alessandro-satanassi/OpenFIRE-PICON-ESP32/web/images/010---telaio_sotto_pompa_posteriore.png

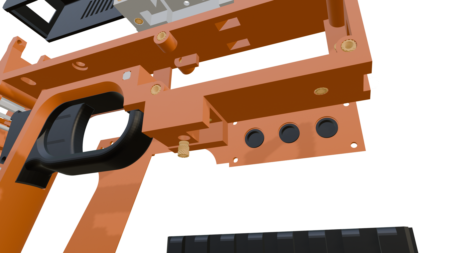
web/images/010---telaio_sotto_pompa_posteriore.png
