alessandro-satanassi/OpenFIRE-PICON-ESP32/web/images/viti_testa_piatta.jpg

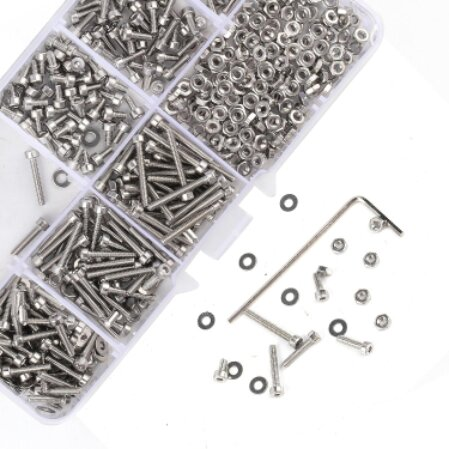
web/images/viti_testa_piatta.jpg
