alessandro-satanassi/OpenFIRE-PICON-ESP32/web/files/006---supporto_solenoide_dx.png

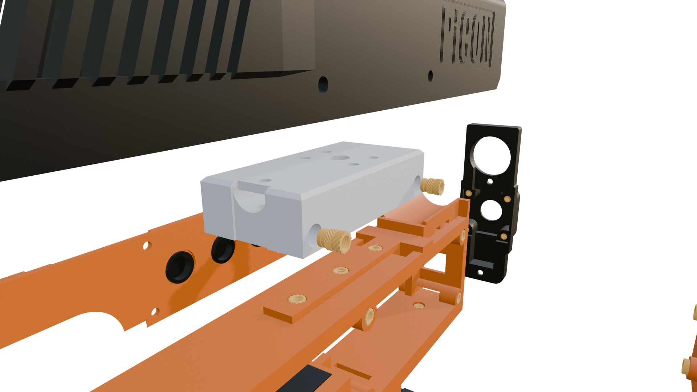
web/files/006---supporto_solenoide_dx.png
