alessandro-satanassi/OpenFIRE-PICON-ESP32/web/files/06_cc05z4l9.jpeg

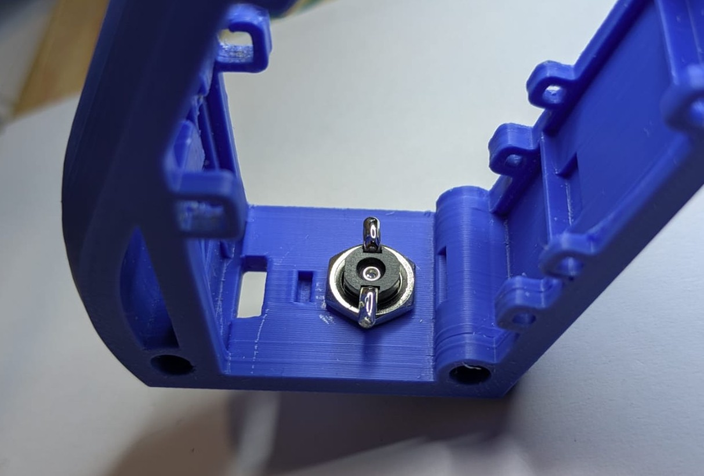
web/files/06_cc05z4l9.jpeg
