alessandro-satanassi/OpenFIRE-PICON-ESP32/web/gallery/06.jpg

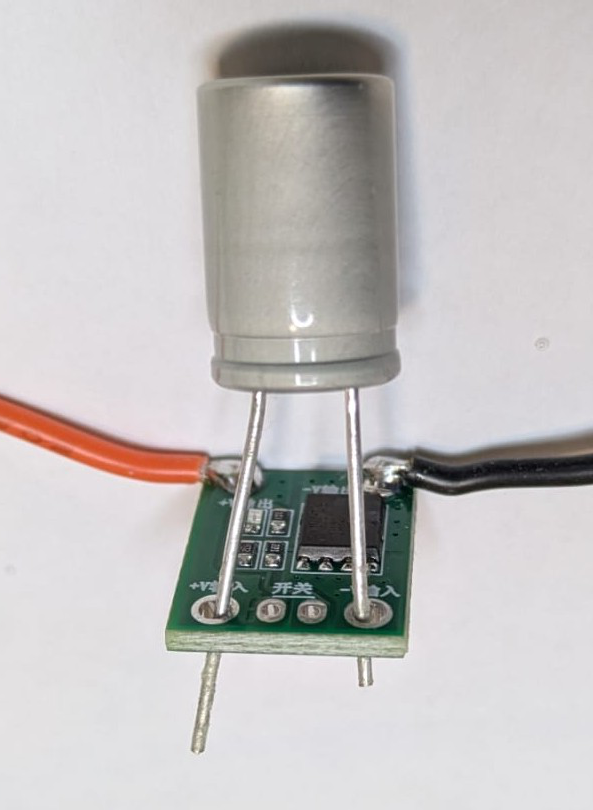
web/gallery/06.jpg
