alessandro-satanassi/OpenFIRE-PICON-ESP32/web/gallery/06_thumb_eejymhjs.png

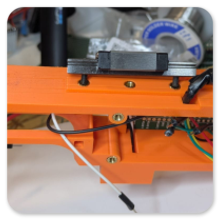
web/gallery/06_thumb_eejymhjs.png
