alessandro-satanassi/OpenFIRE-PICON-ESP32/web/gallery/10_thumb_l9mox1hs.png

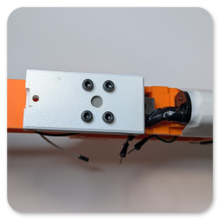
web/gallery/10_thumb_l9mox1hs.png
