alessandro-satanassi/OpenFIRE-PICON-ESP32/web/gallery/10_thumb_tlurzcni.png

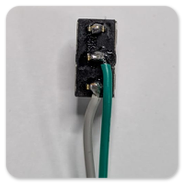
web/gallery/10_thumb_tlurzcni.png
