alessandro-satanassi/OpenFIRE-PICON-ESP32/web/gallery/16_thumb_evzkav5x.png

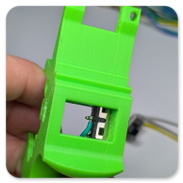
web/gallery/16_thumb_evzkav5x.png
