alessandro-satanassi/OpenFIRE-PICON-ESP32/web/gallery/17.jpg

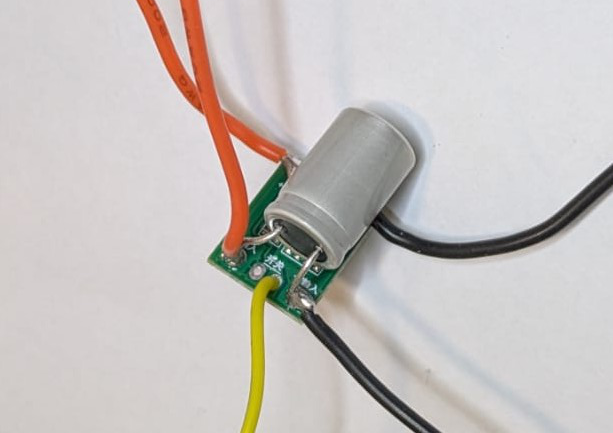
web/gallery/17.jpg
