alessandro-satanassi/OpenFIRE-PICON-ESP32/web/gallery/WhatsApp-Image-2026-08-09-at-01.59.08--3-.jpg

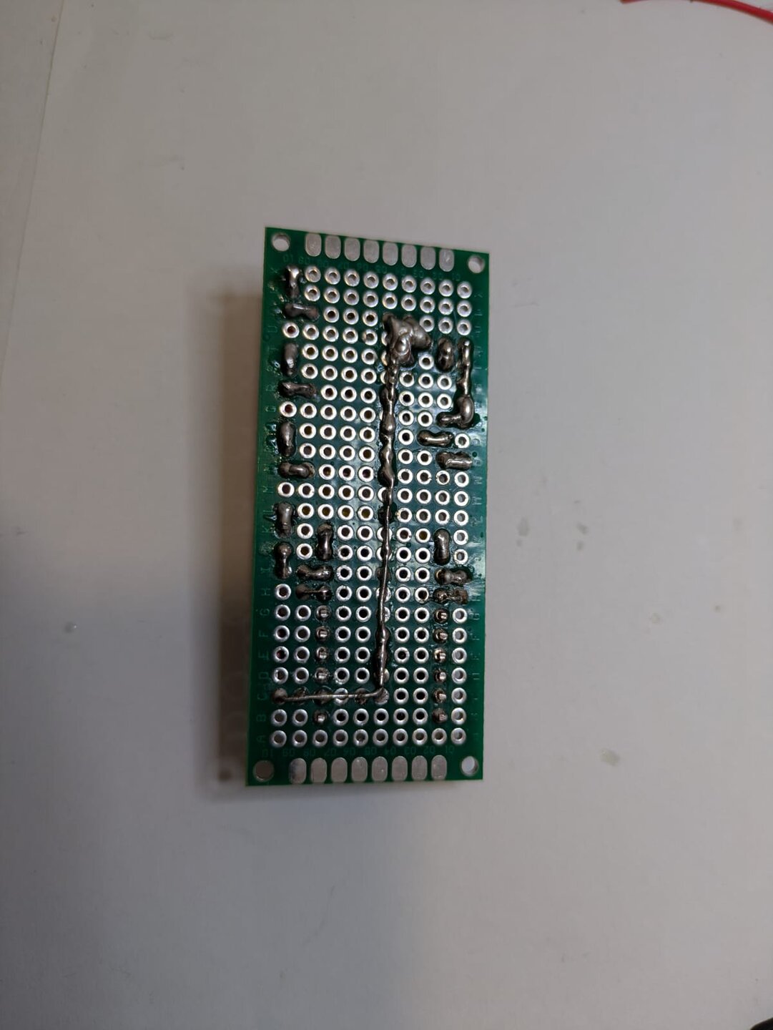
web/gallery/WhatsApp-Image-2026-08-09-at-01.59.08--3-.jpg
