alessandro-satanassi/OpenFIRE-PICON-ESP32/web/images/00.jpg

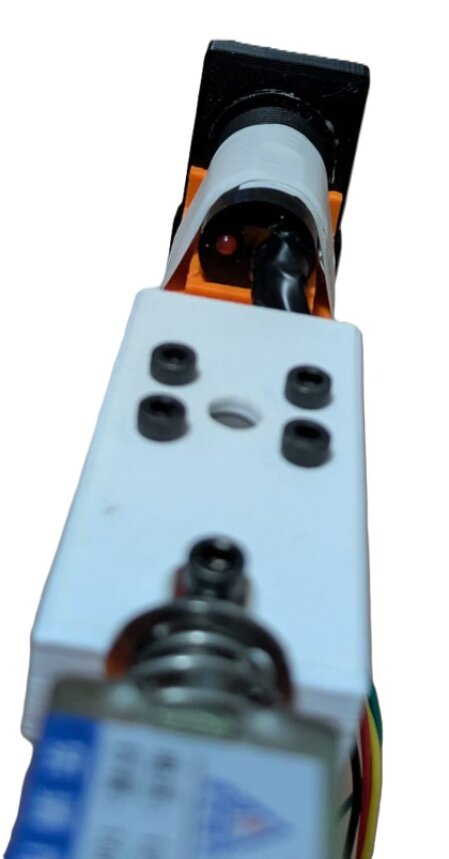
web/images/00.jpg
