alessandro-satanassi/OpenFIRE-PICON-ESP32/web/images/001---blocco-guida-rail.png

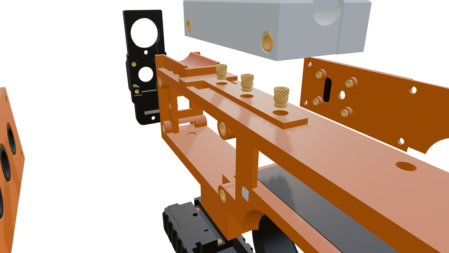
web/images/001---blocco-guida-rail.png
