alessandro-satanassi/OpenFIRE-PICON-ESP32/web/images/01.jpg

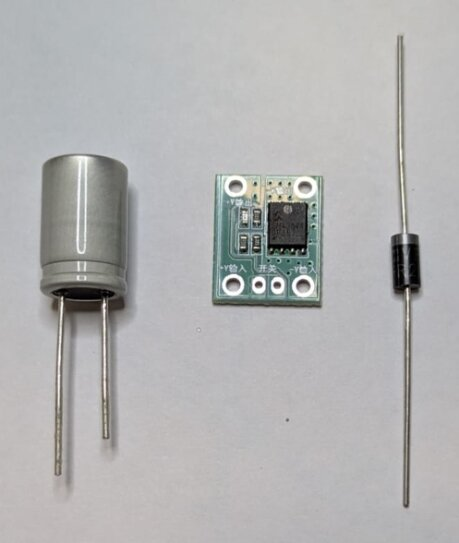
web/images/01.jpg
