alessandro-satanassi/OpenFIRE-PICON-ESP32/web/images/1.jpg

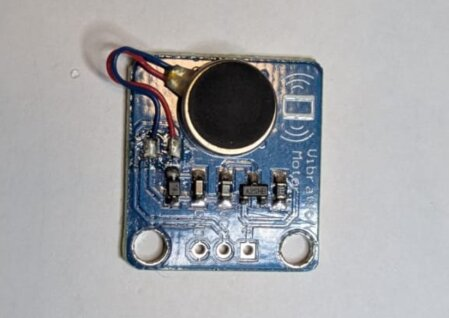
web/images/1.jpg
