alessandro-satanassi/OpenFIRE-PICON-ESP32/web/images/01_2w0nyasc.jpg

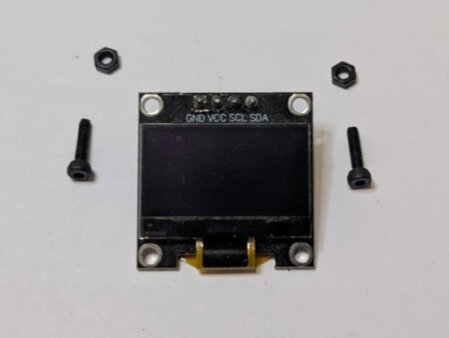
web/images/01_2w0nyasc.jpg
