alessandro-satanassi/OpenFIRE-PICON-ESP32/web/images/01_5xzmrs7f.jpg

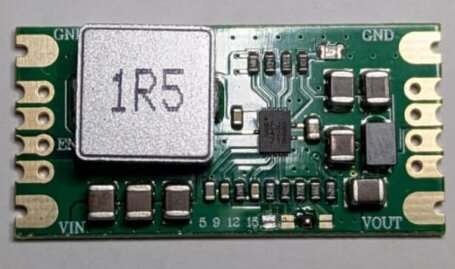
web/images/01_5xzmrs7f.jpg
