alessandro-satanassi/OpenFIRE-PICON-ESP32/web/images/01_8k7r30k3.jpg

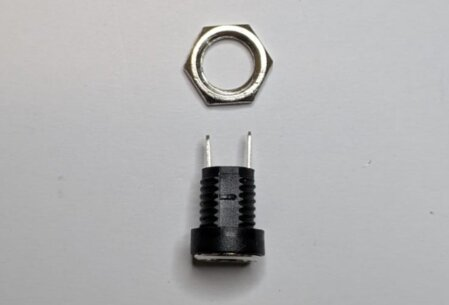
web/images/01_8k7r30k3.jpg
