alessandro-satanassi/OpenFIRE-PICON-ESP32/web/images/01_8mr3n87f.jpg

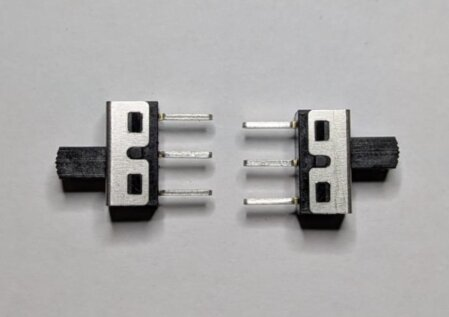
web/images/01_8mr3n87f.jpg
