alessandro-satanassi/OpenFIRE-PICON-ESP32/web/files/01_0ub3t0rs.jpeg

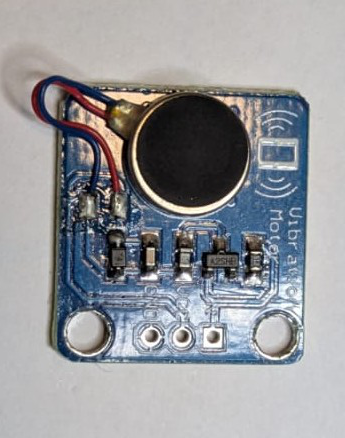
web/images/01_f4iyjq4a.jpg
