alessandro-satanassi/OpenFIRE-PICON-ESP32/web/files/01_5zxbnlnv.jpeg

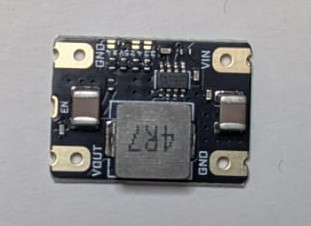
web/images/01_g9jfmoby.jpg
