alessandro-satanassi/OpenFIRE-PICON-ESP32/web/images/01_GRILLETTO.jpg

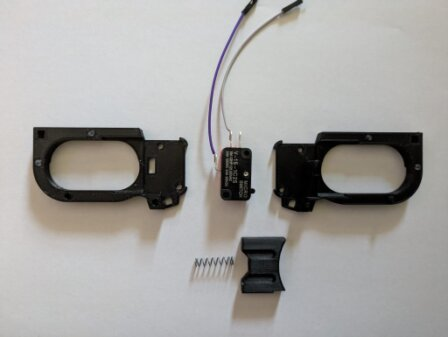
web/images/01_GRILLETTO.jpg
