alessandro-satanassi/OpenFIRE-PICON-ESP32/web/images/01_LENTE.jpg

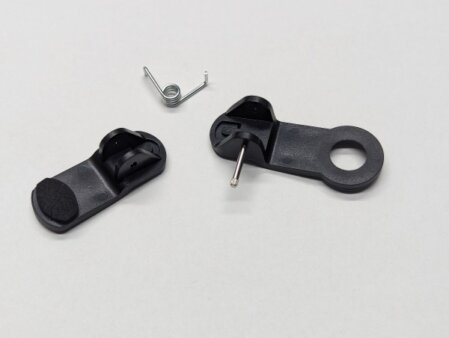
web/images/01_LENTE.jpg
