alessandro-satanassi/OpenFIRE-PICON-ESP32/web/images/01_mn38d8ug.jpg

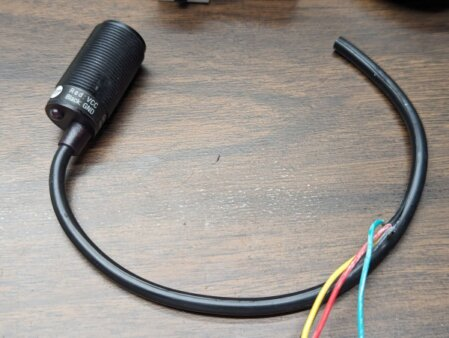
web/images/01_mn38d8ug.jpg
