alessandro-satanassi/OpenFIRE-PICON-ESP32/web/images/01_neopixel.jpg

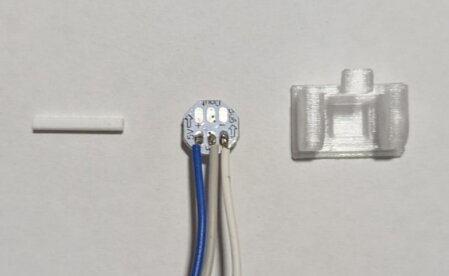
web/images/01_neopixel.jpg
