alessandro-satanassi/OpenFIRE-PICON-ESP32/web/images/01_POMPA.jpg

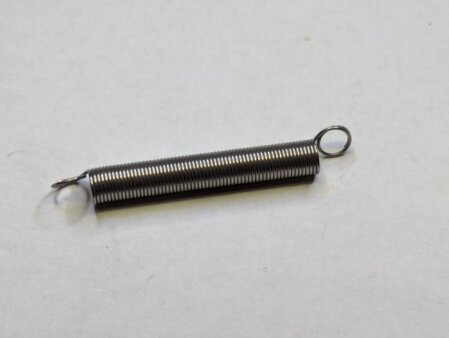
web/images/01_POMPA.jpg
