alessandro-satanassi/OpenFIRE-PICON-ESP32/web/images/01_switch_pompa.jpg

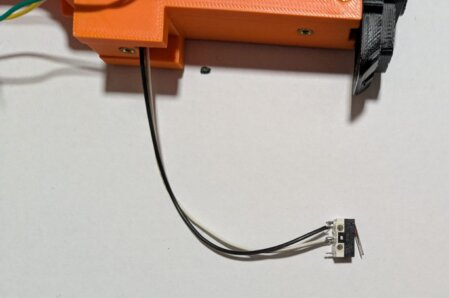
web/images/01_switch_pompa.jpg
