alessandro-satanassi/OpenFIRE-PICON-ESP32/web/images/002---telaio_sx.png

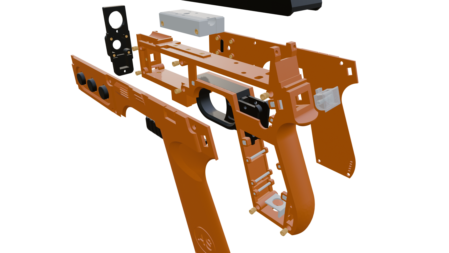
web/images/002---telaio_sx.png
