alessandro-satanassi/OpenFIRE-PICON-ESP32/web/images/02.jpg

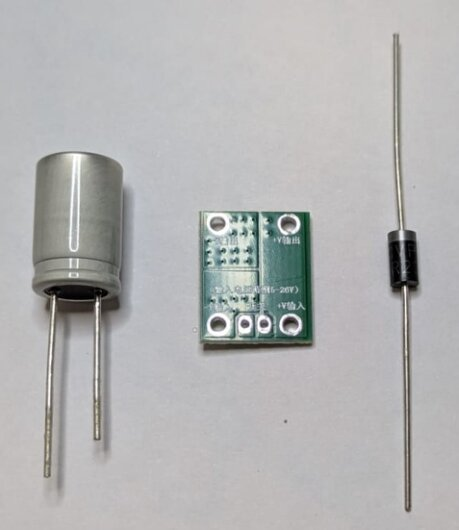
web/images/02.jpg
