alessandro-satanassi/OpenFIRE-PICON-ESP32/web/images/2.jpg

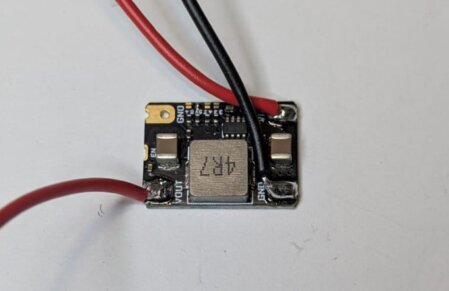
web/images/2.jpg
