alessandro-satanassi/OpenFIRE-PICON-ESP32/web/files/02_2sauoesy.jpeg

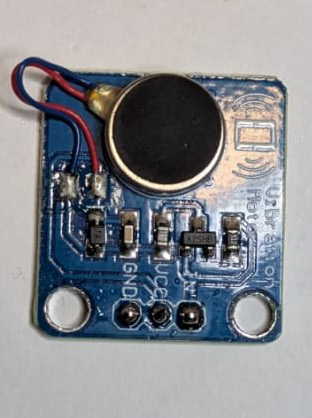
web/images/02_4r1xh5xk.jpg
