alessandro-satanassi/OpenFIRE-PICON-ESP32/web/files/02_3oflzan2.jpeg

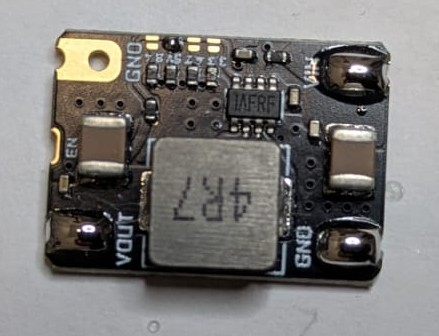
web/images/02_5logg1c5.jpg
