alessandro-satanassi/OpenFIRE-PICON-ESP32/web/images/02_GRILLETTO.jpg

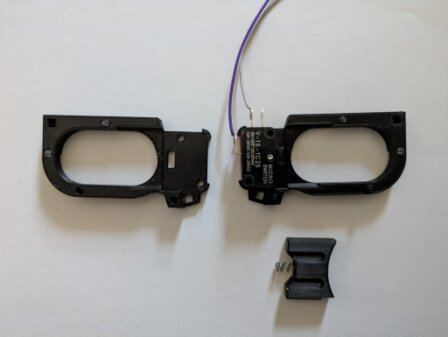
web/images/02_GRILLETTO.jpg
