alessandro-satanassi/OpenFIRE-PICON-ESP32/web/images/02_LENTE.jpg

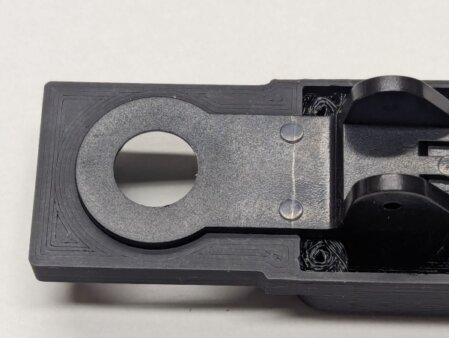
web/images/02_LENTE.jpg
