alessandro-satanassi/OpenFIRE-PICON-ESP32/web/images/02_neopixel.jpg

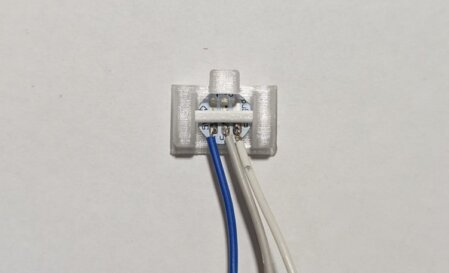
web/images/02_neopixel.jpg
