alessandro-satanassi/OpenFIRE-PICON-ESP32/web/images/02_POMPA.jpg

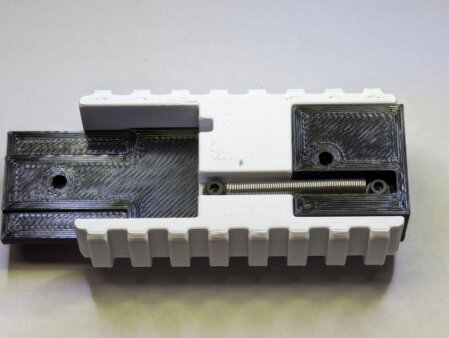
web/images/02_POMPA.jpg
