alessandro-satanassi/OpenFIRE-PICON-ESP32/web/images/02_r8t4q5sc.jpg

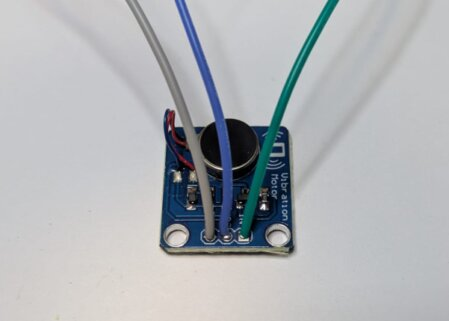
web/images/02_r8t4q5sc.jpg
