alessandro-satanassi/OpenFIRE-PICON-ESP32/web/images/02_ruzfydre.jpg

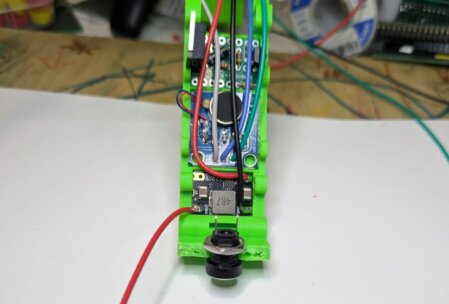
web/images/02_ruzfydre.jpg
