alessandro-satanassi/OpenFIRE-PICON-ESP32/web/images/02_sebupyjk.jpg

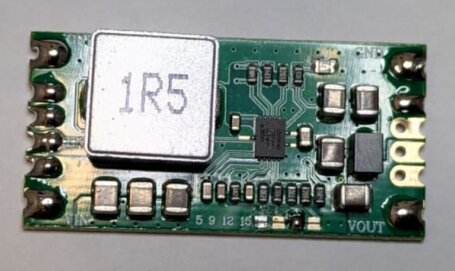
web/images/02_sebupyjk.jpg
