alessandro-satanassi/OpenFIRE-PICON-ESP32/web/images/02_switch_pompa.jpg

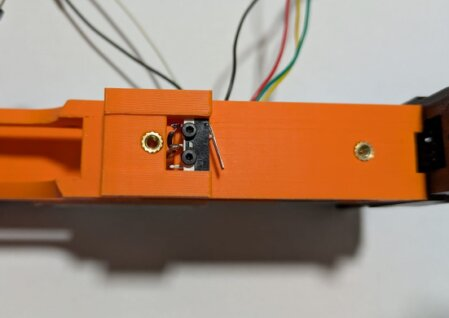
web/images/02_switch_pompa.jpg
