alessandro-satanassi/OpenFIRE-PICON-ESP32/web/images/02_t7jg1n2v.jpg

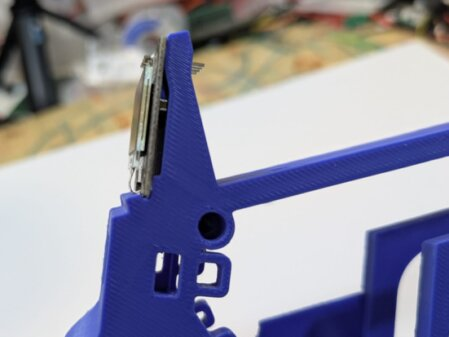
web/images/02_t7jg1n2v.jpg
