alessandro-satanassi/OpenFIRE-PICON-ESP32/web/images/02_ymkqmdek.jpg

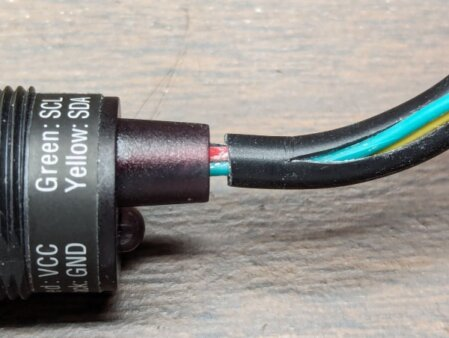
web/images/02_ymkqmdek.jpg
