alessandro-satanassi/OpenFIRE-PICON-ESP32/web/images/02_yrchzzac.jpg

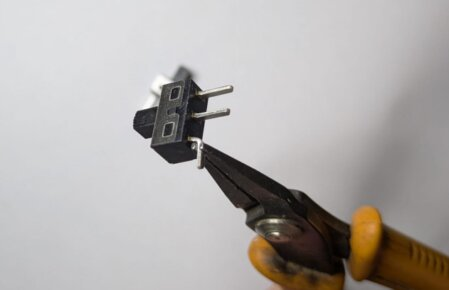
web/images/02_yrchzzac.jpg
