alessandro-satanassi/OpenFIRE-PICON-ESP32/web/images/003---telaio_dx.png

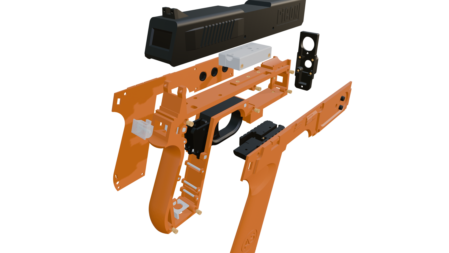
web/images/003---telaio_dx.png
