alessandro-satanassi/OpenFIRE-PICON-ESP32/web/images/03.jpg

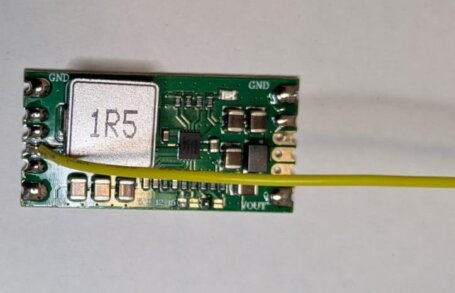
web/images/03.jpg
