alessandro-satanassi/OpenFIRE-PICON-ESP32/web/images/3.jpg

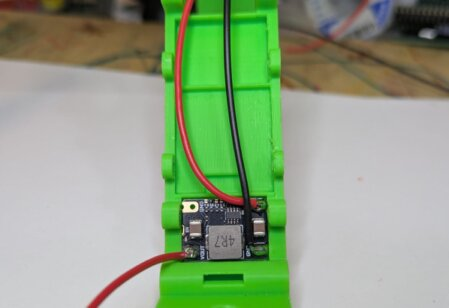
web/images/3.jpg
