alessandro-satanassi/OpenFIRE-PICON-ESP32/web/images/003.png

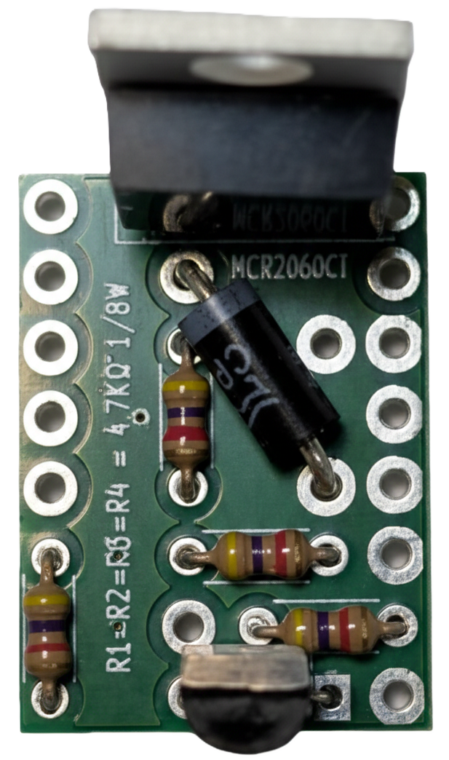
web/images/003.png
