alessandro-satanassi/OpenFIRE-PICON-ESP32/web/images/03_524w5b3q.jpg

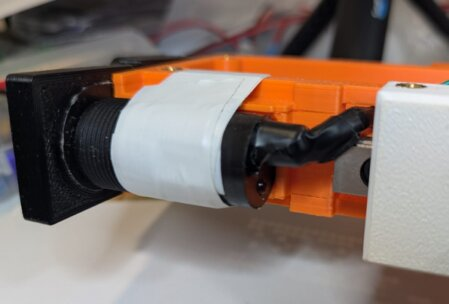
web/images/03_524w5b3q.jpg
