alessandro-satanassi/OpenFIRE-PICON-ESP32/web/images/03_gcl5vufi.jpg

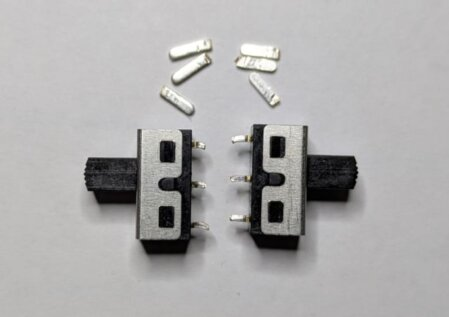
web/images/03_gcl5vufi.jpg
