alessandro-satanassi/OpenFIRE-PICON-ESP32/web/images/03_GRILLETTO.jpg

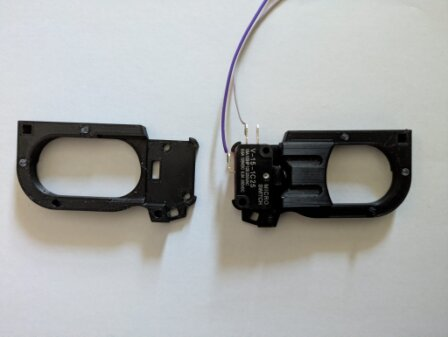
web/images/03_GRILLETTO.jpg
