alessandro-satanassi/OpenFIRE-PICON-ESP32/web/images/03_iws1d3v5.jpg

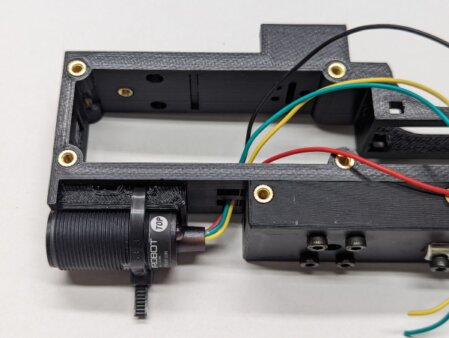
web/images/03_iws1d3v5.jpg
