alessandro-satanassi/OpenFIRE-PICON-ESP32/web/images/03_LENTE.jpg

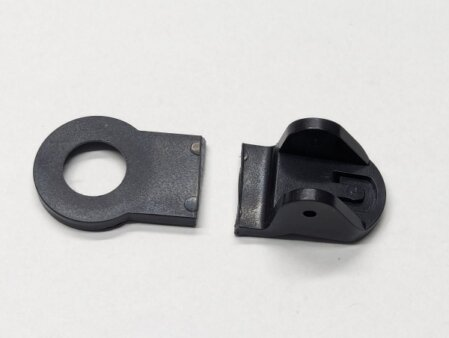
web/images/03_LENTE.jpg
