alessandro-satanassi/OpenFIRE-PICON-ESP32/web/images/03_lwsuhsz6.jpg

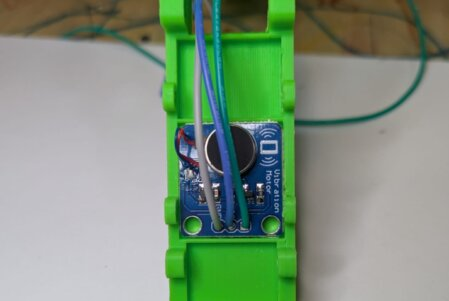
web/images/03_lwsuhsz6.jpg
