alessandro-satanassi/OpenFIRE-PICON-ESP32/web/images/03_neopixel.jpg

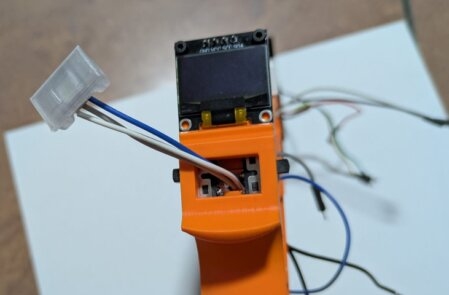
web/images/03_neopixel.jpg
