alessandro-satanassi/OpenFIRE-PICON-ESP32/web/images/03_pfckra2t.jpg

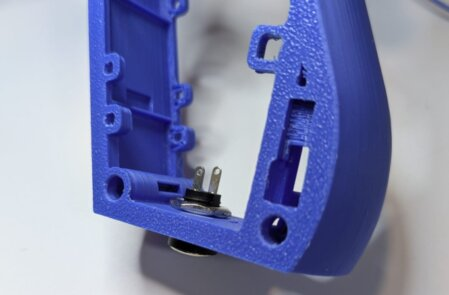
web/images/03_pfckra2t.jpg
