alessandro-satanassi/OpenFIRE-PICON-ESP32/web/images/03_POMPA.jpg

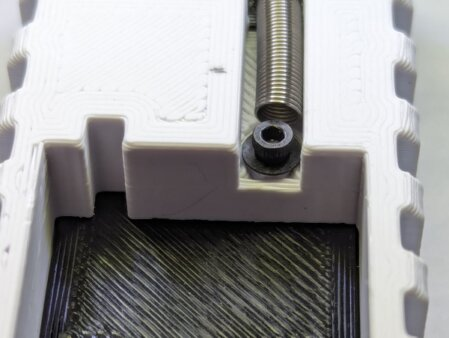
web/images/03_POMPA.jpg
