alessandro-satanassi/OpenFIRE-PICON-ESP32/web/images/03_sllk6pq8.jpg

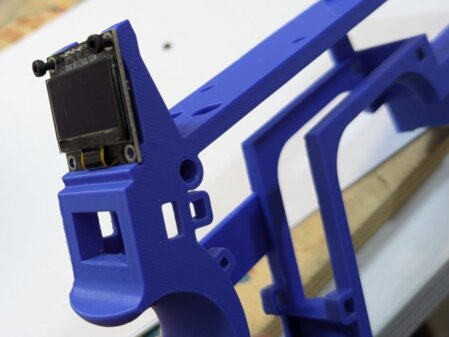
web/images/03_sllk6pq8.jpg
