alessandro-satanassi/OpenFIRE-PICON-ESP32/web/images/03_switch_pompa.jpg

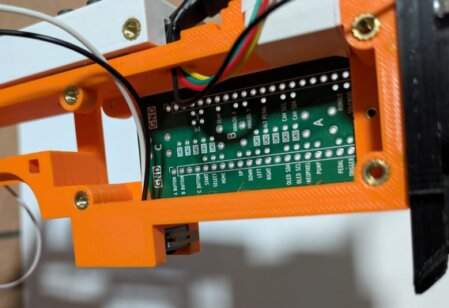
web/images/03_switch_pompa.jpg
