alessandro-satanassi/OpenFIRE-PICON-ESP32/web/images/004---blocco-braccio-solenoide.png

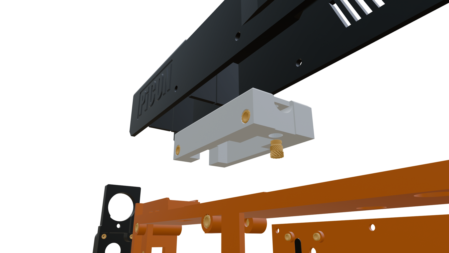
web/images/004---blocco-braccio-solenoide.png
