alessandro-satanassi/OpenFIRE-PICON-ESP32/web/images/04.jpg

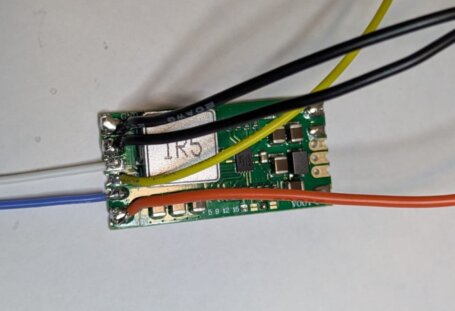
web/images/04.jpg
