alessandro-satanassi/OpenFIRE-PICON-ESP32/web/images/04_2t98dg83.jpg

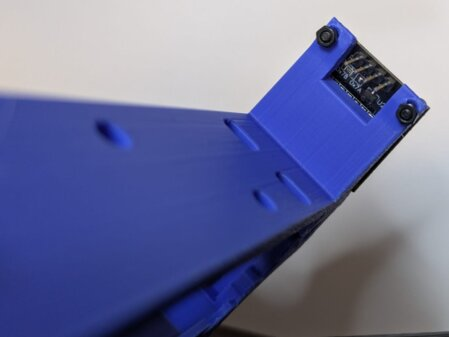
web/images/04_2t98dg83.jpg
