alessandro-satanassi/OpenFIRE-PICON-ESP32/web/images/04_GRILLETTO.jpg

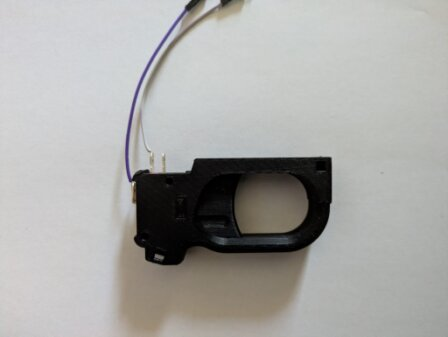
web/images/04_GRILLETTO.jpg
