alessandro-satanassi/OpenFIRE-PICON-ESP32/web/images/04_LENTE.jpg

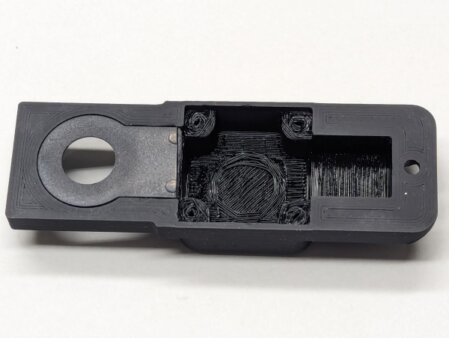
web/images/04_LENTE.jpg
