alessandro-satanassi/OpenFIRE-PICON-ESP32/web/images/04_n981k5cl.jpg

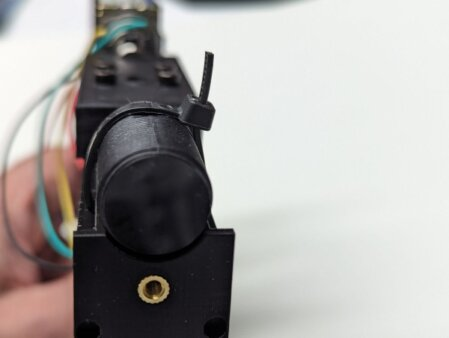
web/images/04_n981k5cl.jpg
