alessandro-satanassi/OpenFIRE-PICON-ESP32/web/images/04_neopixel.jpg

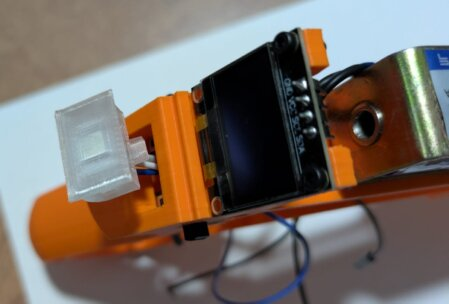
web/images/04_neopixel.jpg
