alessandro-satanassi/OpenFIRE-PICON-ESP32/web/images/04_nu273c6r.jpg

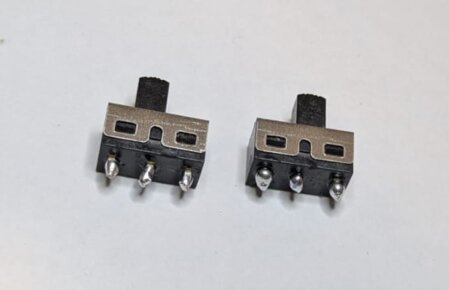
web/images/04_nu273c6r.jpg
