alessandro-satanassi/OpenFIRE-PICON-ESP32/web/images/04_u2wgebxg.jpg

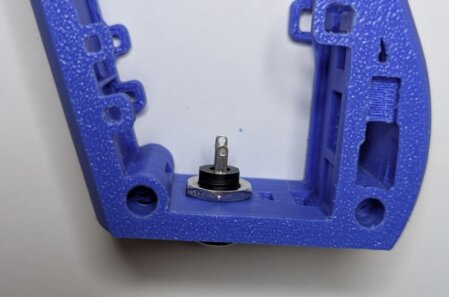
web/images/04_u2wgebxg.jpg
