alessandro-satanassi/OpenFIRE-PICON-ESP32/web/images/005---supporto_solenoide_sx.png

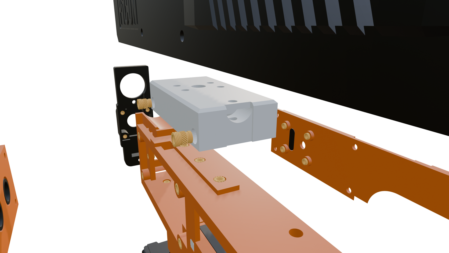
web/images/005---supporto_solenoide_sx.png
