alessandro-satanassi/OpenFIRE-PICON-ESP32/web/images/05.jpg

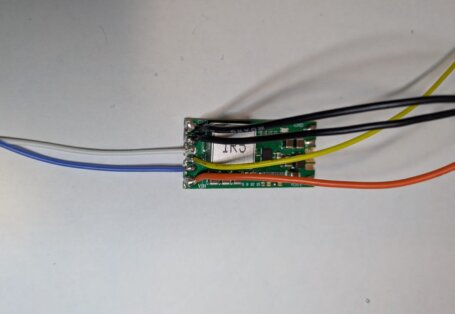
web/images/05.jpg
