alessandro-satanassi/OpenFIRE-PICON-ESP32/web/images/005.png

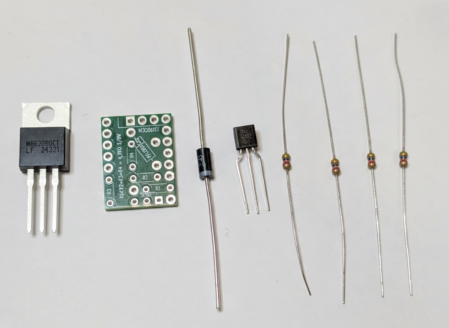
web/images/005.png
