alessandro-satanassi/OpenFIRE-PICON-ESP32/web/images/05_bi0squd6.jpg

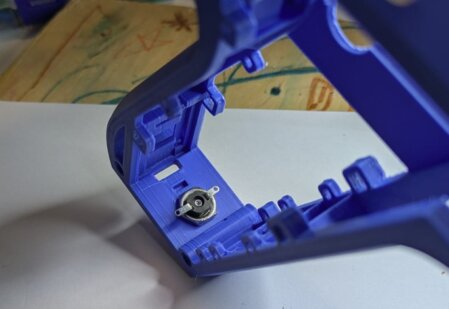
web/images/05_bi0squd6.jpg
