alessandro-satanassi/OpenFIRE-PICON-ESP32/web/images/05_diop4fx3.jpg

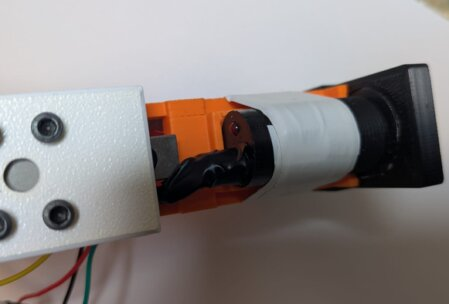
web/images/05_diop4fx3.jpg
