alessandro-satanassi/OpenFIRE-PICON-ESP32/web/images/05_GRILLETTO.jpg

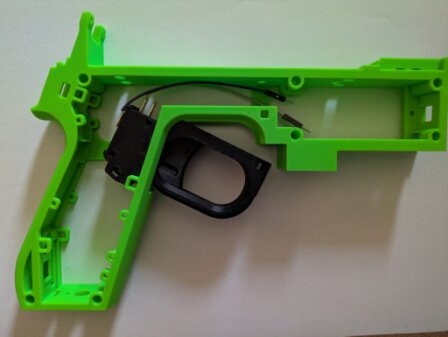
web/images/05_GRILLETTO.jpg
