alessandro-satanassi/OpenFIRE-PICON-ESP32/web/images/05_LENTE.jpg

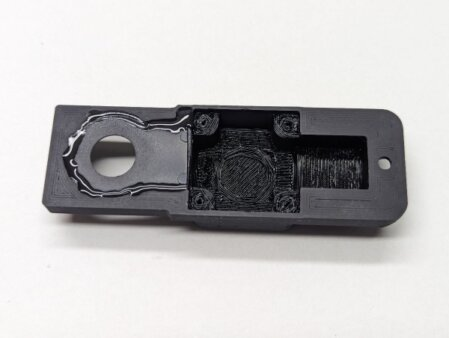
web/images/05_LENTE.jpg
