alessandro-satanassi/OpenFIRE-PICON-ESP32/web/images/05_neopixel.jpg

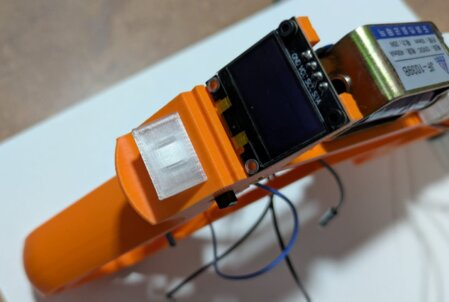
web/images/05_neopixel.jpg
