alessandro-satanassi/OpenFIRE-PICON-ESP32/web/images/05_odr75ruc.jpg

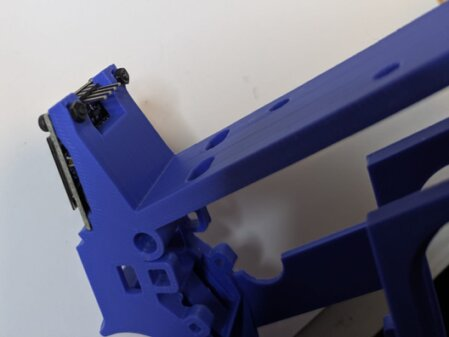
web/images/05_odr75ruc.jpg
