alessandro-satanassi/OpenFIRE-PICON-ESP32/web/images/06.jpg

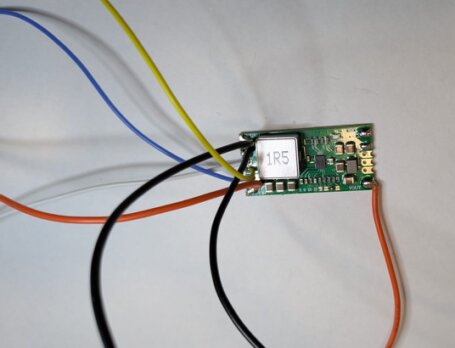
web/images/06.jpg
