alessandro-satanassi/OpenFIRE-PICON-ESP32/web/images/06_d0qdcc5i.jpg

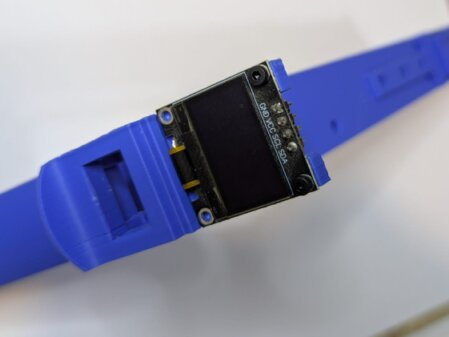
web/images/06_d0qdcc5i.jpg
