alessandro-satanassi/OpenFIRE-PICON-ESP32/web/images/06_GRILLETTO.jpg

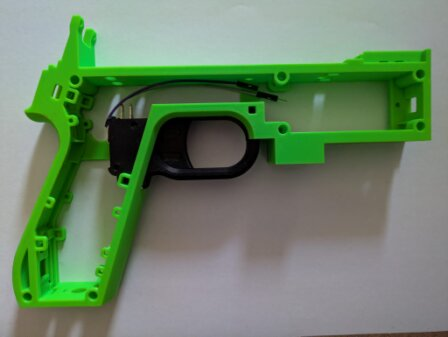
web/images/06_GRILLETTO.jpg
