alessandro-satanassi/OpenFIRE-PICON-ESP32/web/images/06_LENTE.jpg

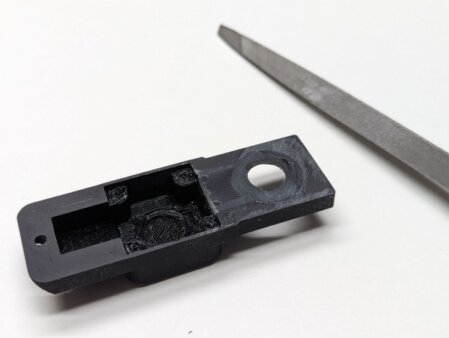
web/images/06_LENTE.jpg
