alessandro-satanassi/OpenFIRE-PICON-ESP32/web/images/06_neopixel.jpg

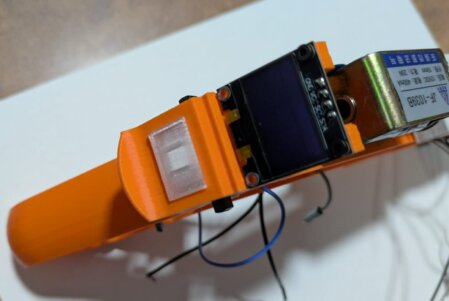
web/images/06_neopixel.jpg
