alessandro-satanassi/OpenFIRE-PICON-ESP32/web/images/06_vsywxsd8.jpg

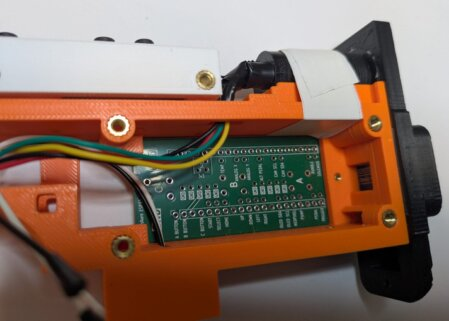
web/images/06_vsywxsd8.jpg
