alessandro-satanassi/OpenFIRE-PICON-ESP32/web/images/007---supporto_micro.png

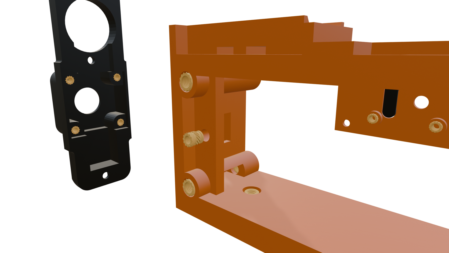
web/images/007---supporto_micro.png
