alessandro-satanassi/OpenFIRE-PICON-ESP32/web/images/07.jpg

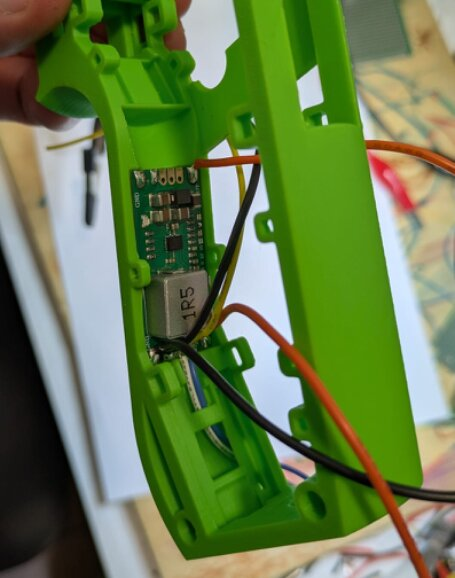
web/images/07.jpg
