alessandro-satanassi/OpenFIRE-PICON-ESP32/web/images/008---anteriore_telaio.png

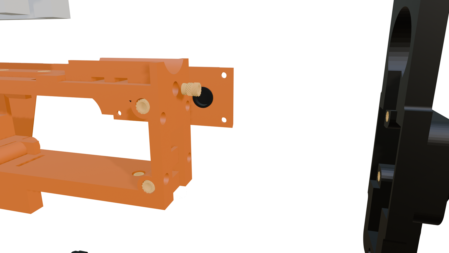
web/images/008---anteriore_telaio.png
