alessandro-satanassi/OpenFIRE-PICON-ESP32/web/images/08.jpg

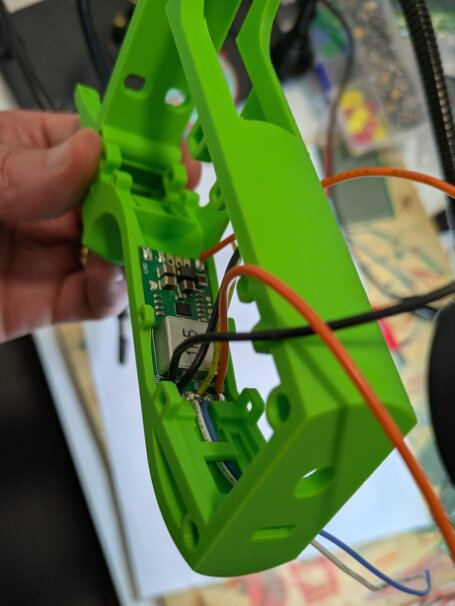
web/images/08.jpg
