alessandro-satanassi/OpenFIRE-PICON-ESP32/web/images/009---telaio_sotto_pompa_anteriore.png

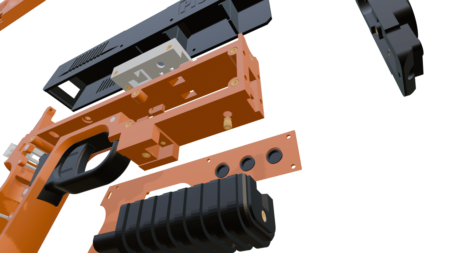
web/images/009---telaio_sotto_pompa_anteriore.png
