alessandro-satanassi/OpenFIRE-PICON-ESP32/web/images/09.jpg

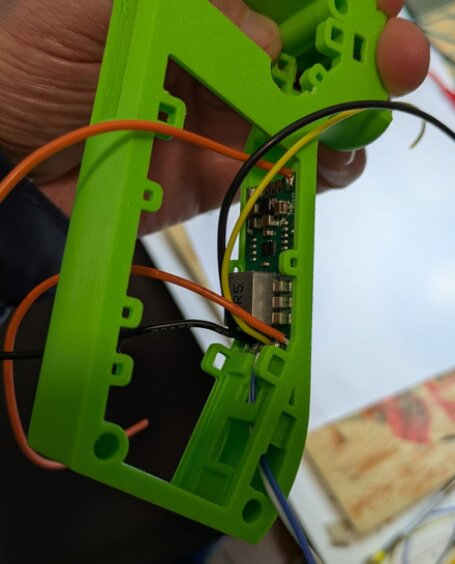
web/images/09.jpg
