alessandro-satanassi/OpenFIRE-PICON-ESP32/web/images/011---telaio_sotto_pompa_vlocco_switch.png

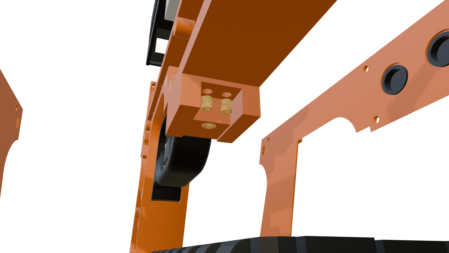
web/images/011---telaio_sotto_pompa_vlocco_switch.png
