alessandro-satanassi/OpenFIRE-PICON-ESP32/web/images/012---lato_dx_dpad_5d.png

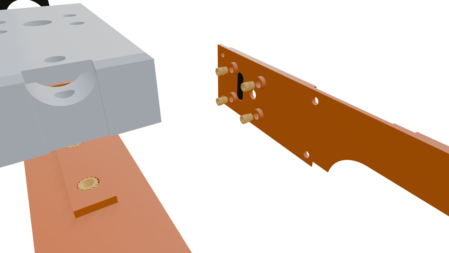
web/images/012---lato_dx_dpad_5d.png
