alessandro-satanassi/OpenFIRE-PICON-ESP32/web/images/013---supporto_joystick.png

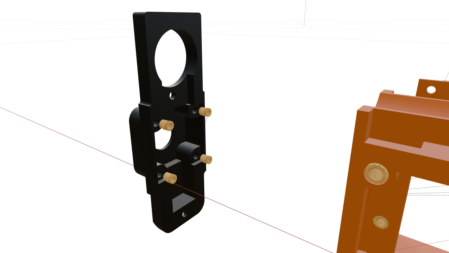
web/images/013---supporto_joystick.png
