alessandro-satanassi/OpenFIRE-PICON-ESP32/web/images/014---meccanismo_pompa_frontale.png

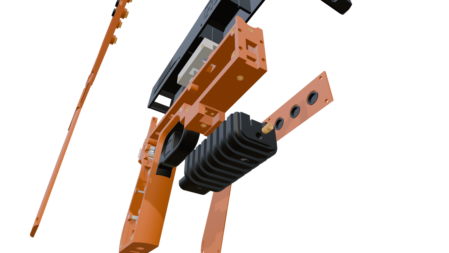
web/images/014---meccanismo_pompa_frontale.png
