alessandro-satanassi/OpenFIRE-PICON-ESP32/web/images/015---meccanismo_pompa_fermi_molla.png

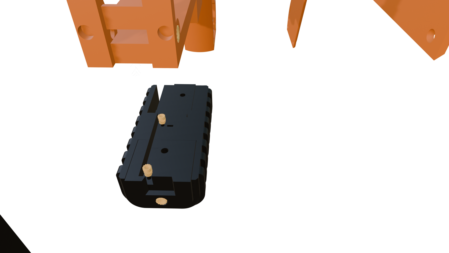
web/images/015---meccanismo_pompa_fermi_molla.png
