alessandro-satanassi/OpenFIRE-PICON-ESP32/web/images/Adafruit-BQ25185_7053r53b.png

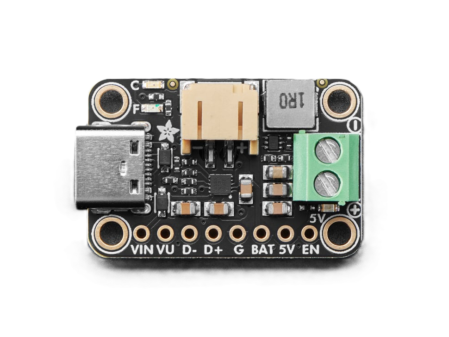
web/images/Adafruit-BQ25185_7053r53b.png
