alessandro-satanassi/OpenFIRE-PICON-ESP32/web/images/alimentatore_USB_5V_1A.png

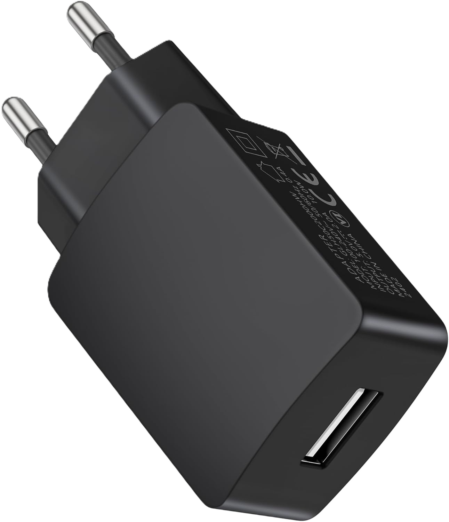
web/images/alimentatore_USB_5V_1A.png
