alessandro-satanassi/OpenFIRE-PICON-ESP32/web/images/alimentazione_3D_lato_componenti.jpg

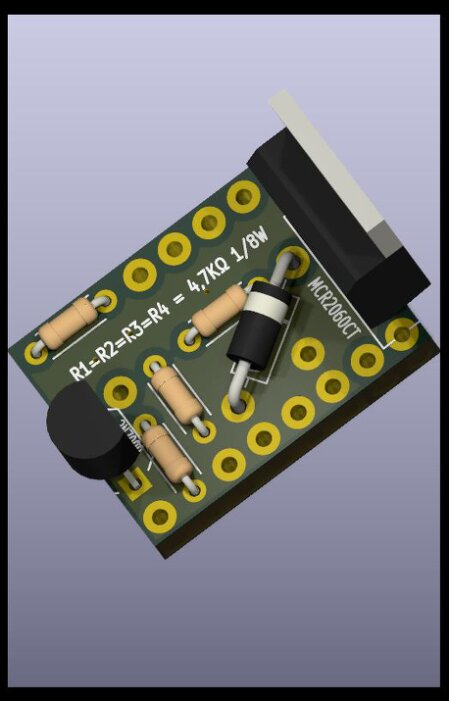
web/images/alimentazione_3D_lato_componenti.jpg
