alessandro-satanassi/OpenFIRE-PICON-ESP32/web/images/Base.png

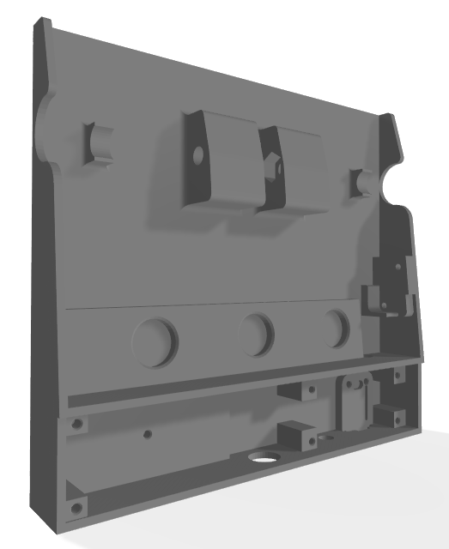
web/images/Base.png
