alessandro-satanassi/OpenFIRE-PICON-ESP32/web/images/Base_Batt.png

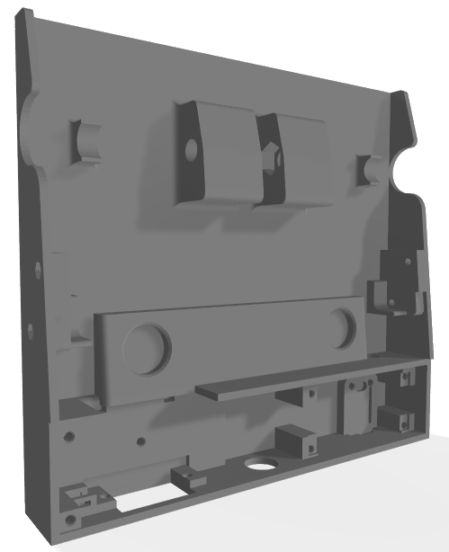
web/images/Base_Batt.png
