alessandro-satanassi/OpenFIRE-PICON-ESP32/web/images/basetta_millefori.png

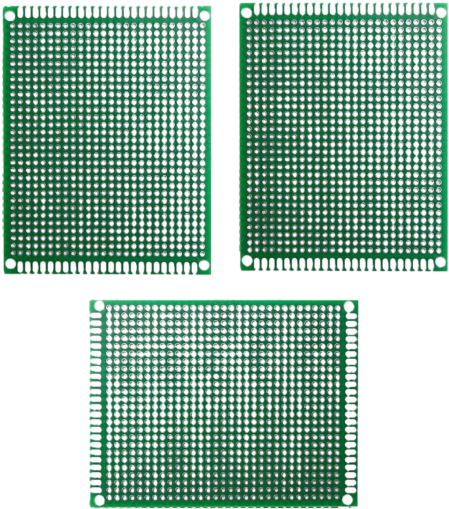
web/images/basetta_millefori.png
