alessandro-satanassi/OpenFIRE-PICON-ESP32/web/images/basetta_millefori_24x10fori_7x3cm.png

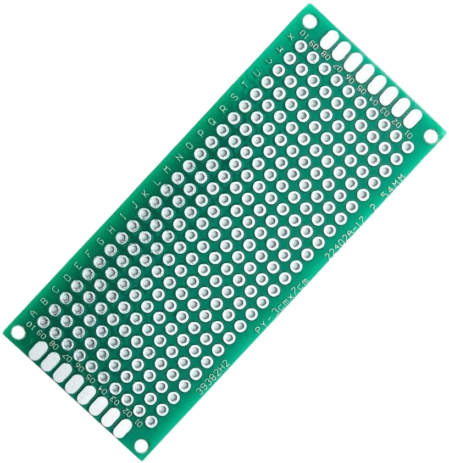
web/images/basetta_millefori_24x10fori_7x3cm.png
