alessandro-satanassi/OpenFIRE-PICON-ESP32/web/images/batteria_18650_li-ion.png

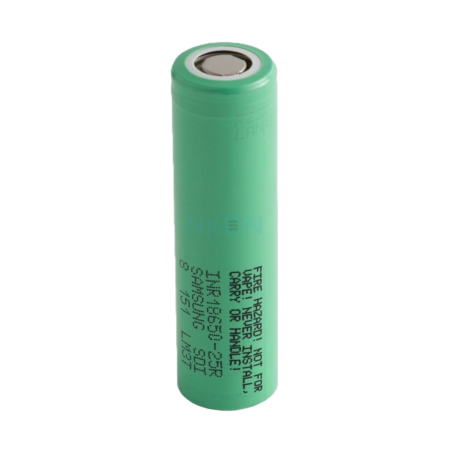
web/images/batteria_18650_li-ion.png
