alessandro-satanassi/OpenFIRE-PICON-ESP32/web/images/batteria_con_alette_U.png

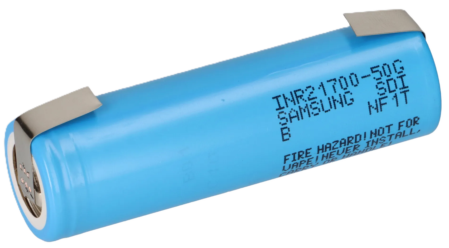
web/images/batteria_con_alette_U.png
