alessandro-satanassi/OpenFIRE-PICON-ESP32/web/images/bearing-solenoid-mount_9fe4su14.png

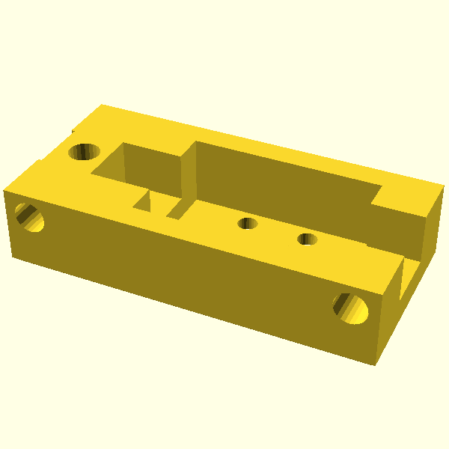
web/images/bearing-solenoid-mount_9fe4su14.png
