alessandro-satanassi/OpenFIRE-PICON-ESP32/web/images/Button-Cap.png

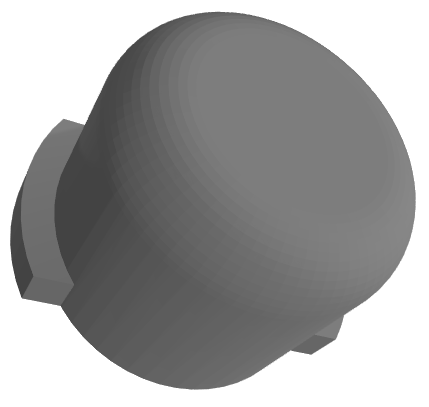
web/images/Button-Cap.png
