alessandro-satanassi/OpenFIRE-PICON-ESP32/web/images/CAM-dfrobot-SEN0158---2.png

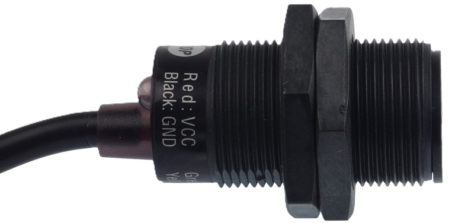
web/images/CAM-dfrobot-SEN0158---2.png
