alessandro-satanassi/OpenFIRE-PICON-ESP32/web/images/case_ir_led_tx_ver_04-Corpo.png

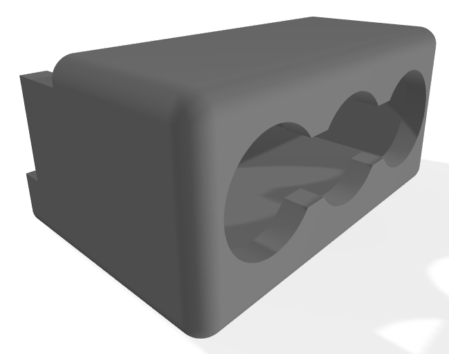
web/images/case_ir_led_tx_ver_04-Corpo.png
