alessandro-satanassi/OpenFIRE-PICON-ESP32/web/images/cavo-con-connettore-JST-PHR02-2P-femmina.png

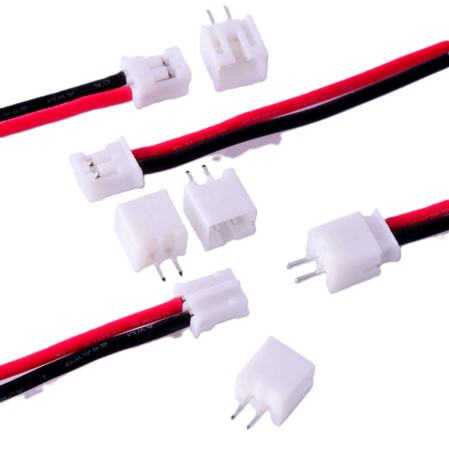
web/images/cavo-con-connettore-JST-PHR02-2P-femmina.png
