alessandro-satanassi/OpenFIRE-PICON-ESP32/web/images/cavo-USB-C.png

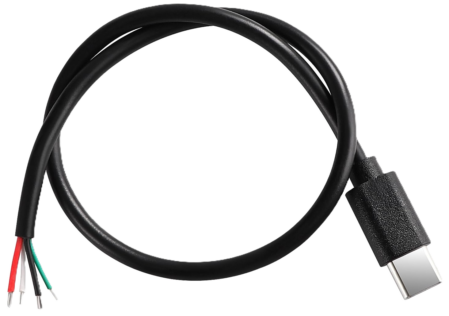
web/images/cavo-USB-C.png
