alessandro-satanassi/OpenFIRE-PICON-ESP32/web/images/cavo_usb_c.png

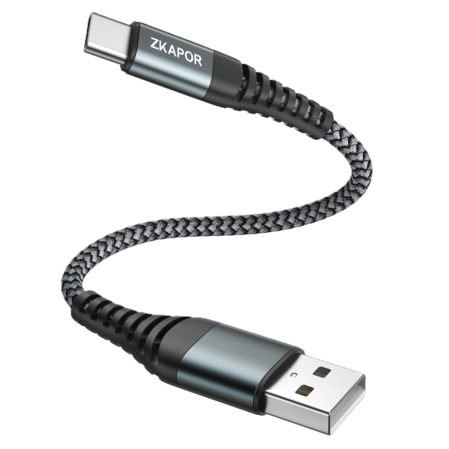
web/images/cavo_usb_c.png
