alessandro-satanassi/OpenFIRE-PICON-ESP32/web/images/circuito_path_control---ORRIZZONTALE---TAGLIATO.png

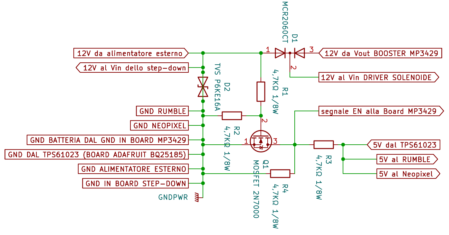
web/images/circuito_path_control---ORRIZZONTALE---TAGLIATO.png
