alessandro-satanassi/OpenFIRE-PICON-ESP32/web/images/CIRCUITO_PATH_CURRENT.jpeg.png

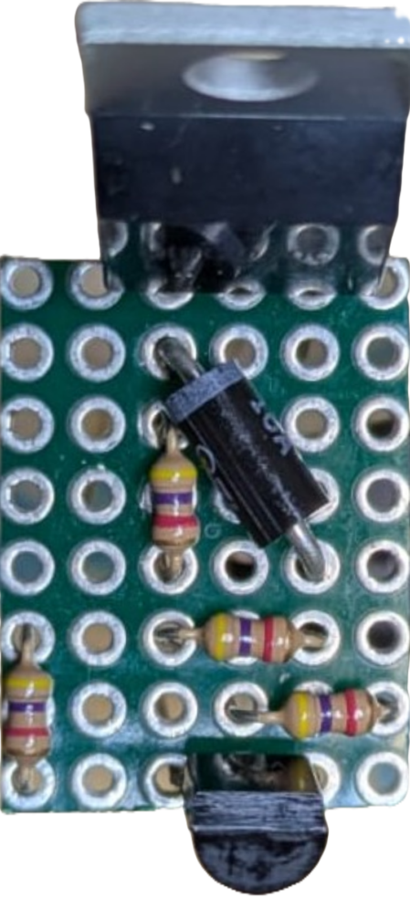
web/images/CIRCUITO_PATH_CURRENT.jpeg.png
