alessandro-satanassi/OpenFIRE-PICON-ESP32/web/images/condensatore-100nf.png

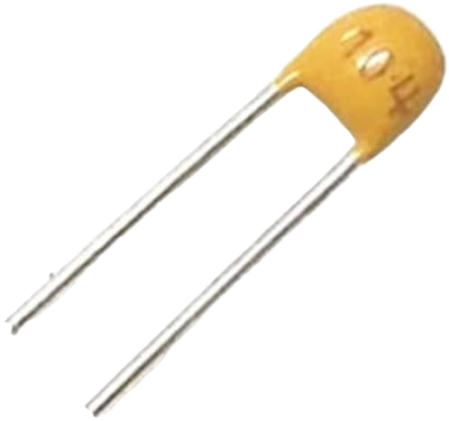
web/images/condensatore-100nf.png
