alessandro-satanassi/OpenFIRE-PICON-ESP32/web/images/condensatore-470uF-25V-polimerico-low-esr.png

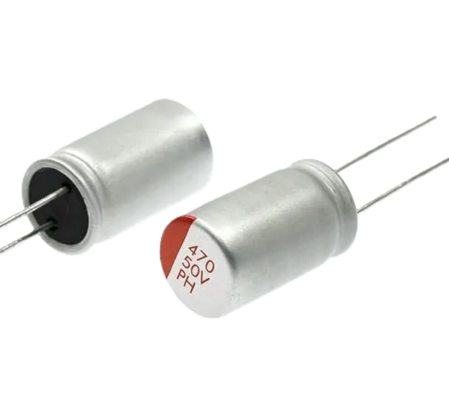
web/images/condensatore-470uF-25V-polimerico-low-esr.png
