alessandro-satanassi/OpenFIRE-PICON-ESP32/web/images/connettori-BT2.0.png

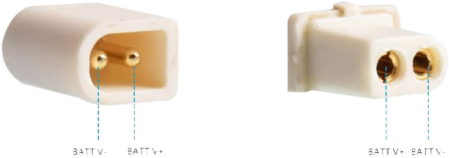
web/images/connettori-BT2.0.png
