alessandro-satanassi/OpenFIRE-PICON-ESP32/web/images/dadi_esagonali_m8.png

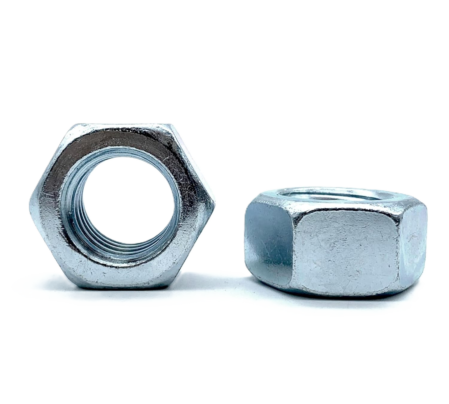
web/images/dadi_esagonali_m8.png
