alessandro-satanassi/OpenFIRE-PICON-ESP32/web/images/dongle.jpg

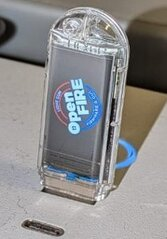
web/images/dongle.jpg
