alessandro-satanassi/OpenFIRE-PICON-ESP32/web/images/dongle_PICO_bb.png

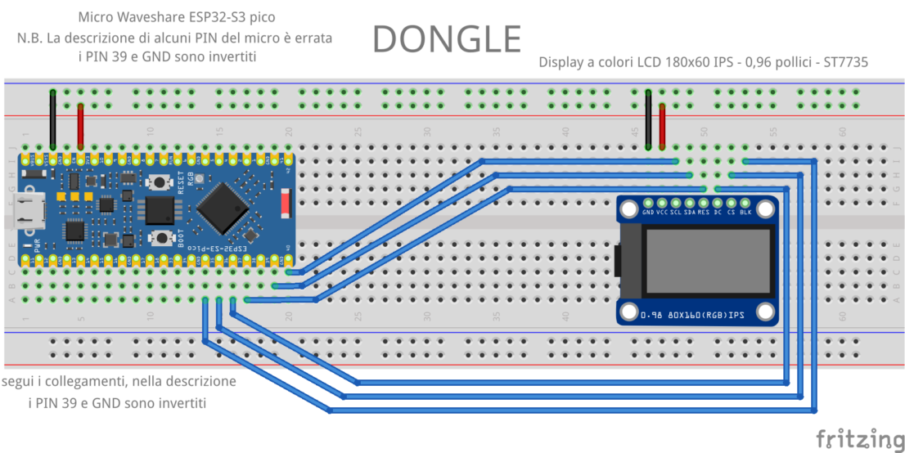
web/images/dongle_PICO_bb.png
