alessandro-satanassi/OpenFIRE-PICON-ESP32/web/images/driver-MOS-scheda-20A-Mini-5-26V-PWM.png

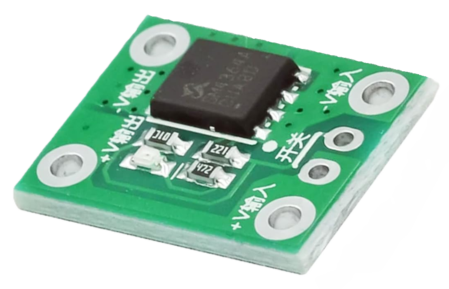
web/images/driver-MOS-scheda-20A-Mini-5-26V-PWM.png
