alessandro-satanassi/OpenFIRE-PICON-ESP32/web/images/dual_pedal_retro_2.png

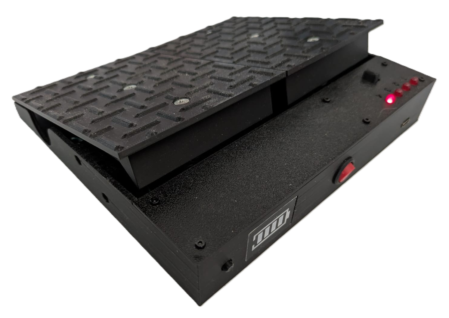
web/images/dual_pedal_retro_2.png
