alessandro-satanassi/OpenFIRE-PICON-ESP32/web/images/dual_predal_sopra.png

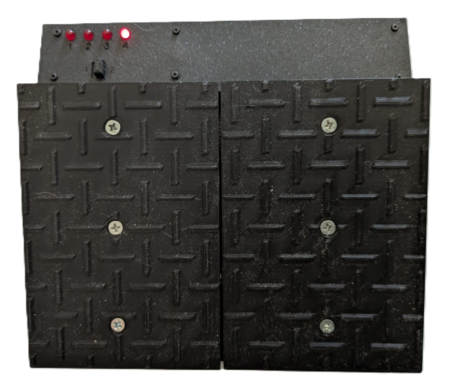
web/images/dual_predal_sopra.png
