alessandro-satanassi/OpenFIRE-PICON-ESP32/web/images/esp32-s3-wroom.png

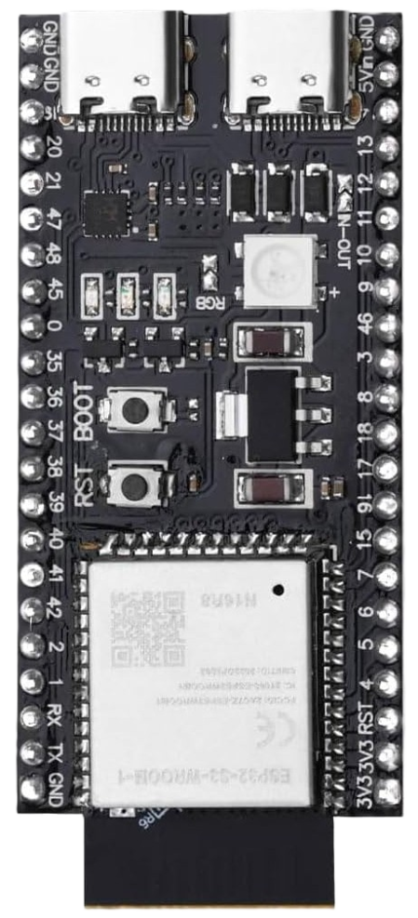
web/images/esp32-s3-wroom.png
