alessandro-satanassi/OpenFIRE-PICON-ESP32/web/images/esp32-s3-zero-3_2.png

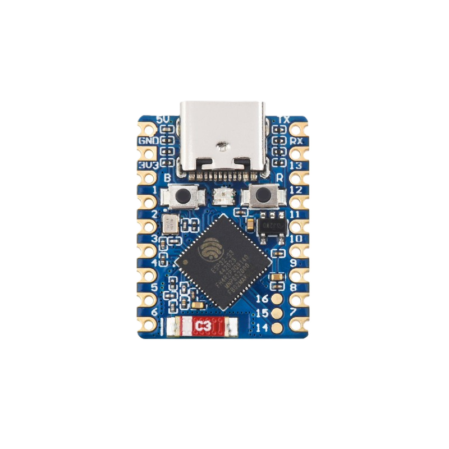
web/images/esp32-s3-zero-3_2.png
