alessandro-satanassi/OpenFIRE-PICON-ESP32/web/images/Esp32s3-pico.jpg

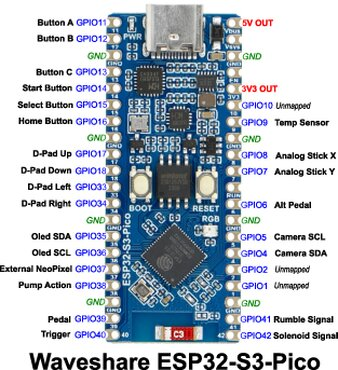
web/images/Esp32s3-pico.jpg
