alessandro-satanassi/OpenFIRE-PICON-ESP32/web/images/esp32s3-wroom1-devkitc.jpg

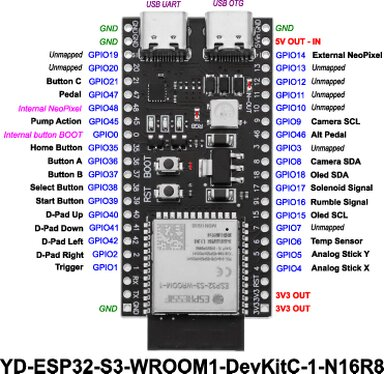
web/images/esp32s3-wroom1-devkitc.jpg
