alessandro-satanassi/OpenFIRE-PICON-ESP32/web/images/esploso_dx_INSERTI.png

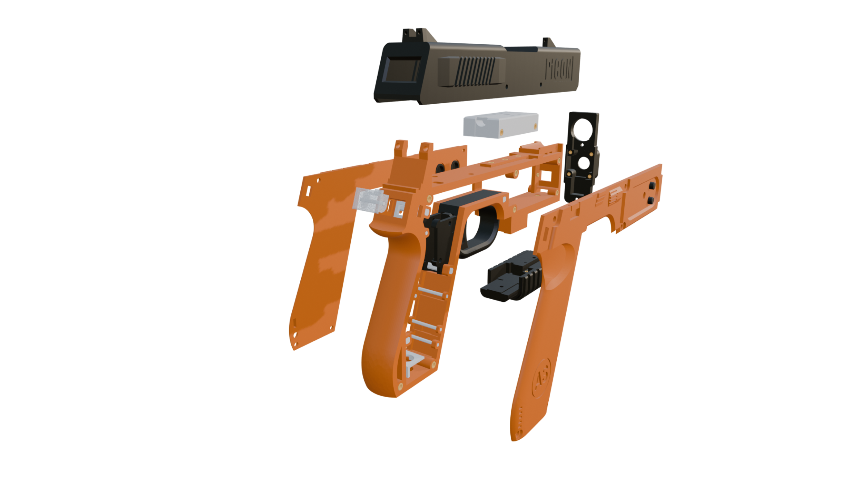
web/images/esploso_dx_INSERTI.png
