alessandro-satanassi/OpenFIRE-PICON-ESP32/web/images/esploso_stl_fronte_dx.png

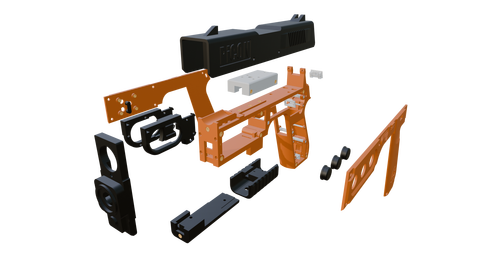
web/images/esploso_stl_fronte_dx.png
