alessandro-satanassi/OpenFIRE-PICON-ESP32/web/images/esploso_stl_fronte_sx.png

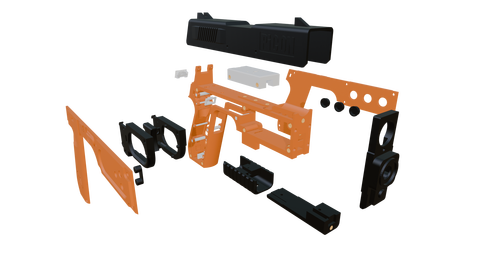
web/images/esploso_stl_fronte_sx.png
