alessandro-satanassi/OpenFIRE-PICON-ESP32/web/images/esploso_stl_retro_dx.png

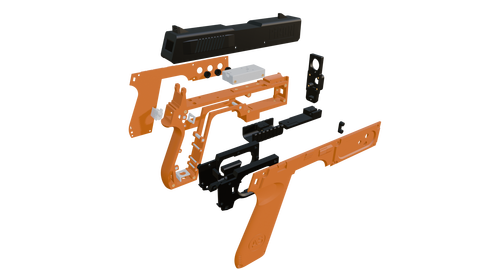
web/images/esploso_stl_retro_dx.png
