alessandro-satanassi/OpenFIRE-PICON-ESP32/web/images/esploso_sx_INSERTI.png

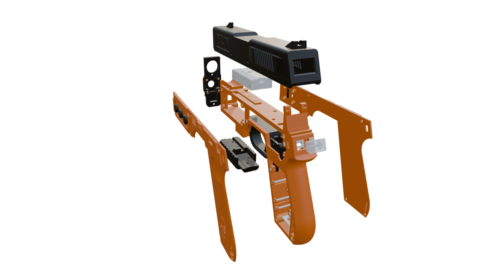
web/images/esploso_sx_INSERTI.png
