alessandro-satanassi/OpenFIRE-PICON-ESP32/web/images/fascette_di_plastica.png

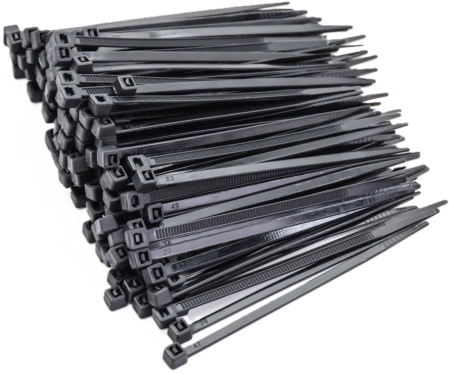
web/images/fascette_di_plastica.png
