alessandro-satanassi/OpenFIRE-PICON-ESP32/web/images/filo_elettrico_22AWG.png

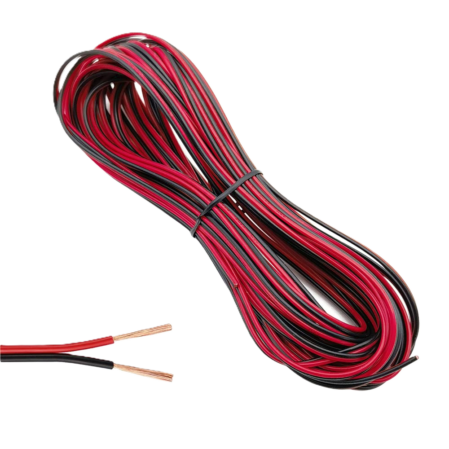
web/images/filo_elettrico_22AWG.png
