alessandro-satanassi/OpenFIRE-PICON-ESP32/web/images/front-1_0v8v39ak.png

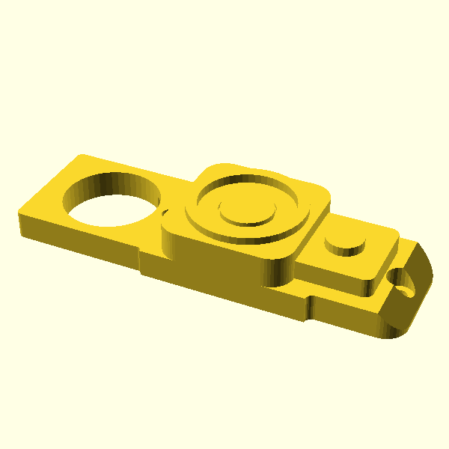
web/images/front-1_0v8v39ak.png
