alessandro-satanassi/OpenFIRE-PICON-ESP32/web/images/frontale_analogico-Cut.png

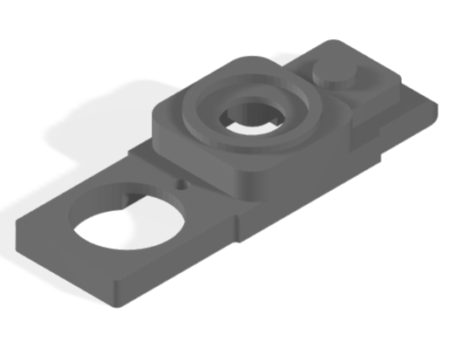
web/images/frontale_analogico-Cut.png
