alessandro-satanassi/OpenFIRE-PICON-ESP32/web/images/GNPE-Pocket-Dongle-S3-N16R8.png

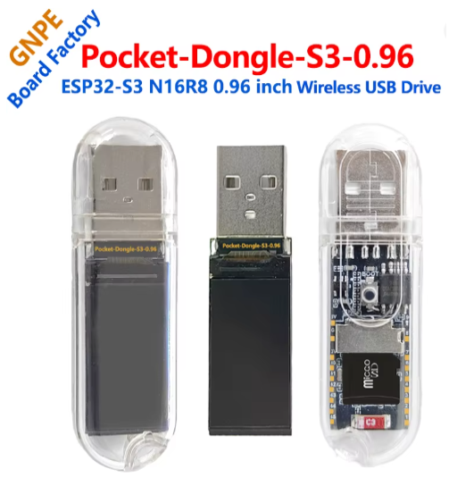
web/images/GNPE-Pocket-Dongle-S3-N16R8.png
