alessandro-satanassi/OpenFIRE-PICON-ESP32/web/images/guaine_termorestringenti.png

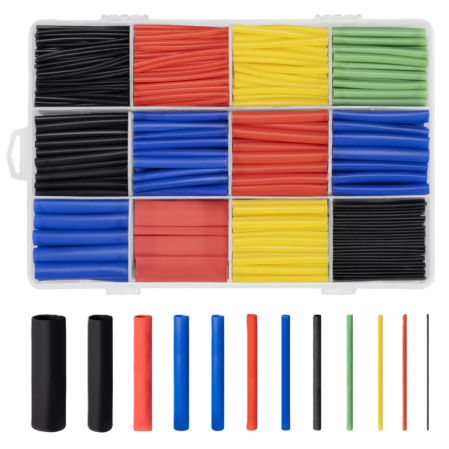
web/images/guaine_termorestringenti.png
