alessandro-satanassi/OpenFIRE-PICON-ESP32/web/images/inserti.png

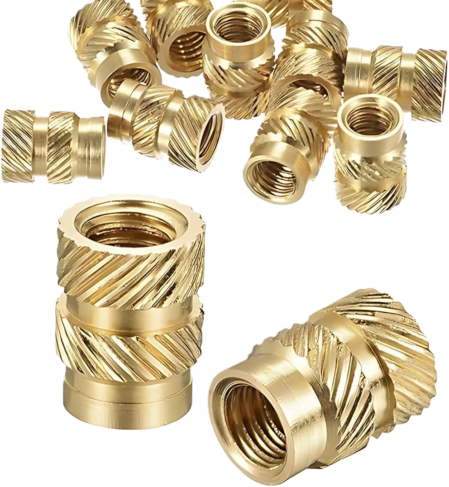
web/images/inserti.png
