alessandro-satanassi/OpenFIRE-PICON-ESP32/web/images/inserti_filettati.png

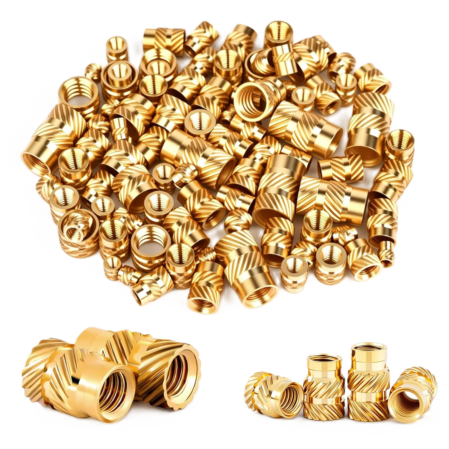
web/images/inserti_filettati.png
