alessandro-satanassi/OpenFIRE-PICON-ESP32/web/images/interno_pedale.png

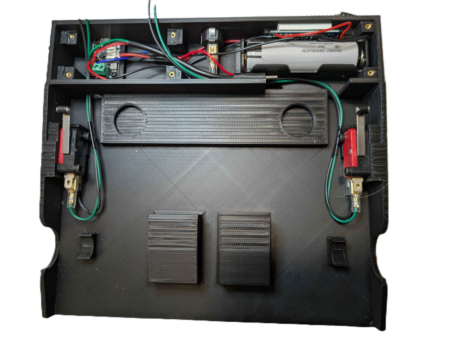
web/images/interno_pedale.png
