alessandro-satanassi/OpenFIRE-PICON-ESP32/web/images/INTERRUTTORE-SWITCH---DX.png

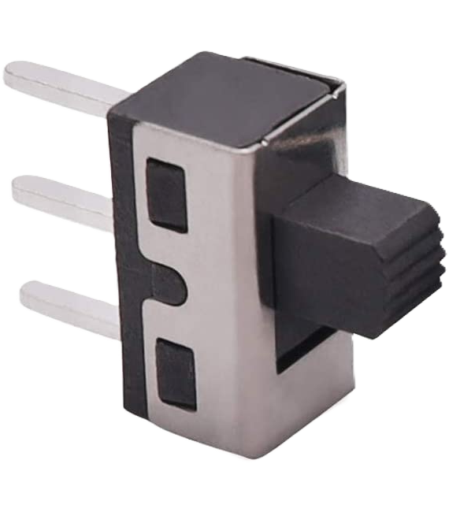
web/images/INTERRUTTORE-SWITCH---DX.png
