alessandro-satanassi/OpenFIRE-PICON-ESP32/web/images/IPS-0,96-pollici-TFT-display-LCD-ST7735-80-x-160-_-2.png

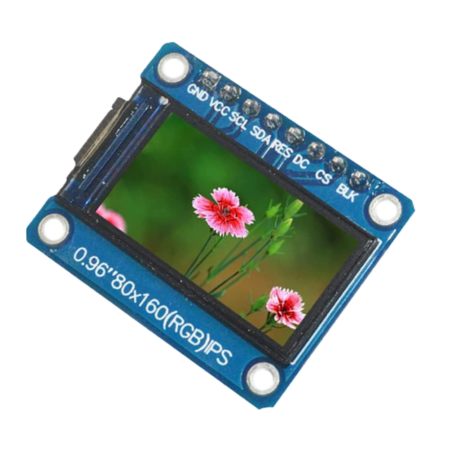
web/images/IPS-0,96-pollici-TFT-display-LCD-ST7735-80-x-160-_-2.png
