alessandro-satanassi/OpenFIRE-PICON-ESP32/web/images/IR_Emitter_app_001.png

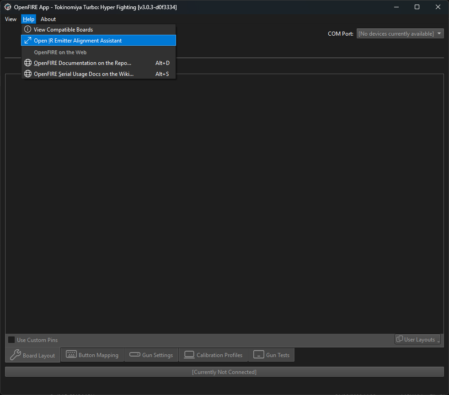
web/images/IR_Emitter_app_001.png
