alessandro-satanassi/OpenFIRE-PICON-ESP32/web/images/IR_Emitter_monitor.jpg

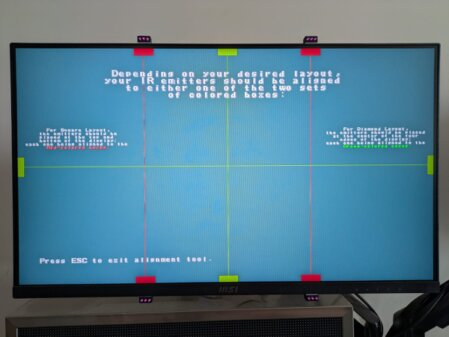
web/images/IR_Emitter_monitor.jpg
