alessandro-satanassi/OpenFIRE-PICON-ESP32/web/images/IR_LED_EMITTER_OSRAM_SFH-4547_SPL_2.png

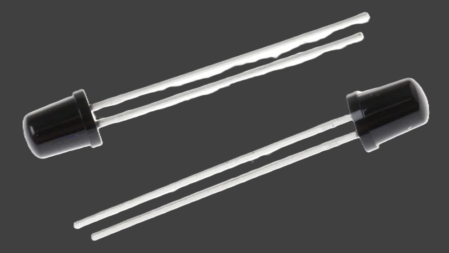
web/images/IR_LED_EMITTER_OSRAM_SFH-4547_SPL_2.png
