alessandro-satanassi/OpenFIRE-PICON-ESP32/web/images/istruzioni_led_stato_batteria.png

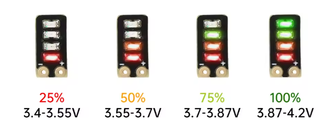
web/images/istruzioni_led_stato_batteria.png
