alessandro-satanassi/OpenFIRE-PICON-ESP32/web/images/JST-PHR-02-polarita-invertita.jpg

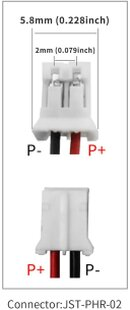
web/images/JST-PHR-02-polarita-invertita.jpg
