alessandro-satanassi/OpenFIRE-PICON-ESP32/web/images/large-6640235.png

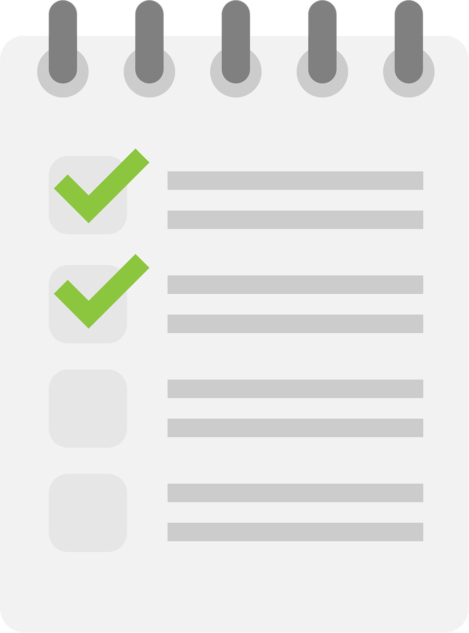
web/images/large-6640235.png
