alessandro-satanassi/OpenFIRE-PICON-ESP32/web/images/large-6980894.png

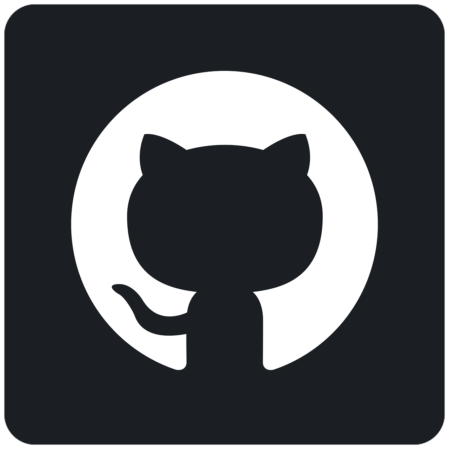
web/images/large-6980894.png
