alessandro-satanassi/OpenFIRE-PICON-ESP32/web/images/led_rosso_5mm.png

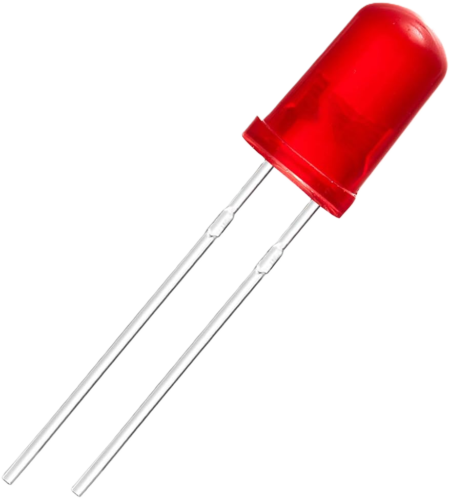
web/images/led_rosso_5mm.png
