alessandro-satanassi/OpenFIRE-PICON-ESP32/web/images/lente_grandangolare.png

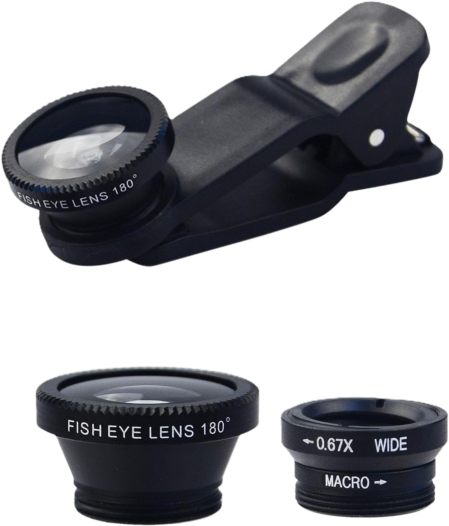
web/images/lente_grandangolare.png
