alessandro-satanassi/OpenFIRE-PICON-ESP32/web/images/Lid.png

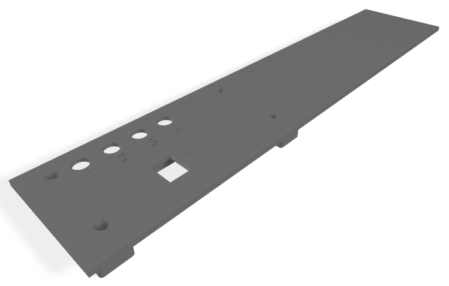
web/images/Lid.png
