alessandro-satanassi/OpenFIRE-PICON-ESP32/web/images/LILYGO-T-Dongle-S3-ESP32-S3-TTGO.png

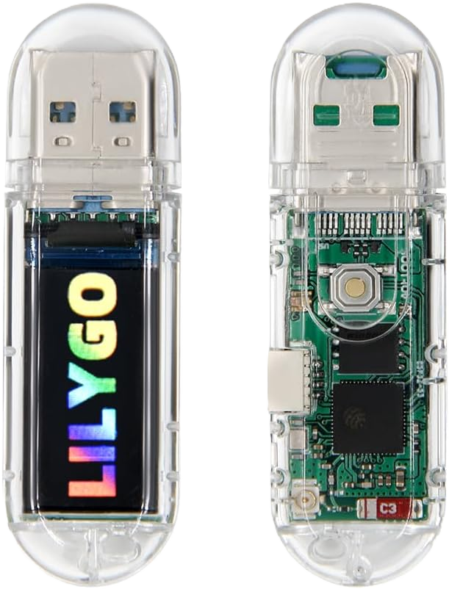
web/images/LILYGO-T-Dongle-S3-ESP32-S3-TTGO.png
