alessandro-satanassi/OpenFIRE-PICON-ESP32/web/images/MICRI-SWITCH--V-15-1C25.png

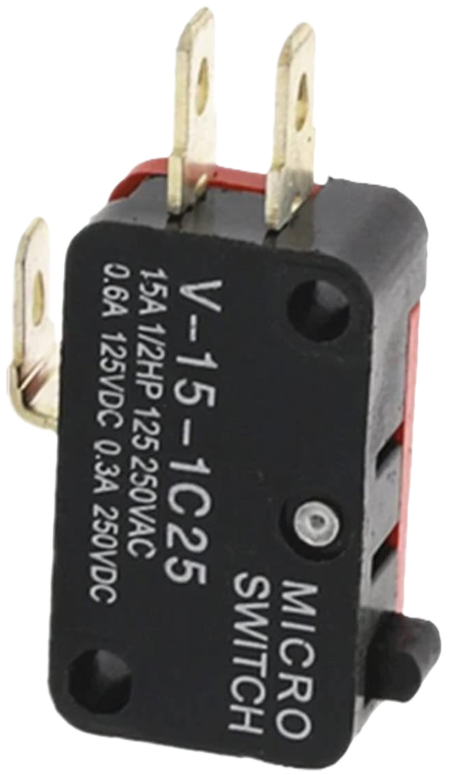
web/images/MICRI-SWITCH--V-15-1C25.png
