alessandro-satanassi/OpenFIRE-PICON-ESP32/web/images/MICRO-INTERRUTTORE-a.png

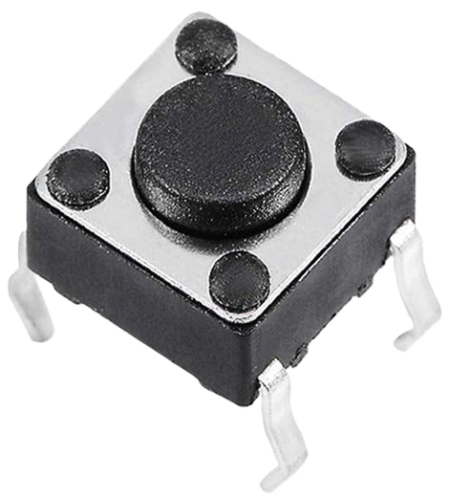
web/images/MICRO-INTERRUTTORE-a.png
