alessandro-satanassi/OpenFIRE-PICON-ESP32/web/images/micro_interruttore_6x6x4.3.jpg

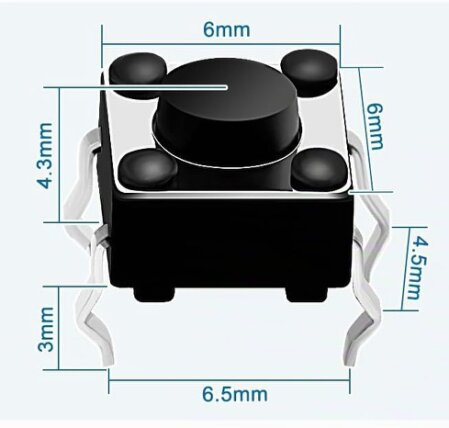
web/images/micro_interruttore_6x6x4.3.jpg
