alessandro-satanassi/OpenFIRE-PICON-ESP32/web/images/mini_interruttore_rotondo_d16mm.png

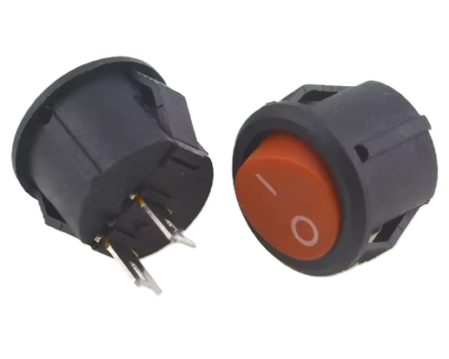
web/images/mini_interruttore_rotondo_d16mm.png
