alessandro-satanassi/OpenFIRE-PICON-ESP32/web/images/mini_interruttore_scorrimento_3pin_2posizioni.jpg

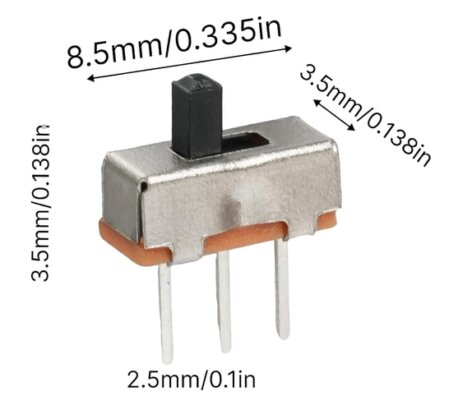
web/images/mini_interruttore_scorrimento_3pin_2posizioni.jpg
