alessandro-satanassi/OpenFIRE-PICON-ESP32/web/images/miucro_switch__v-156-1c25.jpg

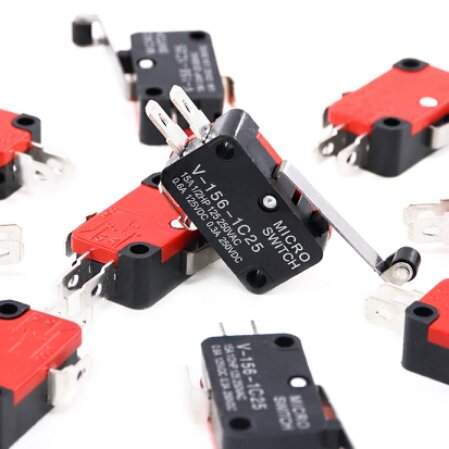
web/images/miucro_switch__v-156-1c25.jpg
