alessandro-satanassi/OpenFIRE-PICON-ESP32/web/images/modulo_LED_indicatore_carica_batteria_litio_1s.jpg

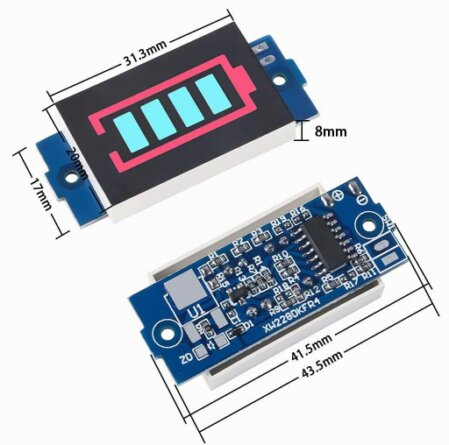
web/images/modulo_LED_indicatore_carica_batteria_litio_1s.jpg
