alessandro-satanassi/OpenFIRE-PICON-ESP32/web/images/molla_assiale.png

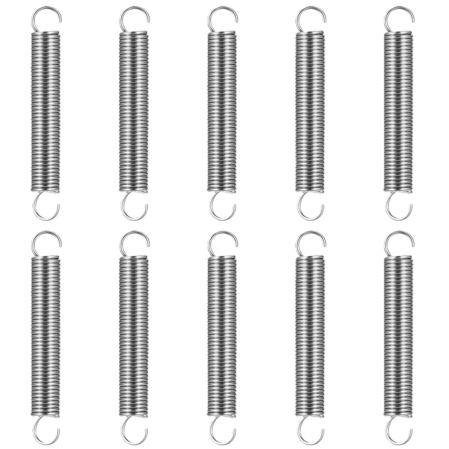
web/images/molla_assiale.png
