alessandro-satanassi/OpenFIRE-PICON-ESP32/web/images/molla_compressione_18x1x25.jpg

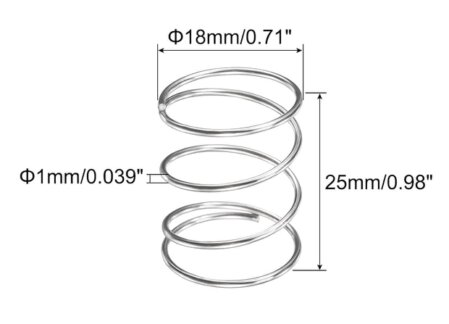
web/images/molla_compressione_18x1x25.jpg
