alessandro-satanassi/OpenFIRE-PICON-ESP32/web/images/molle_a_compressione_4.png

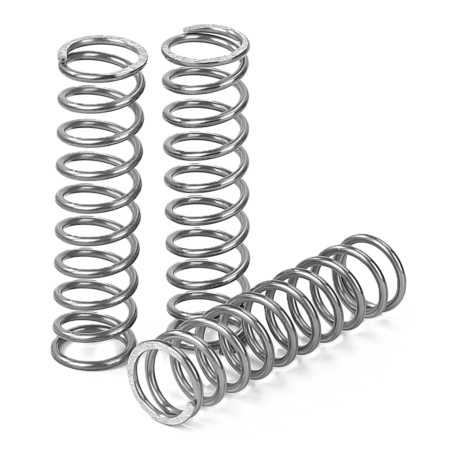
web/images/molle_a_compressione_4.png
