alessandro-satanassi/OpenFIRE-PICON-ESP32/web/images/mosfet-n-channel-2n7000-to-92.png

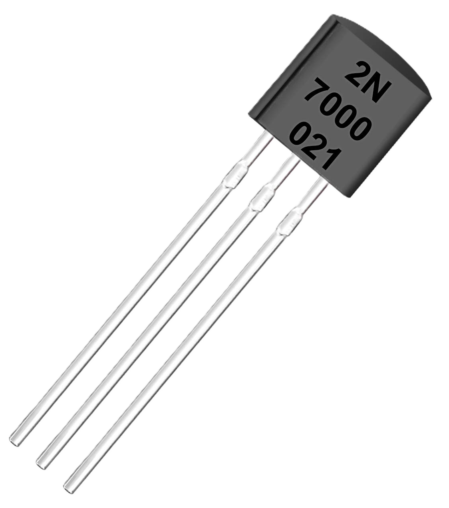
web/images/mosfet-n-channel-2n7000-to-92.png
