alessandro-satanassi/OpenFIRE-PICON-ESP32/web/images/MP3429-Booster-Module-21A-Power-Supply--12V-.png

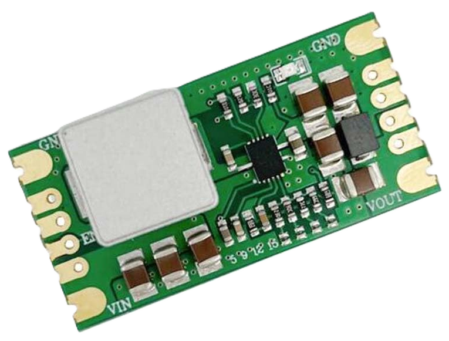
web/images/MP3429-Booster-Module-21A-Power-Supply--12V-.png
