alessandro-satanassi/OpenFIRE-PICON-ESP32/web/images/neopixel-WS2812B-fronte.png

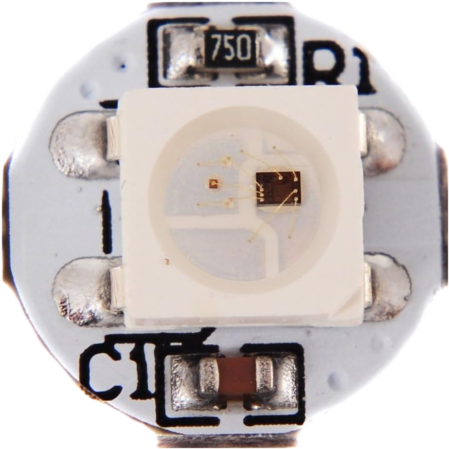
web/images/neopixel-WS2812B-fronte.png
