alessandro-satanassi/OpenFIRE-PICON-ESP32/web/images/nr_2_viti_blocco_OLED.png

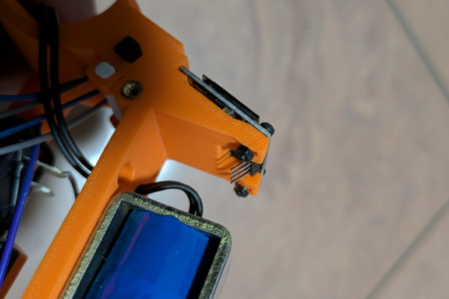
web/images/nr_2_viti_blocco_OLED.png
