alessandro-satanassi/OpenFIRE-PICON-ESP32/web/images/nr_2_viti_supporto_solenoide.png

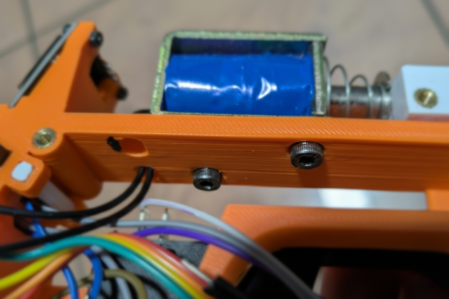
web/images/nr_2_viti_supporto_solenoide.png
