alessandro-satanassi/OpenFIRE-PICON-ESP32/web/images/OFA_header.png

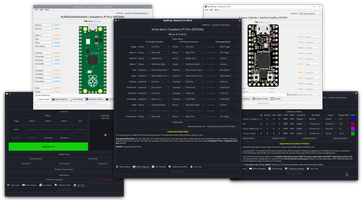
web/images/OFA_header.png
