alessandro-satanassi/OpenFIRE-PICON-ESP32/web/images/OFA_screens.png

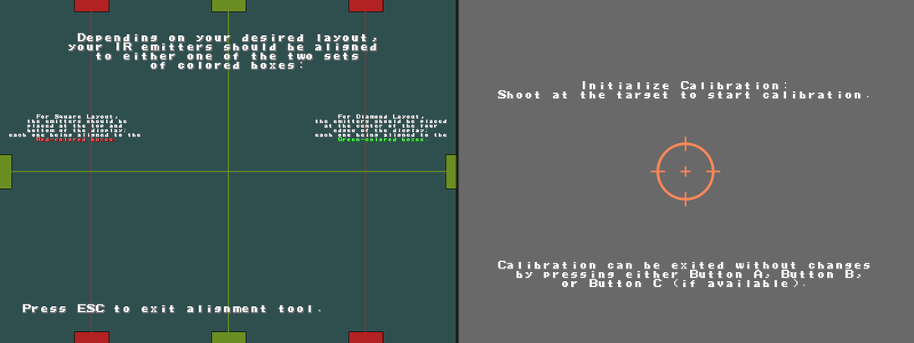
web/images/OFA_screens.png
