alessandro-satanassi/OpenFIRE-PICON-ESP32/web/images/oled-128x64.png

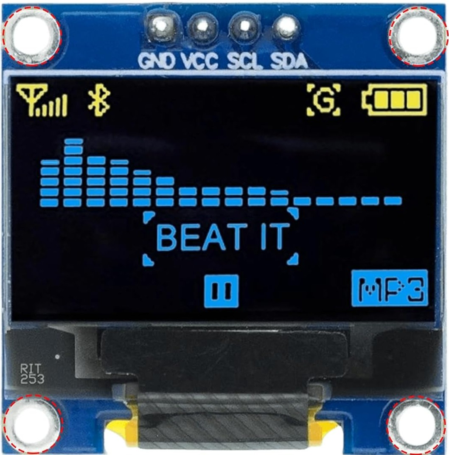
web/images/oled-128x64.png
