alessandro-satanassi/OpenFIRE-PICON-ESP32/web/images/pad-game-5d.png

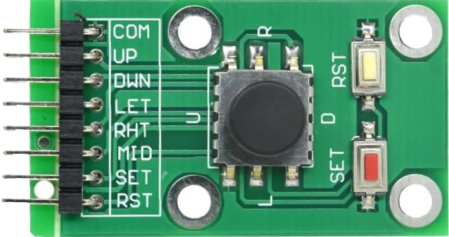
web/images/pad-game-5d.png
