alessandro-satanassi/OpenFIRE-PICON-ESP32/web/files/path_control---definitivo---REV.2---BOARD-PCB.png

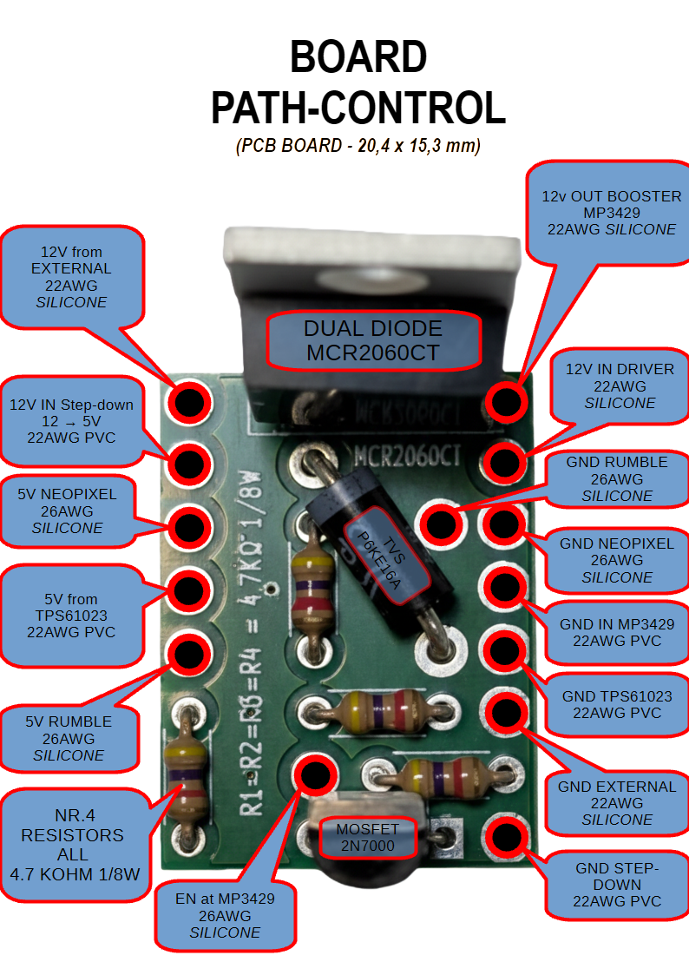
web/images/path_control---definitivo---REV.2---BOARD-PCB.png
