alessandro-satanassi/OpenFIRE-PICON-ESP32/web/files/path_control---definitivo---REV.2.png

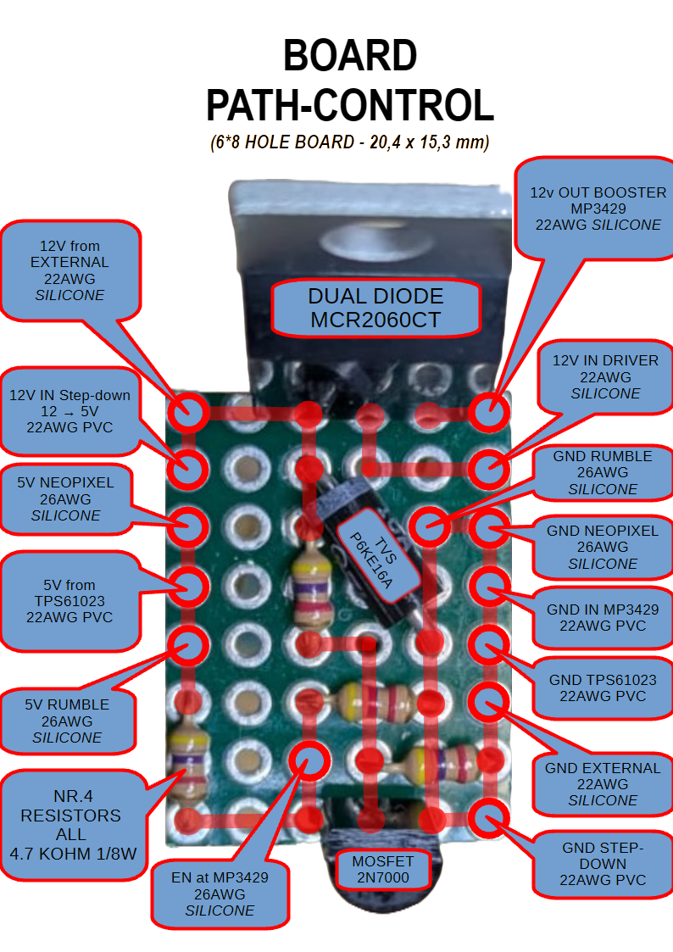
web/images/path_control---definitivo---REV_kzherapo.2.png
