alessandro-satanassi/OpenFIRE-PICON-ESP32/web/images/Pedal-Frame-for-nut.png

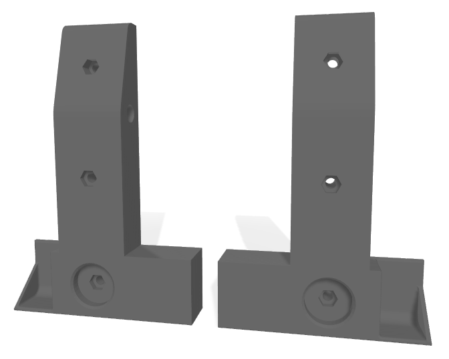
web/images/Pedal-Frame-for-nut.png
