alessandro-satanassi/OpenFIRE-PICON-ESP32/web/images/Pedal-Frame.png

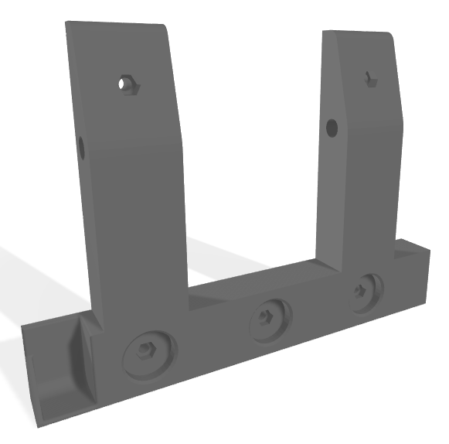
web/images/Pedal-Frame.png
