alessandro-satanassi/OpenFIRE-PICON-ESP32/web/images/Pedal-Select.png

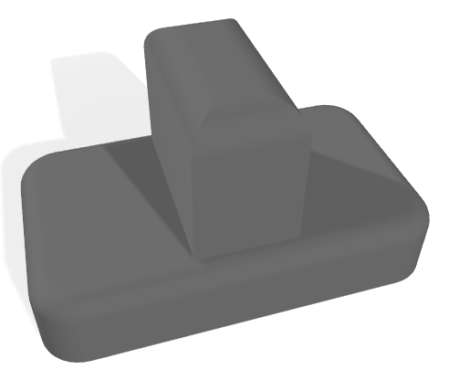
web/images/Pedal-Select.png
