alessandro-satanassi/OpenFIRE-PICON-ESP32/web/images/pedal_bb.png

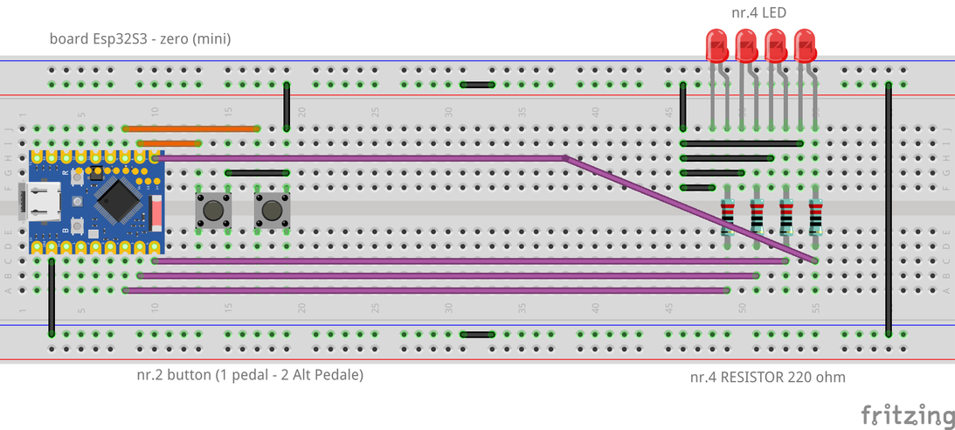
web/images/pedal_bb.png
