alessandro-satanassi/OpenFIRE-PICON-ESP32/web/images/pedal_bb_2gml8y81.png

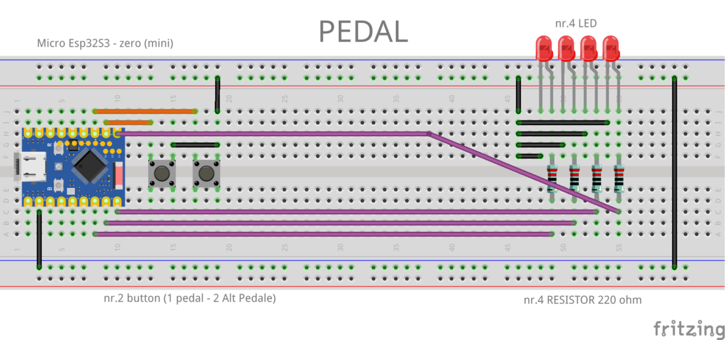
web/images/pedal_bb_2gml8y81.png
