alessandro-satanassi/OpenFIRE-PICON-ESP32/web/images/pedale---intero.png

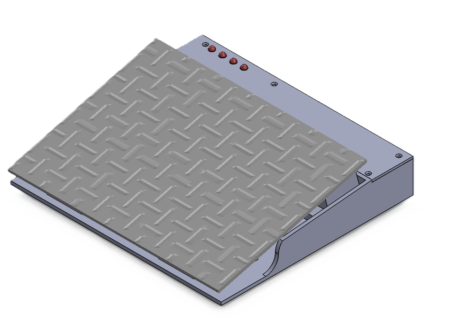
web/images/pedale---intero.png
