alessandro-satanassi/OpenFIRE-PICON-ESP32/web/images/pedale_pcb_millefori_bb.png

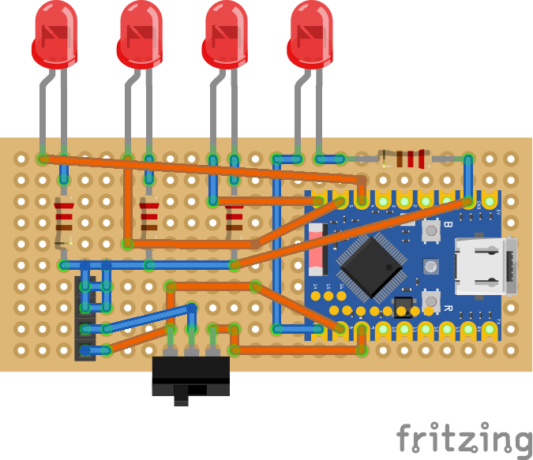
web/images/pedale_pcb_millefori_bb.png
