alessandro-satanassi/OpenFIRE-PICON-ESP32/web/images/pedale_pcb_millefori_schem.png

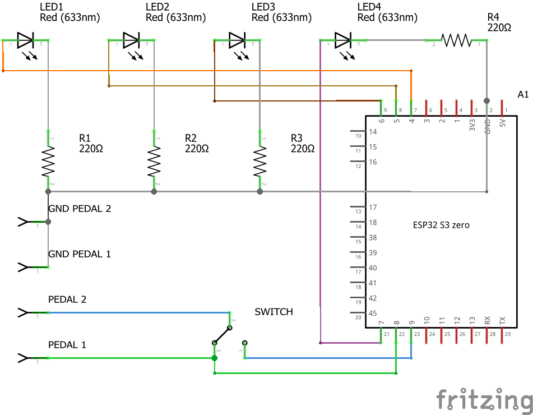
web/images/pedale_pcb_millefori_schem.png
