alessandro-satanassi/OpenFIRE-PICON-ESP32/web/images/Pin.png

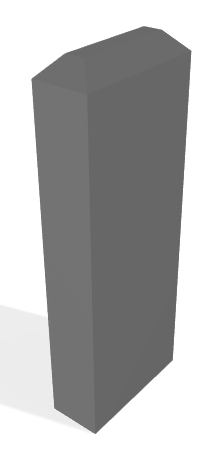
web/images/Pin.png
