alessandro-satanassi/OpenFIRE-PICON-ESP32/web/images/pin_header_maschio_e_femmin_2.54.png

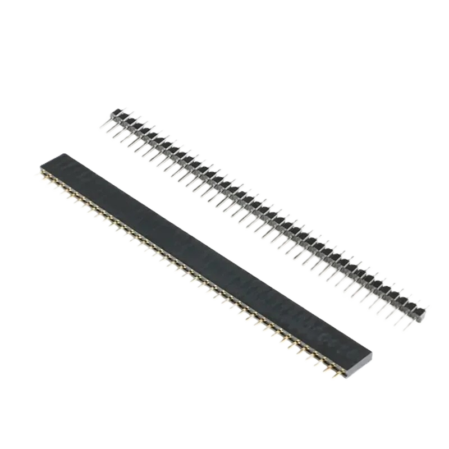
web/images/pin_header_maschio_e_femmin_2.54.png
