alessandro-satanassi/OpenFIRE-PICON-ESP32/web/images/pixabay-42770.png

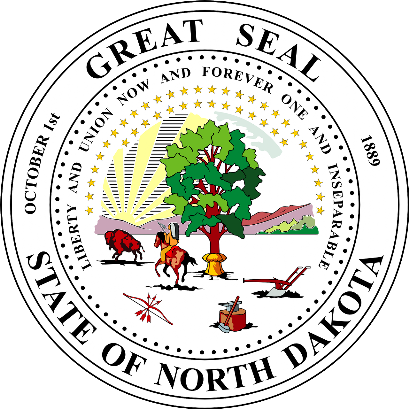
web/images/pixabay-42770.png
