alessandro-satanassi/OpenFIRE-PICON-ESP32/web/images/pixabay-144997.png

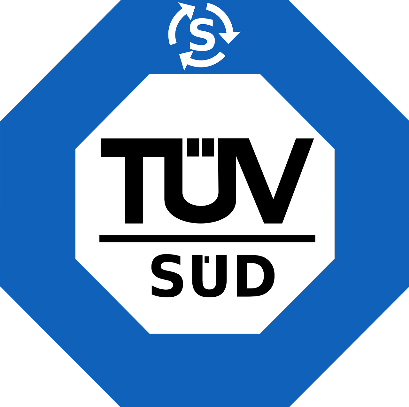
web/images/pixabay-144997.png
