alessandro-satanassi/OpenFIRE-PICON-ESP32/web/images/pixabay-154114.png

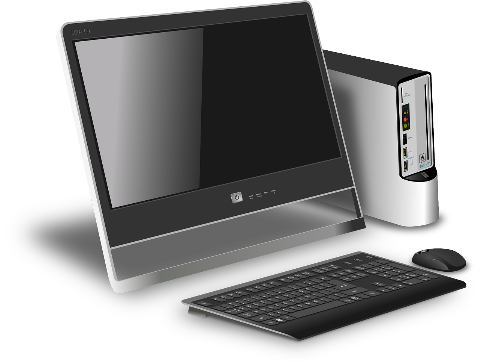
web/images/pixabay-154114.png
