alessandro-satanassi/OpenFIRE-PICON-ESP32/web/images/pixabay-154533.png

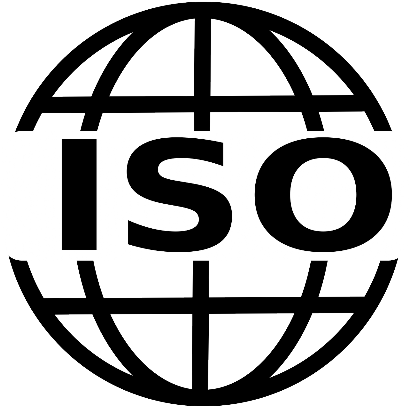
web/images/pixabay-154533.png
