alessandro-satanassi/OpenFIRE-PICON-ESP32/web/images/pixabay-158648.png

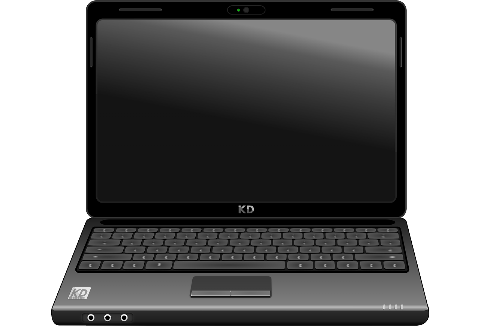
web/images/pixabay-158648.png
