alessandro-satanassi/OpenFIRE-PICON-ESP32/web/images/pixabay-158743.png

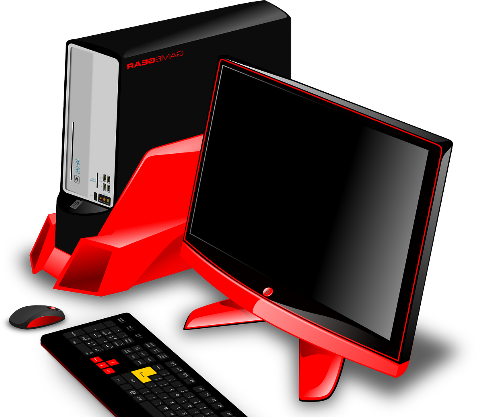
web/images/pixabay-158743.png
