alessandro-satanassi/OpenFIRE-PICON-ESP32/web/images/pixabay-189064.png

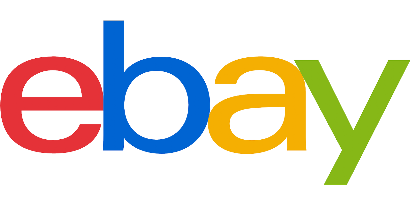
web/images/pixabay-189064.png
