alessandro-satanassi/OpenFIRE-PICON-ESP32/web/images/pixabay-784404.png

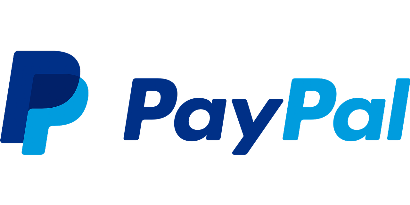
web/images/pixabay-784404.png
