alessandro-satanassi/OpenFIRE-PICON-ESP32/web/images/pixabay-1015751.png

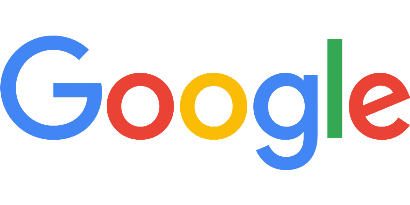
web/images/pixabay-1015751.png
