alessandro-satanassi/OpenFIRE-PICON-ESP32/web/images/pixabay-1454731.png

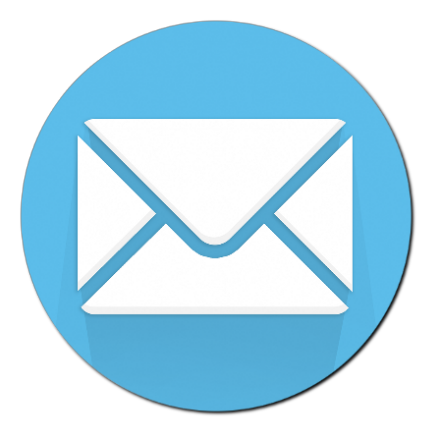
web/images/pixabay-1454731.png
