alessandro-satanassi/OpenFIRE-PICON-ESP32/web/images/Plate-Left.png

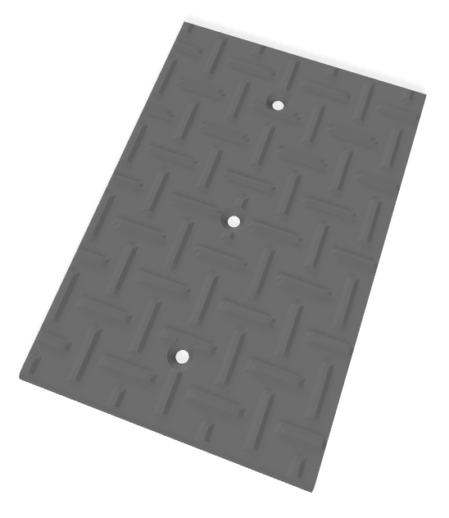
web/images/Plate-Left.png
