alessandro-satanassi/OpenFIRE-PICON-ESP32/web/images/Plate-Right.png

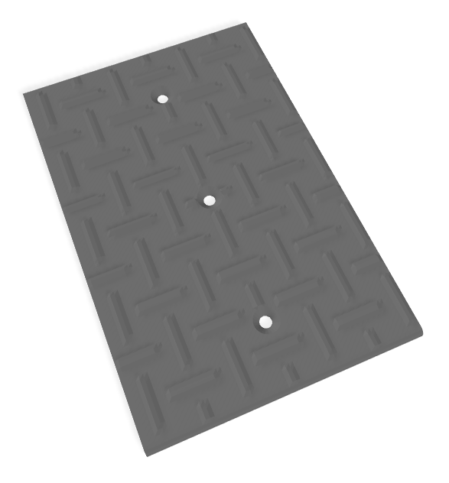
web/images/Plate-Right.png
