alessandro-satanassi/OpenFIRE-PICON-ESP32/web/images/Plate.png

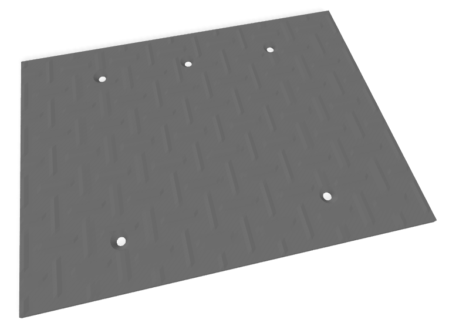
web/images/Plate.png
