alessandro-satanassi/OpenFIRE-PICON-ESP32/web/images/pulsante-tattile-6x6x9.png

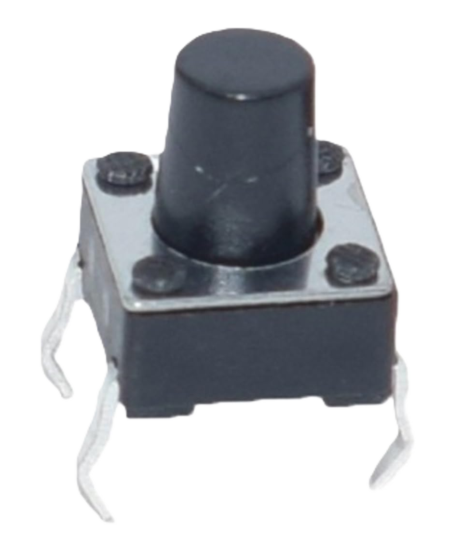
web/images/pulsante-tattile-6x6x9.png
