alessandro-satanassi/OpenFIRE-PICON-ESP32/web/images/pump-mount-1_ah8ly0vv.png

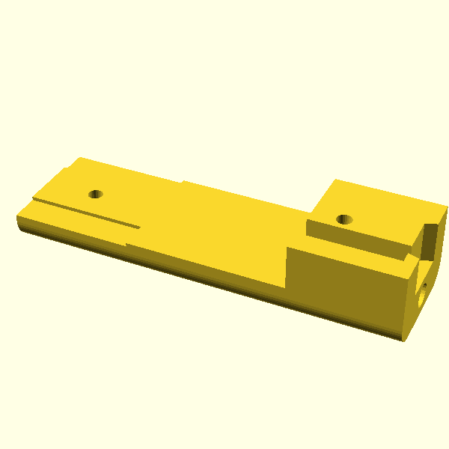
web/images/pump-mount-1_ah8ly0vv.png
