alessandro-satanassi/OpenFIRE-PICON-ESP32/web/images/pump_smwwq5tt.png

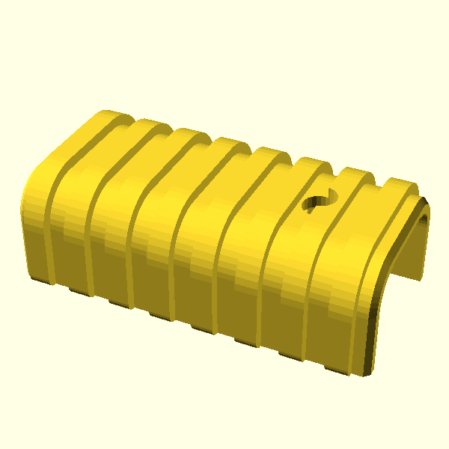
web/images/pump_smwwq5tt.png
