alessandro-satanassi/OpenFIRE-PICON-ESP32/web/images/pxl_20240619_200546409-300x225.png

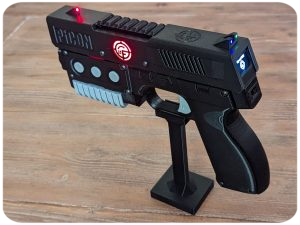
web/images/pxl_20240619_200546409-300x225.png
