alessandro-satanassi/OpenFIRE-PICON-ESP32/web/images/rail_mini_guida_lineare_larghezza_9mm_lunghezza_55mm.png

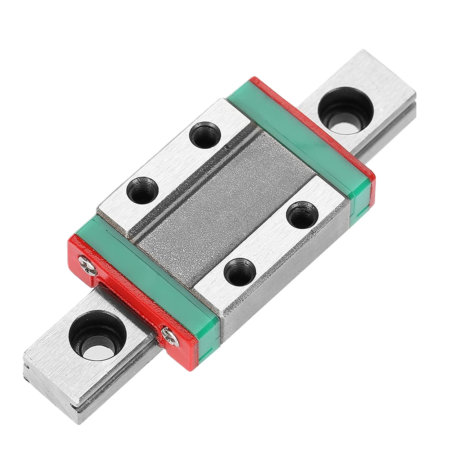
web/images/rail_mini_guida_lineare_larghezza_9mm_lunghezza_55mm.png
