alessandro-satanassi/OpenFIRE-PICON-ESP32/web/images/resiostenze_220ohm_0.25w.jpg

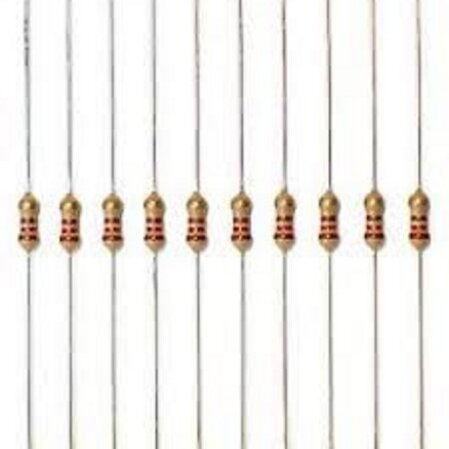
web/images/resiostenze_220ohm_0.25w.jpg
