alessandro-satanassi/OpenFIRE-PICON-ESP32/web/images/resistenze-4,7Kohm-1-8-W.png

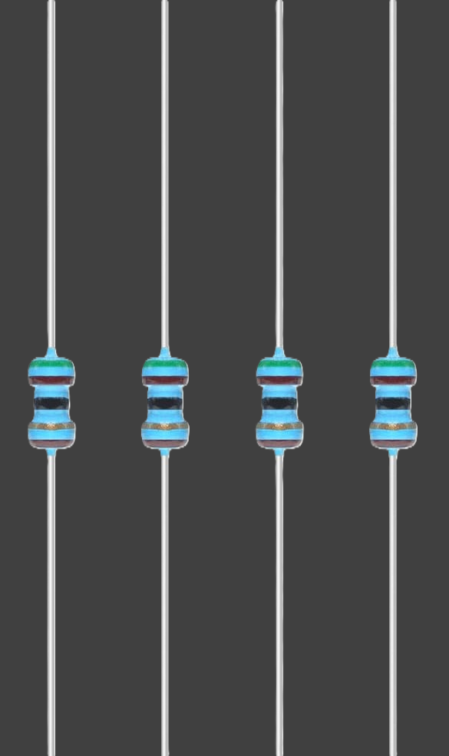
web/images/resistenze-4,7Kohm-1-8-W.png
