alessandro-satanassi/OpenFIRE-PICON-ESP32/web/images/rondelle_m8.png

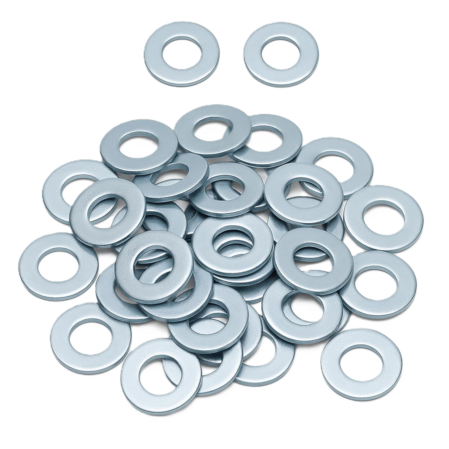
web/images/rondelle_m8.png
