alessandro-satanassi/OpenFIRE-PICON-ESP32/web/images/rumble.png

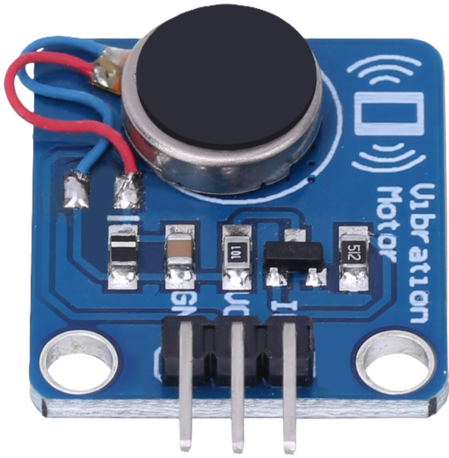
web/images/rumble.png
