alessandro-satanassi/OpenFIRE-PICON-ESP32/web/images/schema_collegamento.png

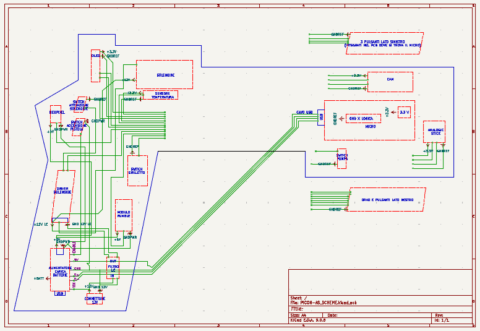
web/images/schema_collegamento.png
