alessandro-satanassi/OpenFIRE-PICON-ESP32/web/images/solenoide-JF-1039B-alternativo.png

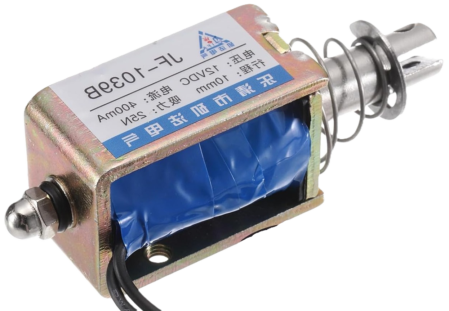
web/images/solenoide-JF-1039B-alternativo.png
