alessandro-satanassi/OpenFIRE-PICON-ESP32/web/images/SPINOTTO-12V.png

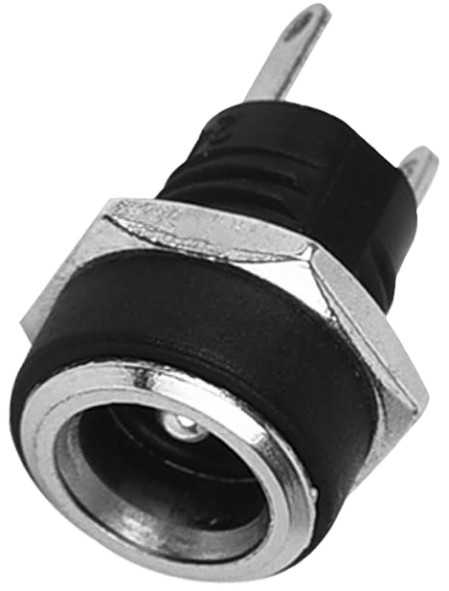
web/images/SPINOTTO-12V.png
