alessandro-satanassi/OpenFIRE-PICON-ESP32/web/images/supporto_batteria_18650.jpg

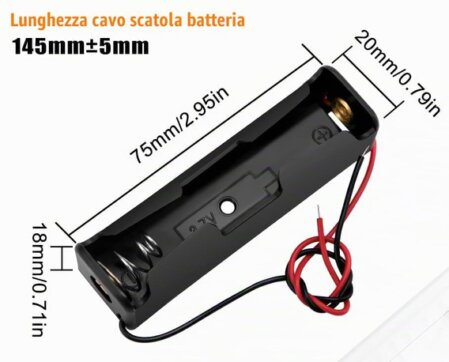
web/images/supporto_batteria_18650.jpg
