alessandro-satanassi/OpenFIRE-PICON-ESP32/web/images/TMP36.png

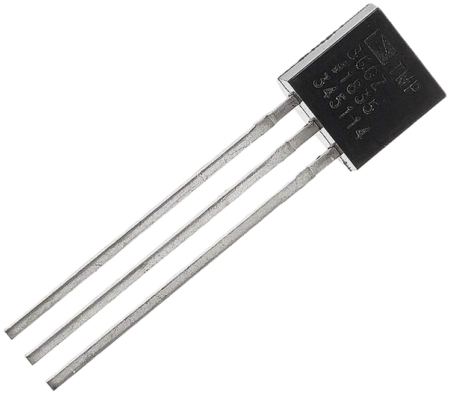
web/images/TMP36.png
