alessandro-satanassi/OpenFIRE-PICON-ESP32/web/images/trasformatore_12v_3a.png

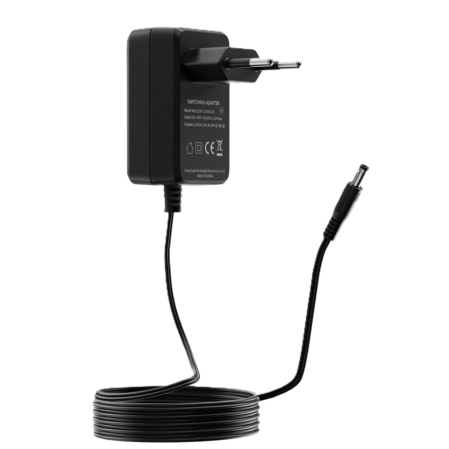
web/images/trasformatore_12v_3a.png
