alessandro-satanassi/OpenFIRE-PICON-ESP32/web/images/trasmettirore_IR.png

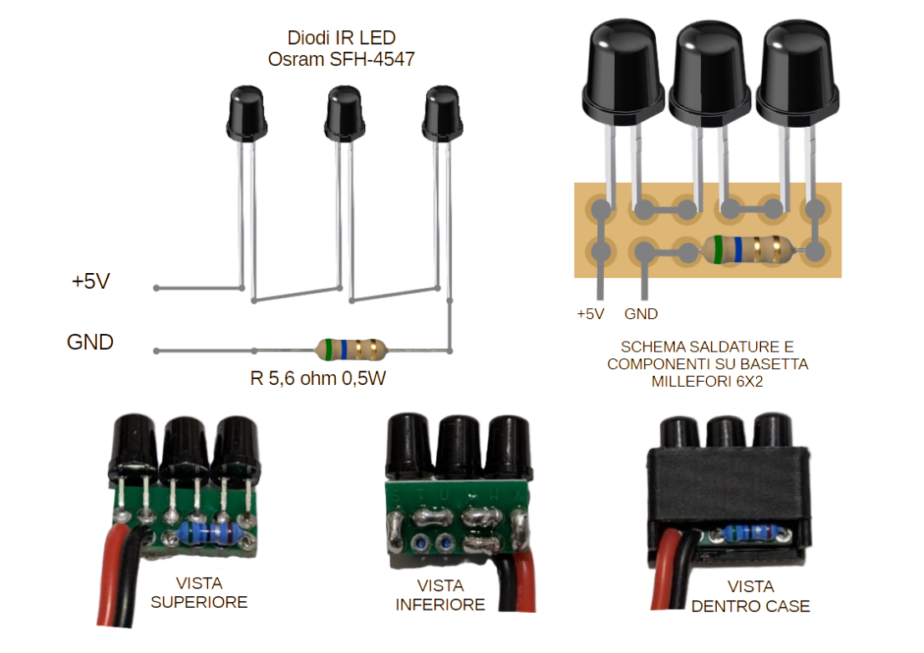
web/images/trasmettirore_IR.png
