alessandro-satanassi/OpenFIRE-PICON-ESP32/web/images/trigger-1_thbgi8sd.png

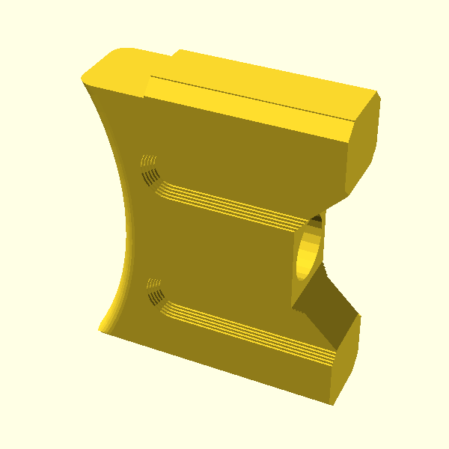
web/images/trigger-1_thbgi8sd.png
