alessandro-satanassi/OpenFIRE-PICON-ESP32/web/images/trigger-guard-left_io75i0g3.png

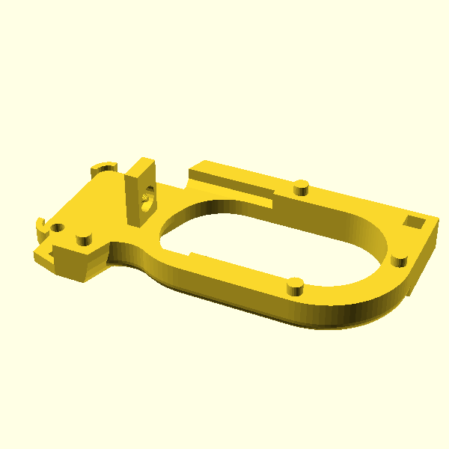
web/images/trigger-guard-left_io75i0g3.png
