alessandro-satanassi/OpenFIRE-PICON-ESP32/web/images/trigger-guard-right_4pb26xgz.png

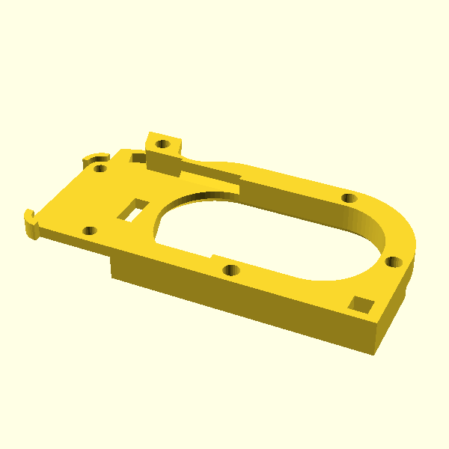
web/images/trigger-guard-right_4pb26xgz.png
