alessandro-satanassi/OpenFIRE-PICON-ESP32/web/images/viti_per_inserti.png

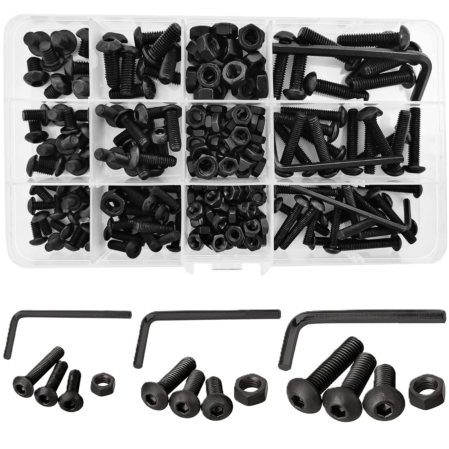
web/images/viti_per_inserti.png
