alessandro-satanassi/OpenFIRE-PICON-ESP32/FreeCAD/STL_PICON_AS/PERNI fermo switch - caricabatterie - grilletto/PICON-OF_ver_37-perno fermo switch - caricabatterie - grilletto.stl

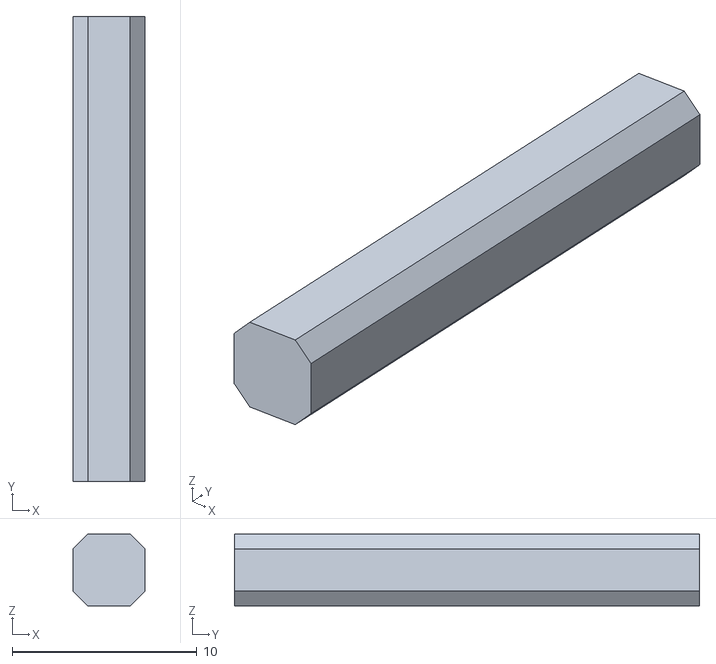
[picture p233: CAD file, 2026-03-09]
FreeCAD/STL_PICON_AS/PERNI fermo switch - caricabatterie - grilletto/PICON-OF_ver_37-perno fermo switch - caricabatterie - grilletto.stl
3.90 x 25.2 x 3.90
