alessandro-satanassi/OpenFIRE-PICON-ESP32/FreeCAD/STL_PICON_AS/PERNI_fermi_rumble_e_driver_solenoide/PICON-OF_ver_37-perno fermo rumble e driver solenoide.stl

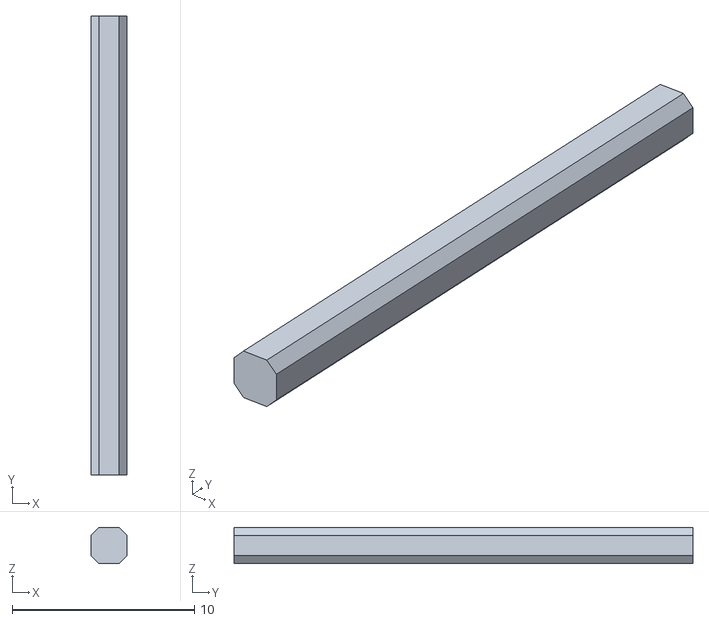
[picture p234: CAD file, 2026-03-09]
FreeCAD/STL_PICON_AS/PERNI_fermi_rumble_e_driver_solenoide/PICON-OF_ver_37-perno fermo rumble e driver solenoide.stl
2.00 x 25.2 x 2.00
