alessandro-satanassi/OpenFIRE-PICON-ESP32/FreeCAD/STL_PICON_AS/PERNO_fermo_NEOPIXEL/PICON-OF_ver_37-perno fermo neopixel.stl

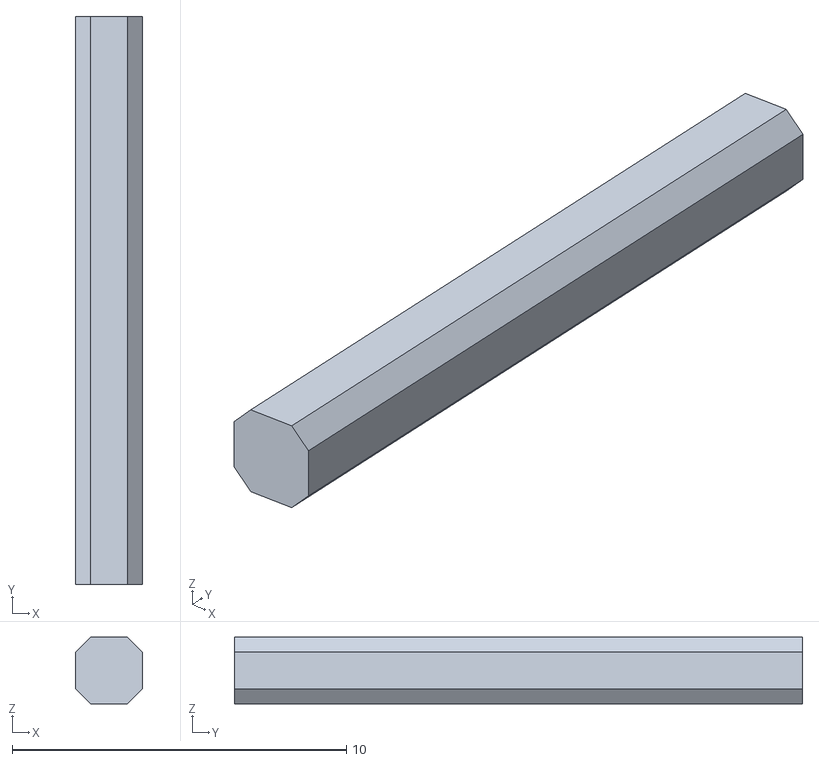
[picture p235: CAD file, 2026-03-09]
FreeCAD/STL_PICON_AS/PERNO_fermo_NEOPIXEL/PICON-OF_ver_37-perno fermo neopixel.stl
2.00 x 17.0 x 2.00
