alessandro-satanassi/OpenFIRE-PICON-ESP32/FreeCAD/STL_PICON_AS/PULSANTE_lato_DX/PICON-OF_ver_37-pulsanti lato destro.stl

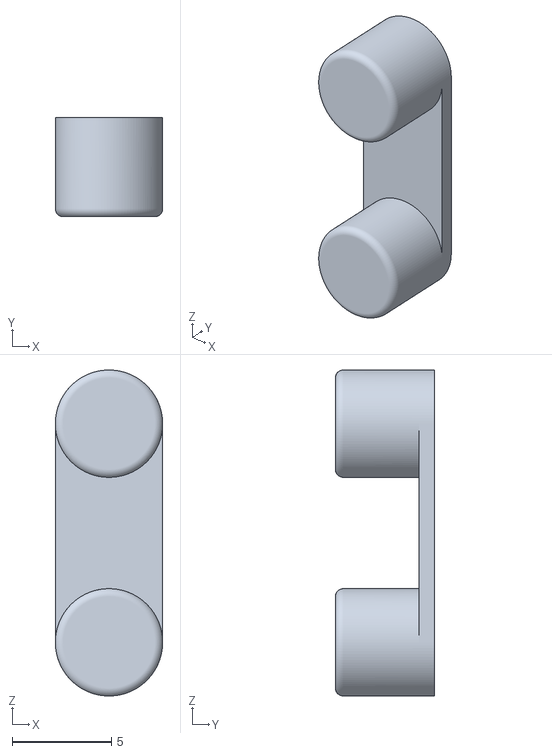
[picture p236: CAD file, 2026-03-09]
FreeCAD/STL_PICON_AS/PULSANTE_lato_DX/PICON-OF_ver_37-pulsanti lato destro.stl
5.40 x 5.00 x 16.4
