alessandro-satanassi/OpenFIRE-PICON-ESP32/FreeCAD/STL_PICON_AS/PULSANTI_lato_SX/PICON-OF_ver_37-pulsanti lato sinistro.stl

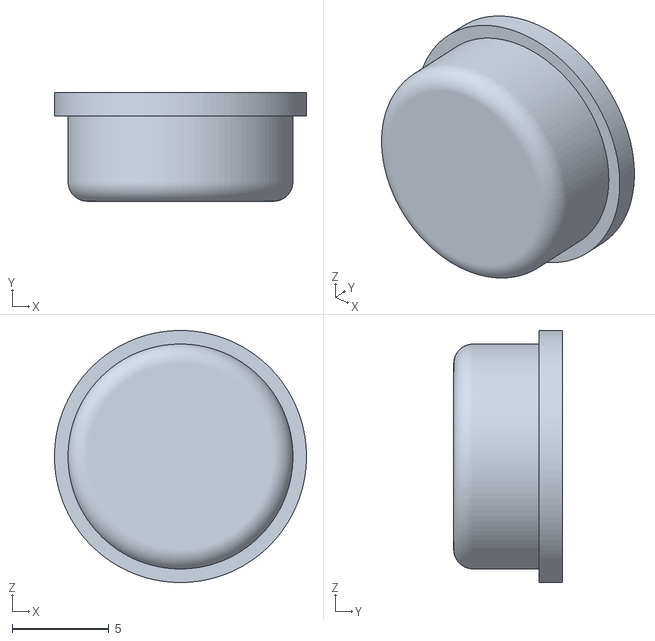
[picture p237: CAD file, 2026-03-09]
FreeCAD/STL_PICON_AS/PULSANTI_lato_SX/PICON-OF_ver_37-pulsanti lato sinistro.stl
13.0 x 5.60 x 13.0
