alessandro-satanassi/OpenFIRE-PICON-ESP32/FreeCAD/STL_PICON_AS/supporto_NEOPIXEL/PICON-OF_ver_37-supporto per neopixel.stl

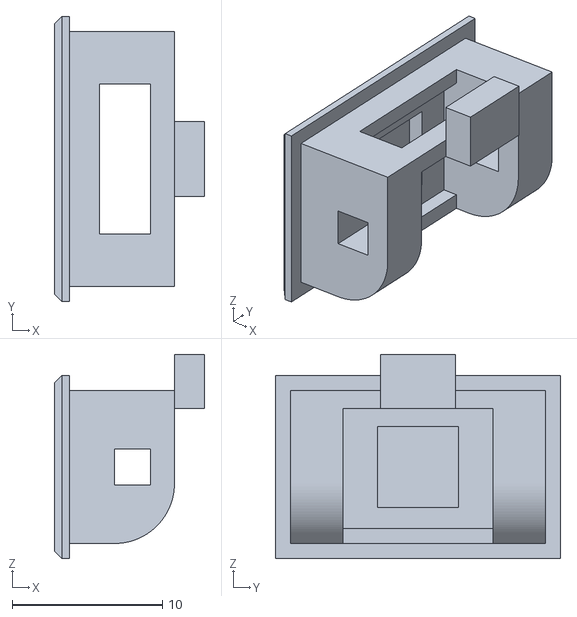
[picture p238: CAD file, 2026-03-09]
FreeCAD/STL_PICON_AS/supporto_NEOPIXEL/PICON-OF_ver_37-supporto per neopixel.stl
10.0 x 19.0 x 13.6
