alessandro-satanassi/OpenFIRE-PICON-ESP32/PICON-OG/STL/bearing-solenoid-mount-2mm.stl

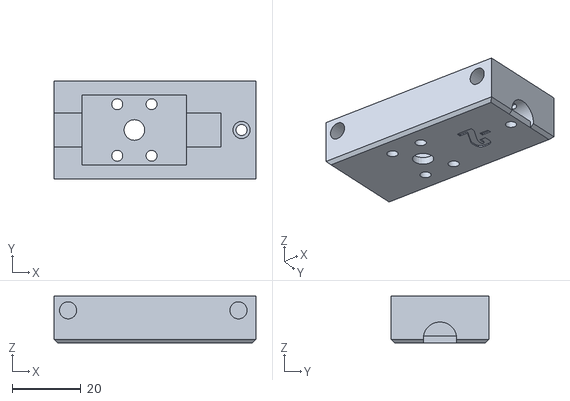
[picture p239: CAD file, 2025-09-09]
PICON-OG/STL/bearing-solenoid-mount-2mm.stl
58.8 x 28.4 x 13.5
