alessandro-satanassi/OpenFIRE-PICON-ESP32/web/files/Pin.STL

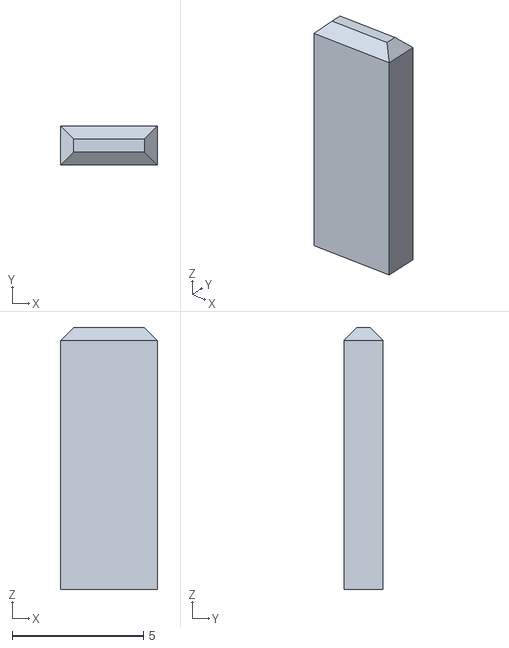
[picture p240: CAD file, 2026-08-09]
web/files/Pin.STL
3.70 x 1.50 x 10.0
