alessandro-satanassi/OpenFIRE-PICON-ESP32/FreeCAD/Parts/Camera IR.STEP

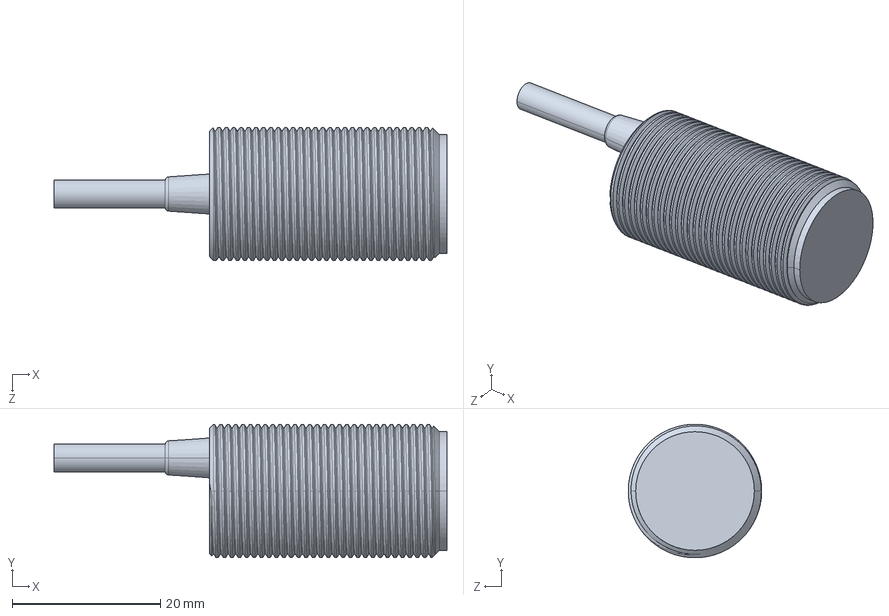
[picture p241: CAD file, 2026-03-09]
FreeCAD/Parts/Camera IR.STEP
53.0 x 18.0 x 18.0 mm
