alessandro-satanassi/OpenFIRE-PICON-ESP32/FreeCAD/STL_PICON_AS/ORIGINALI_PICON_OG/GRILLETTO/trigger.stl

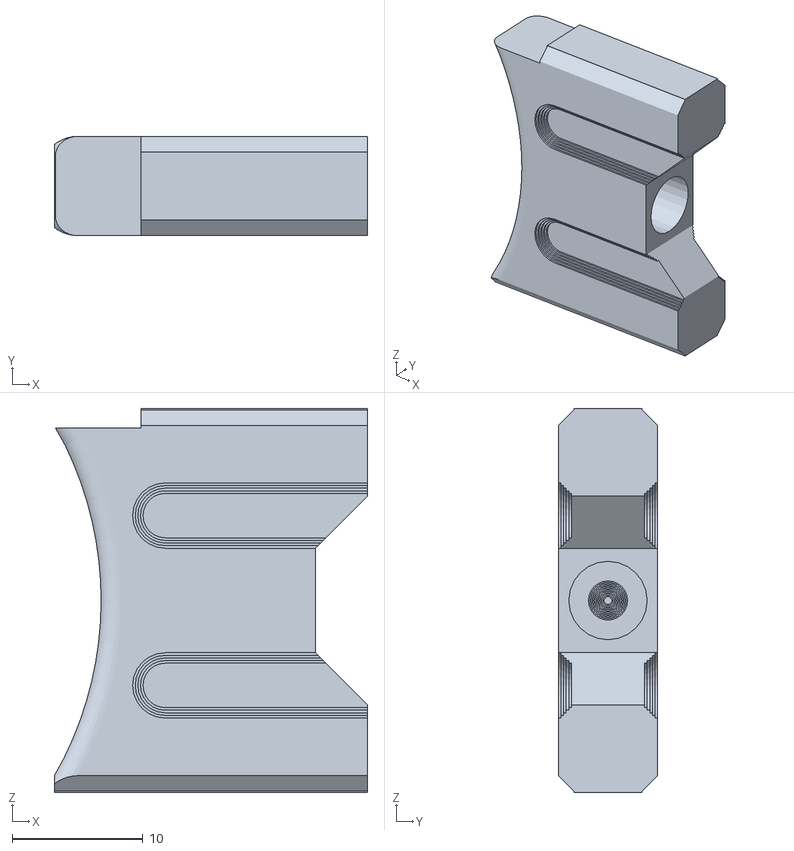
[picture p242: CAD file, 2025-09-09]
FreeCAD/STL_PICON_AS/ORIGINALI_PICON_OG/GRILLETTO/trigger.stl
24.0 x 7.60 x 29.4
