alessandro-satanassi/OpenFIRE-PICON-ESP32/FreeCAD/STL_PICON_AS/ORIGINALI_PICON_OG/MECCANISMO_POMPA/pump.stl

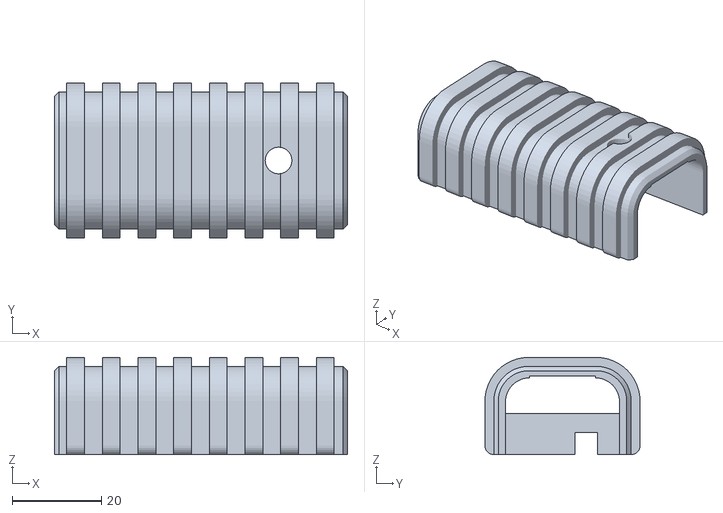
[picture p243: CAD file, 2025-09-09]
FreeCAD/STL_PICON_AS/ORIGINALI_PICON_OG/MECCANISMO_POMPA/pump.stl
65.7 x 34.8 x 21.8
