alessandro-satanassi/OpenFIRE-PICON-ESP32/PICON-OG/STL/front-5-way-navigation.stl

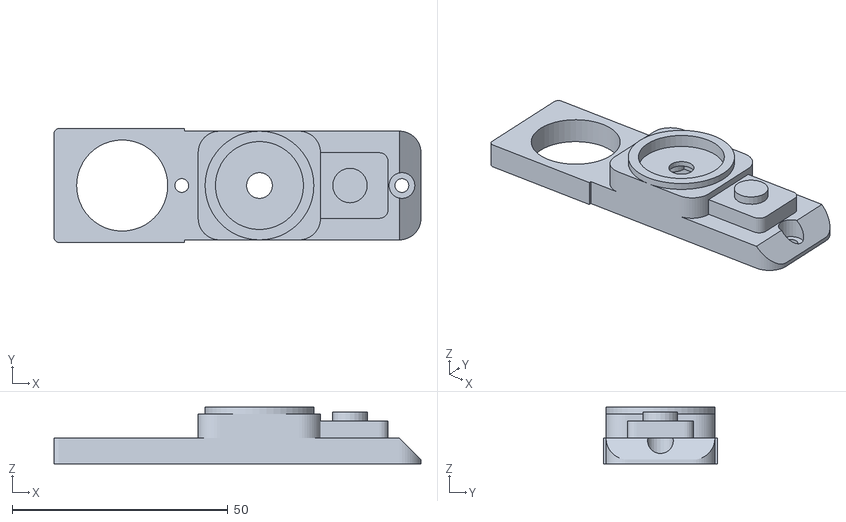
[picture p244: CAD file, 2025-09-09]
PICON-OG/STL/front-5-way-navigation.stl
85.0 x 26.4 x 13.2
