alessandro-satanassi/OpenFIRE-PICON-ESP32/web/files/Plate-Right.STL

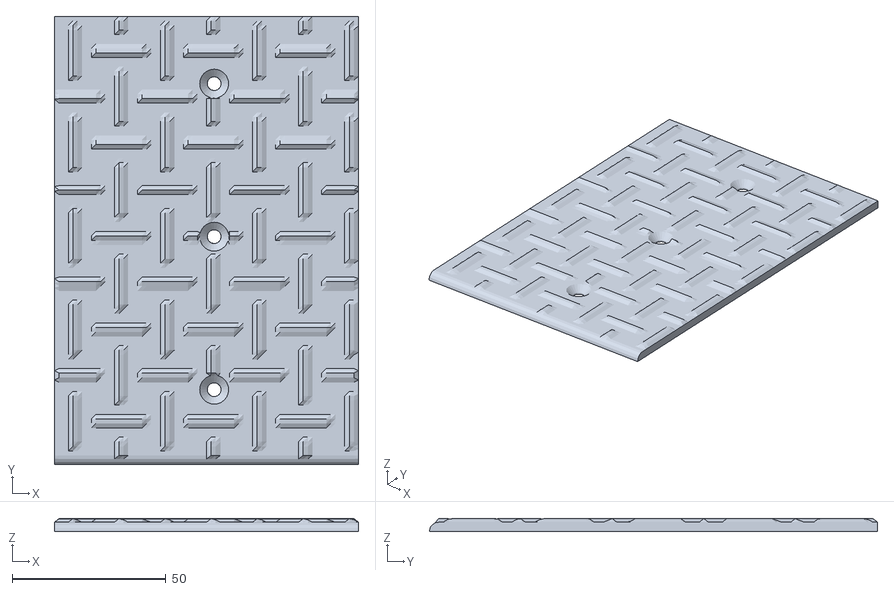
[picture p245: CAD file, 2026-08-09]
web/files/Plate-Right.STL
99.0 x 146.0 x 4.20
