alessandro-satanassi/OpenFIRE-PICON-ESP32/FreeCAD/Parts/LR7843 MOSFET Module.STEP

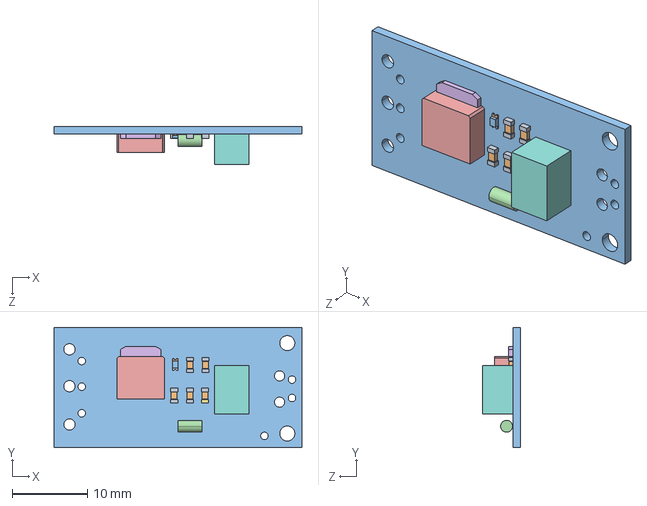
[picture p246: CAD file, 2026-03-09]
FreeCAD/Parts/LR7843 MOSFET Module.STEP
33.0 x 16.0 x 5.01 mm
