alessandro-satanassi/OpenFIRE-PICON-ESP32/FreeCAD/STL_PICON_AS/ORIGINALI_PICON_OG/GRILLETTO/trigger-guard-left.stl

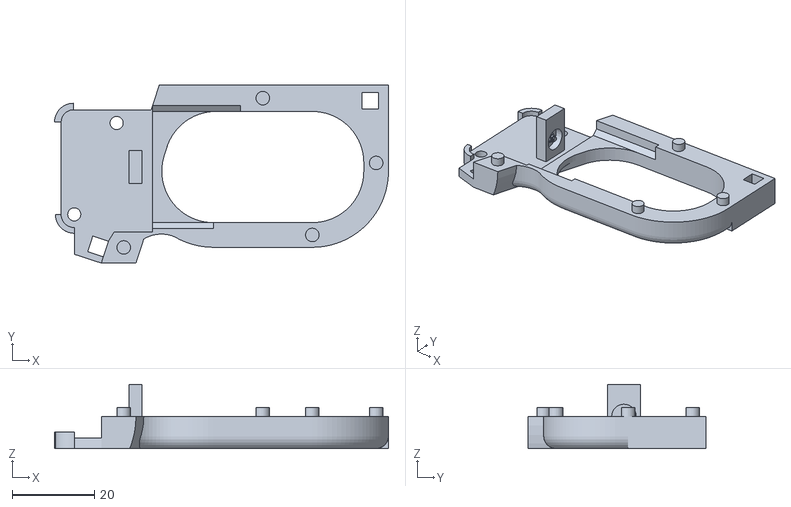
[picture p247: CAD file, 2025-09-09]
FreeCAD/STL_PICON_AS/ORIGINALI_PICON_OG/GRILLETTO/trigger-guard-left.stl
81.1 x 43.3 x 15.6
