alessandro-satanassi/OpenFIRE-PICON-ESP32/PICON-OG/STL/front-button-spacer-1.stl

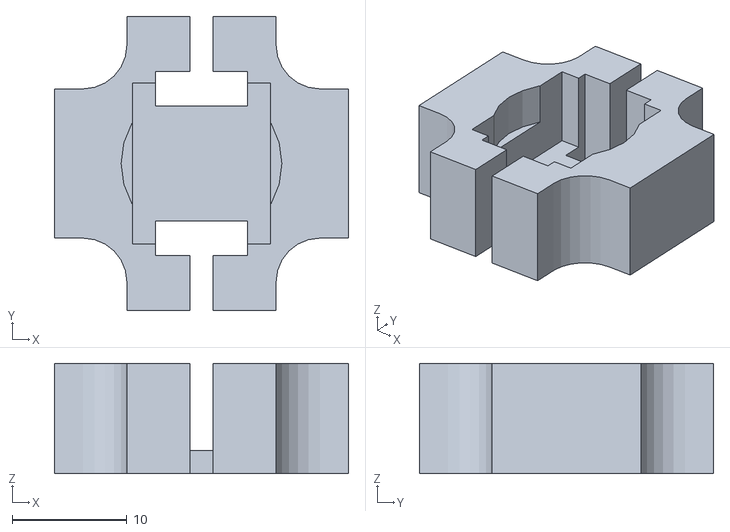
[picture p248: CAD file, 2025-09-09]
PICON-OG/STL/front-button-spacer-1.stl
25.6 x 25.6 x 9.60
