alessandro-satanassi/OpenFIRE-PICON-ESP32/STL/neopixel con base e smusso.stl

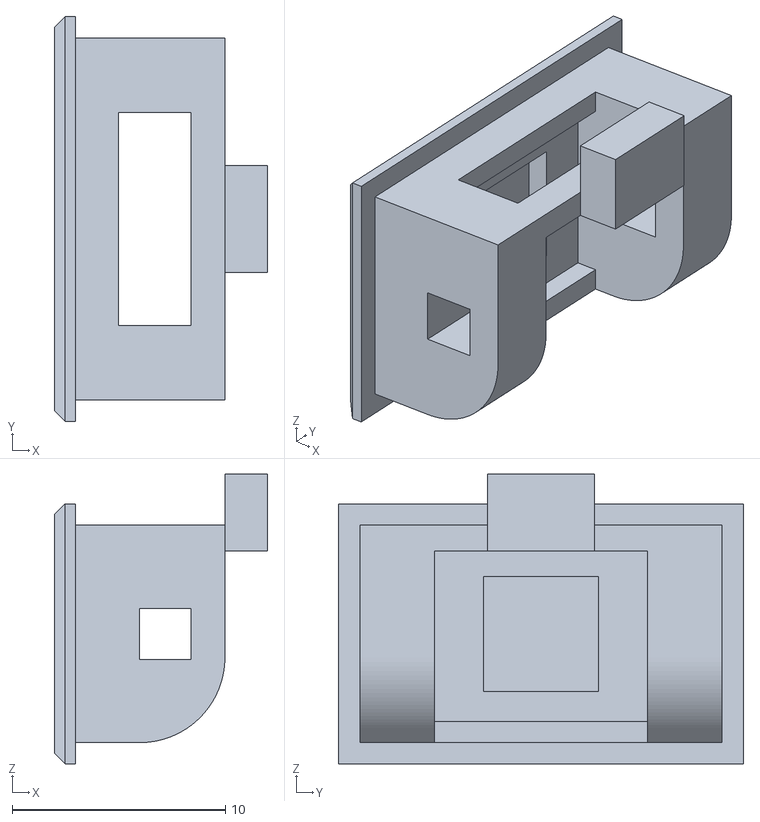
[picture p249: CAD file, 2025-09-20]
STL/neopixel con base e smusso.stl
10.0 x 19.0 x 13.6
