alessandro-satanassi/OpenFIRE-PICON-ESP32/FreeCAD/Parts/Rail Block.STEP

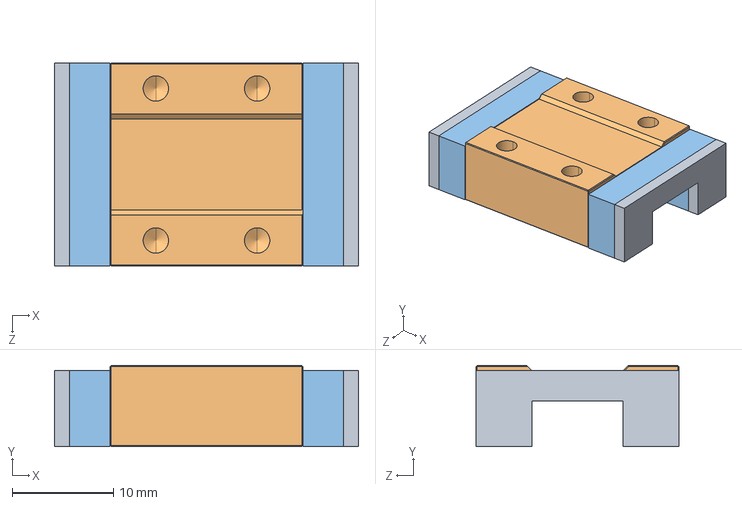
[picture p250: CAD file, 2026-03-09]
FreeCAD/Parts/Rail Block.STEP
30.0 x 8.00 x 20.0 mm
