alessandro-satanassi/OpenFIRE-PICON-ESP32/PICON-OG/STL/slide-picatinny-oled.stl

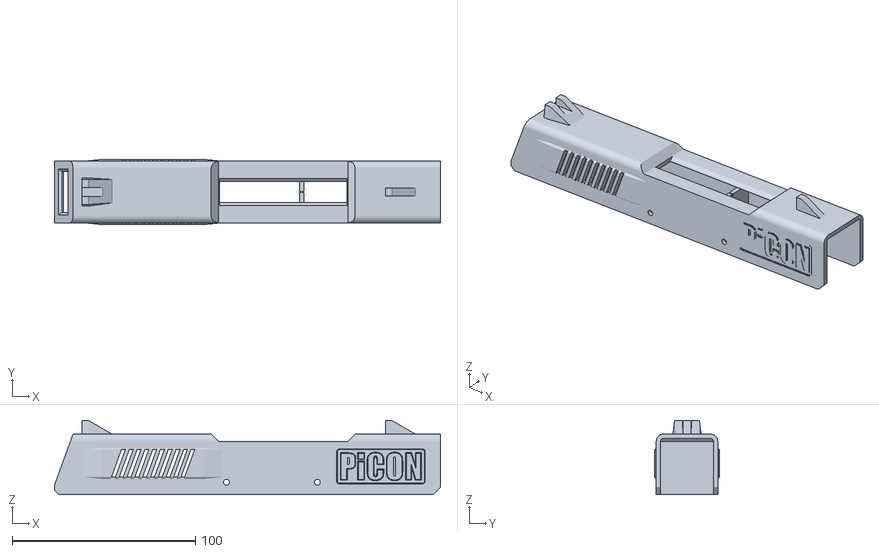
[picture p251: CAD file, 2025-09-09]
PICON-OG/STL/slide-picatinny-oled.stl
210.6 x 35.6 x 40.4
