alessandro-satanassi/OpenFIRE-PICON-ESP32/STL/PICON-OF_ver_6-Extrude perno fermo rumble _ varie misure.3mf

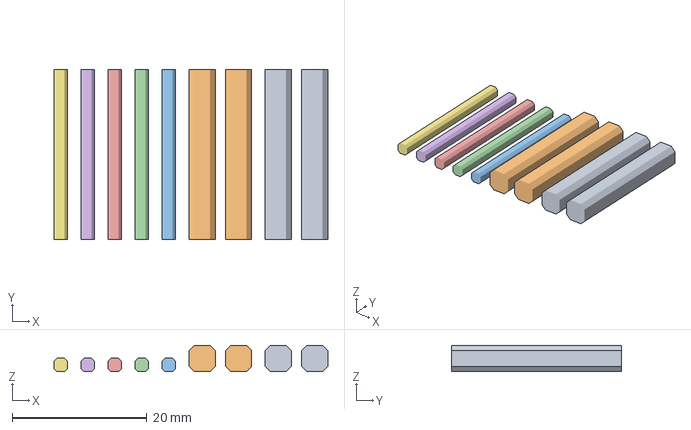
[picture p252: CAD file, 2025-09-20]
STL/PICON-OF_ver_6-Extrude perno fermo rumble _ varie misure.3mf
40.6 x 25.2 x 3.90 mm
trigger-guard-pins (1).stl x 2
PICON-OF_ver_6-Extrude perno fermo rumble.stl x 5
