alessandro-satanassi/OpenFIRE-PICON-ESP32/web/files/Pedal-Select.STL

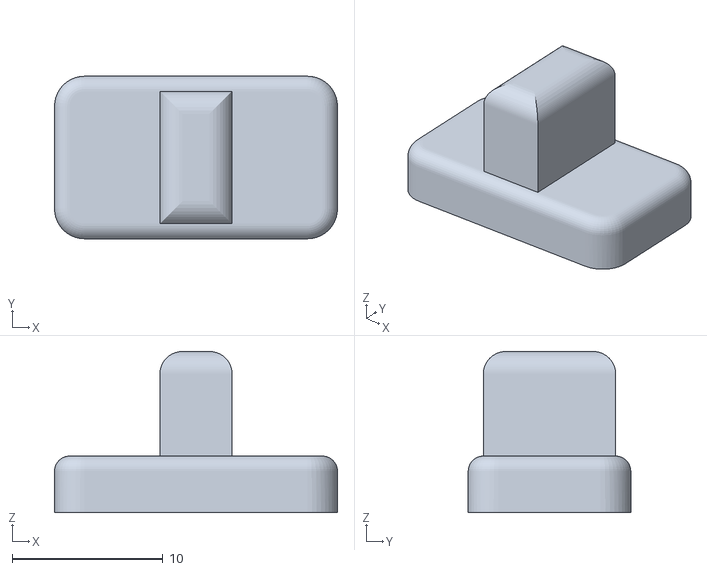
[picture p253: CAD file, 2026-08-09]
web/files/Pedal-Select.STL
18.8 x 10.8 x 10.7
