alessandro-satanassi/OpenFIRE-PICON-ESP32/FreeCAD/Parts/Trigger Switch.STEP

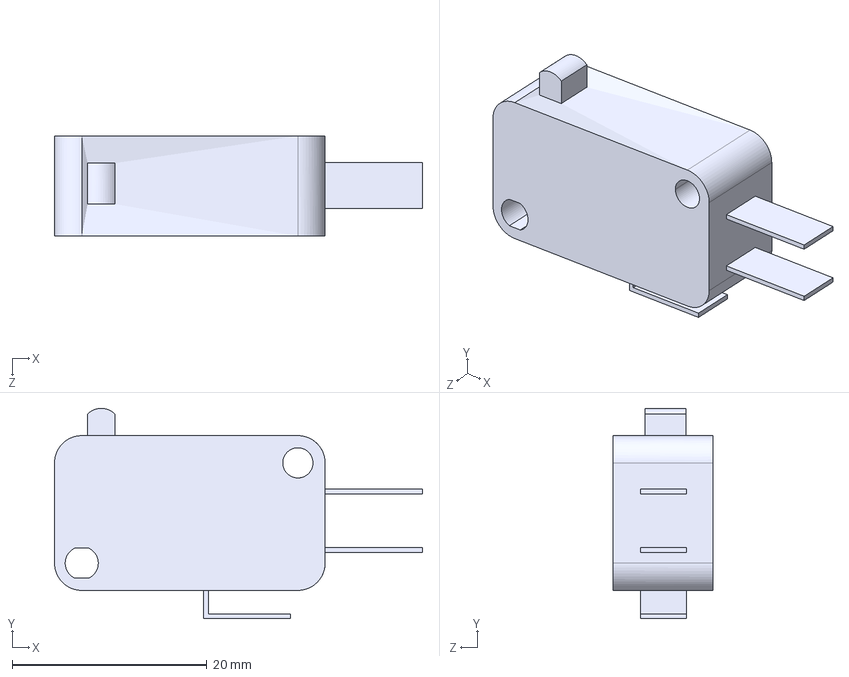
[picture p254: CAD file, 2026-03-09]
FreeCAD/Parts/Trigger Switch.STEP
37.8 x 21.6 x 10.3 mm
