alessandro-satanassi/OpenFIRE-PICON-ESP32/FreeCAD/PICON-AS-EXPLODED - ver.4.FCStd

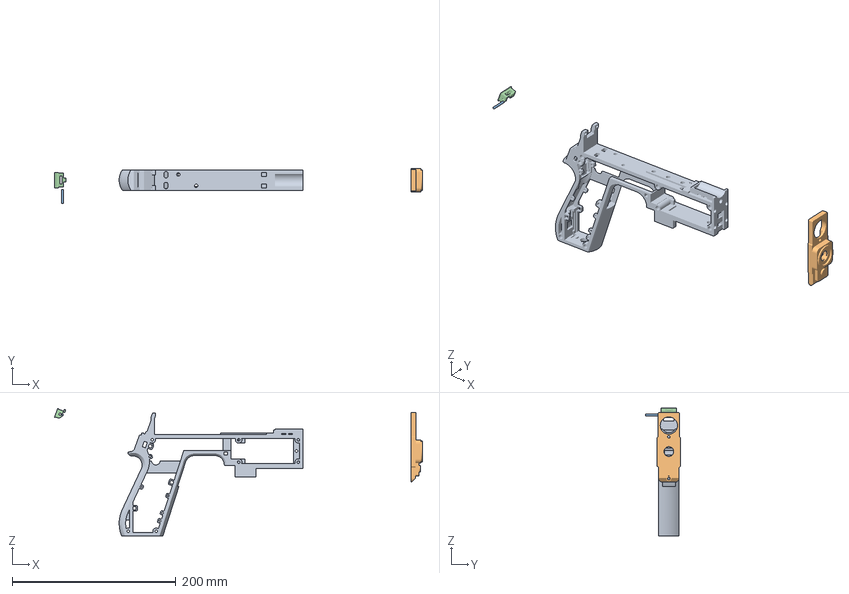
[picture p255: CAD file, 2026-03-09]
FreeCAD/PICON-AS-EXPLODED - ver.4.FCStd
449.8 x 42.7 x 155.9 mm
PICON-OF_ver_64-Cut055
frontale_analogico_corretto-Cut
PICON-OF_ver_37-perno fermo neopixel
PICON-OF_ver_37-supporto per neopixel
