alessandro-satanassi/OpenFIRE-PICON-ESP32/PICON-OG/STL/bearing-solenoid-mount-1mm-1.stl

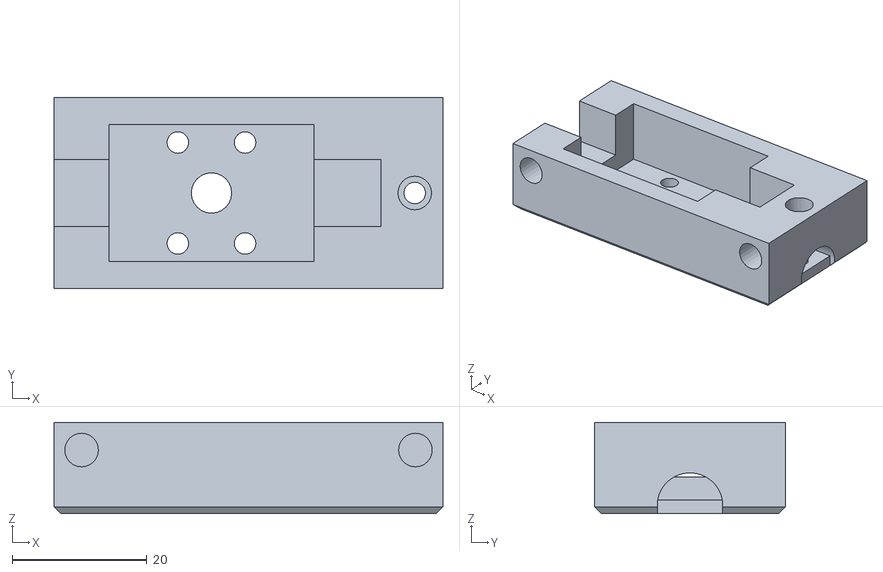
[picture p256: CAD file, 2025-09-09]
PICON-OG/STL/bearing-solenoid-mount-1mm-1.stl
57.8 x 28.4 x 13.5
