alessandro-satanassi/OpenFIRE-PICON-ESP32/web/files/Base_Batt.STL

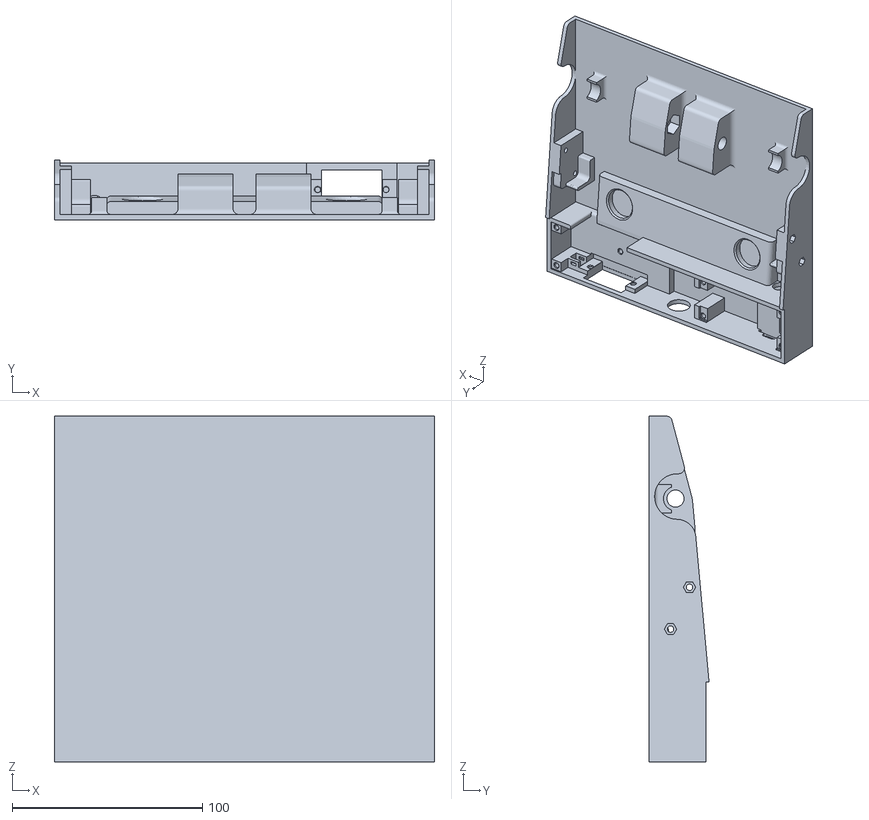
[picture p257: CAD file, 2026-08-09]
web/files/Base_Batt.STL
200.0 x 31.7 x 182.0
