alessandro-satanassi/OpenFIRE-PICON-ESP32/PICON-OG/STL/left-side-3-buttons.stl

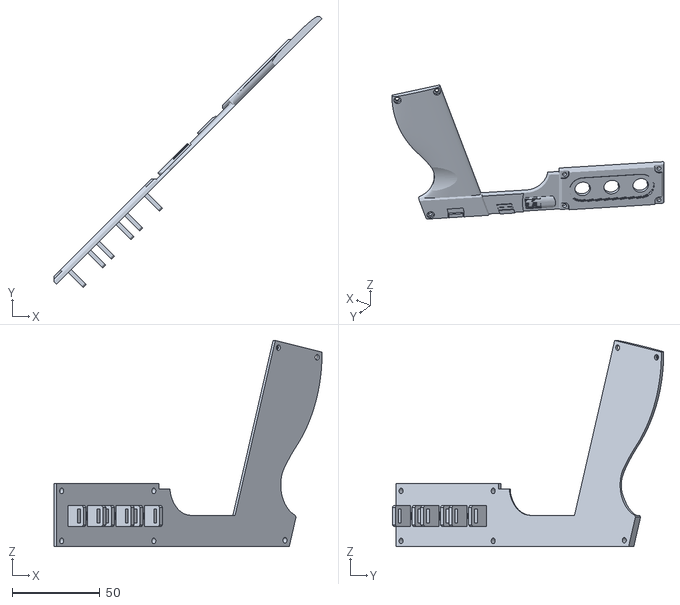
[picture p259: CAD file, 2025-09-09]
PICON-OG/STL/left-side-3-buttons.stl
152.9 x 154.7 x 117.5
