alessandro-satanassi/OpenFIRE-PICON-ESP32/FreeCAD/Parts/Rail Rail.STEP

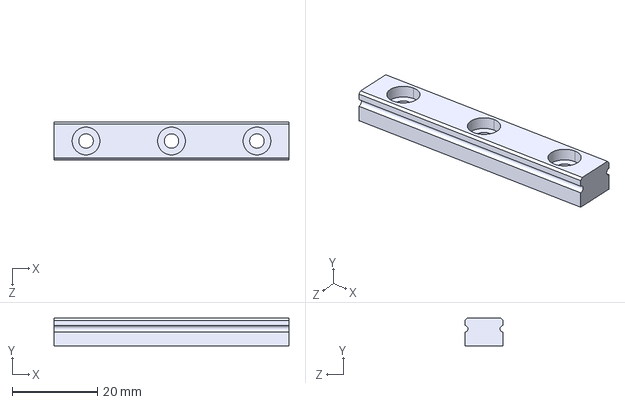
[picture p260: CAD file, 2026-03-09]
FreeCAD/Parts/Rail Rail.STEP
55.0 x 6.50 x 9.00 mm
