alessandro-satanassi/OpenFIRE-PICON-ESP32/PICON-OG/STL/back-hidden-rgb-led-2.stl

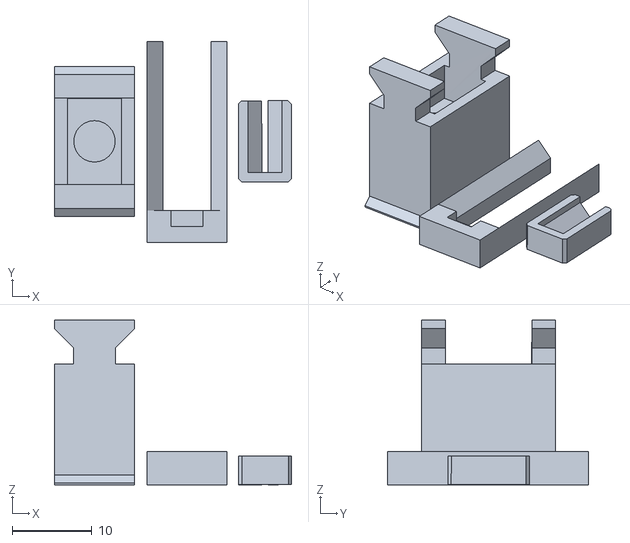
[picture p261: CAD file, 2025-09-09]
PICON-OG/STL/back-hidden-rgb-led-2.stl
29.7 x 25.2 x 20.6
