alessandro-satanassi/OpenFIRE-PICON-ESP32/web/files/Button-Cap.STL

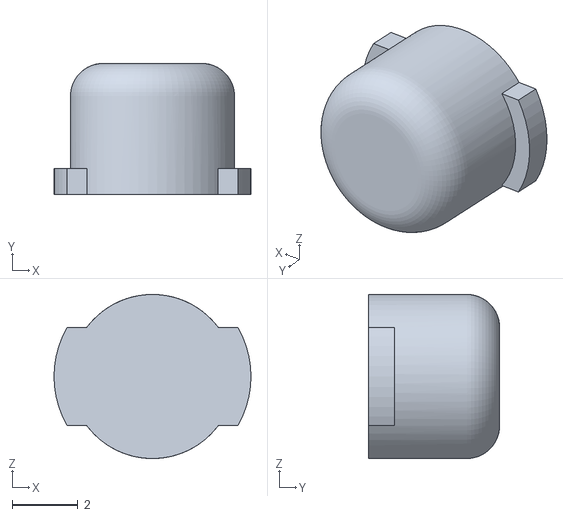
[picture p262: CAD file, 2026-08-09]
web/files/Button-Cap.STL
6.00 x 4.00 x 5.00
