alessandro-satanassi/OpenFIRE-PICON-ESP32/FreeCAD/Parts/Slide Switch.STEP

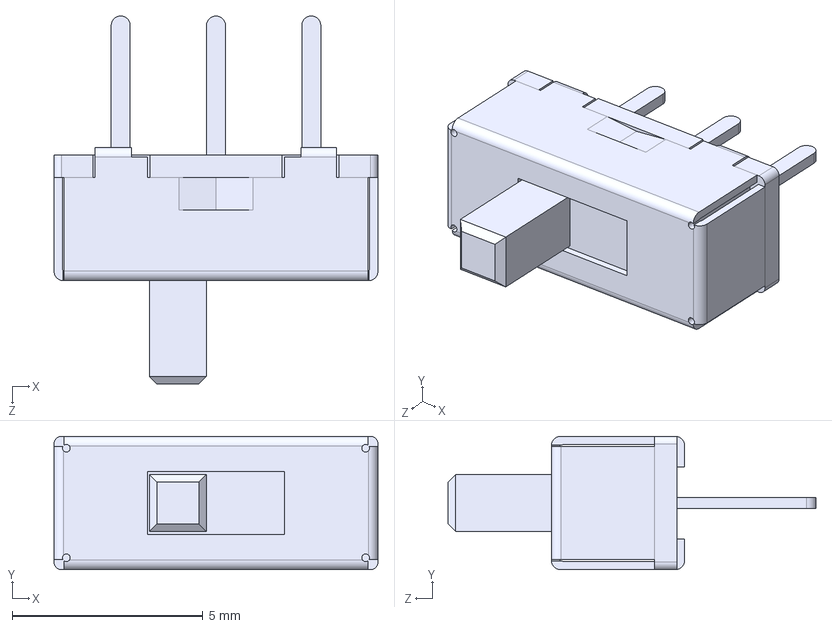
[picture p263: CAD file, 2026-03-09]
FreeCAD/Parts/Slide Switch.STEP
8.50 x 3.50 x 9.66 mm
