alessandro-satanassi/OpenFIRE-PICON-ESP32/PICON-OG/STL/butt-plug-1.stl

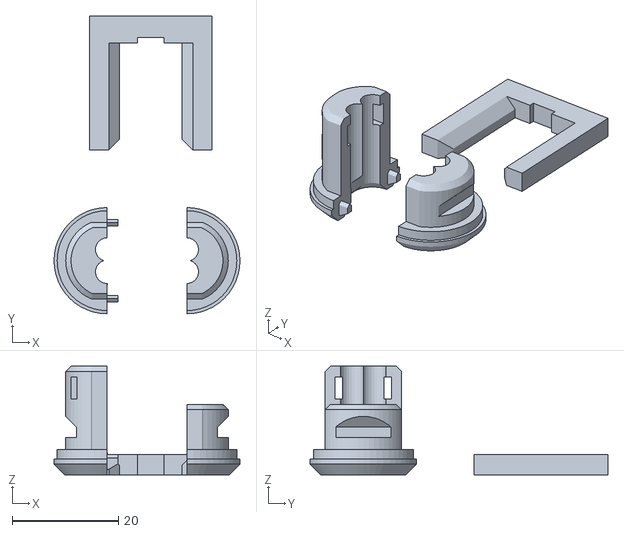
[picture p264: CAD file, 2025-09-09]
PICON-OG/STL/butt-plug-1.stl
35.0 x 56.0 x 20.4
