alessandro-satanassi/OpenFIRE-PICON-ESP32/STL/13_dopo_inclusione.stl

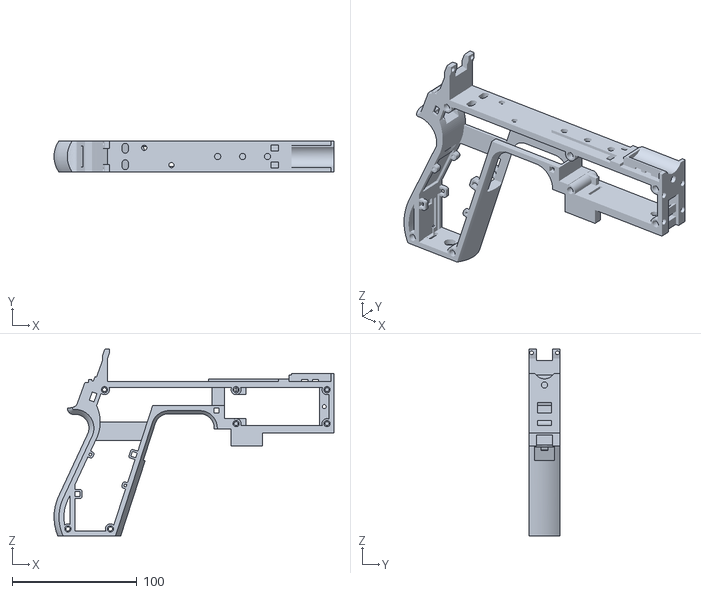
[picture p265: CAD file, 2025-09-11]
STL/13_dopo_inclusione.stl
224.6 x 25.2 x 149.8
