alessandro-satanassi/OpenFIRE-PICON-ESP32/web/files/case_ir_led_tx_ver_04.FCStd

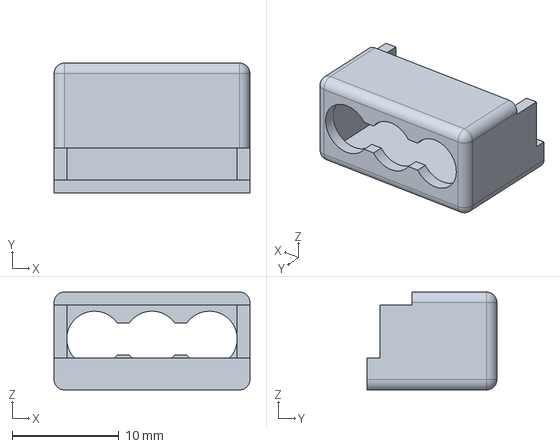
[picture p266: CAD file, 2026-06-12]
web/files/case_ir_led_tx_ver_04.FCStd
18.4 x 12.2 x 9.20 mm
