alessandro-satanassi/OpenFIRE-PICON-ESP32/FreeCAD/Parts/OLED.STEP

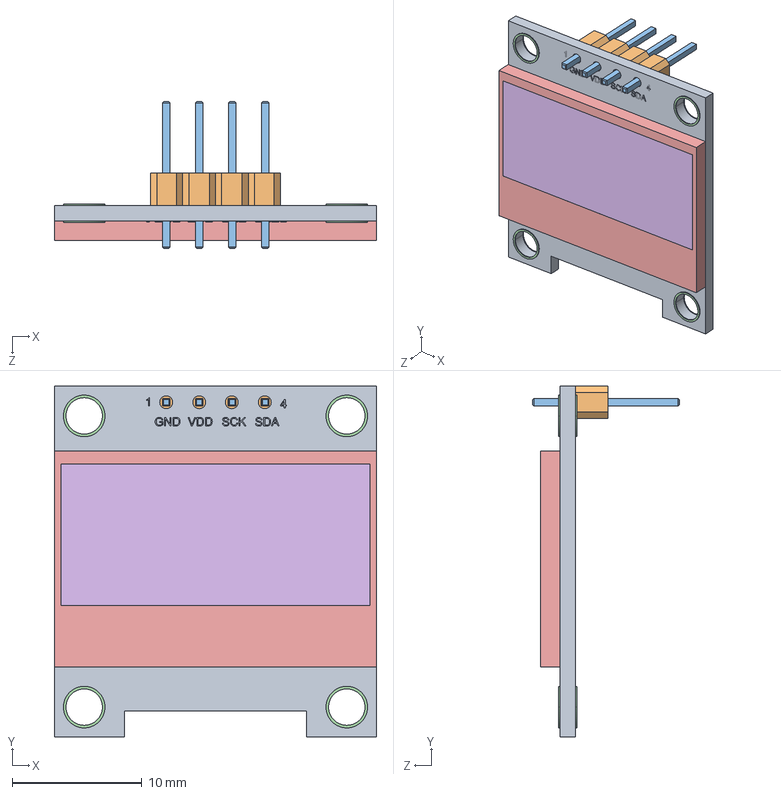
[picture p267: CAD file, 2026-03-09]
FreeCAD/Parts/OLED.STEP
24.8 x 27.0 x 11.3 mm
SSD1315_PCB.step
4_Pins_Header.step
11.3_mm_PIN.step x 4
Lead_Ring.step x 8
OLED_Frame.step
OLED_Screen.step
