alessandro-satanassi/OpenFIRE-PICON-ESP32/PICON-OG/STL/back-switch.stl

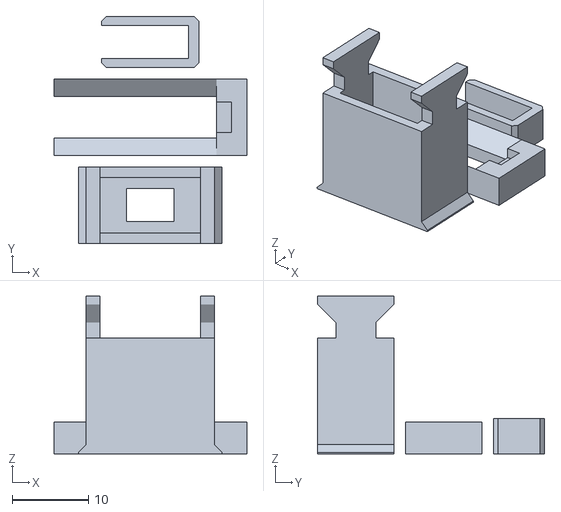
[picture p268: CAD file, 2025-09-09]
PICON-OG/STL/back-switch.stl
25.2 x 29.7 x 20.6
