alessandro-satanassi/OpenFIRE-PICON-ESP32/PICON-OG/STL/gun-sights-3mm-led.stl

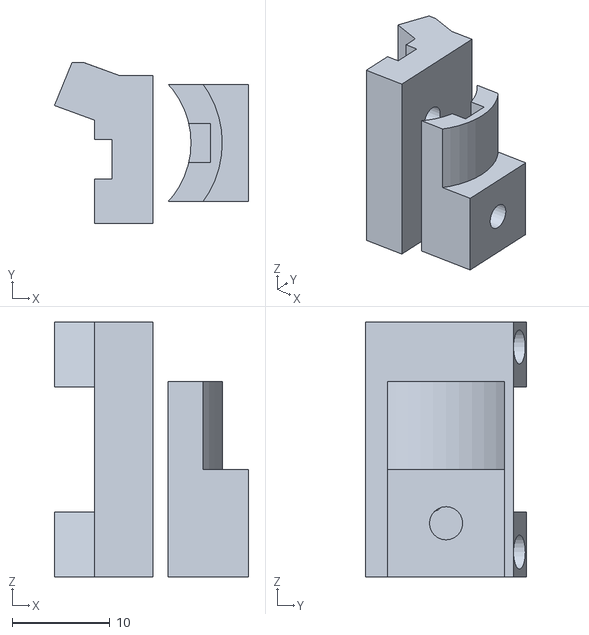
[picture p269: CAD file, 2025-09-09]
PICON-OG/STL/gun-sights-3mm-led.stl
19.9 x 16.5 x 26.1
