alessandro-satanassi/OpenFIRE-PICON-ESP32/FreeCAD/Parts/Vibration Module.STEP

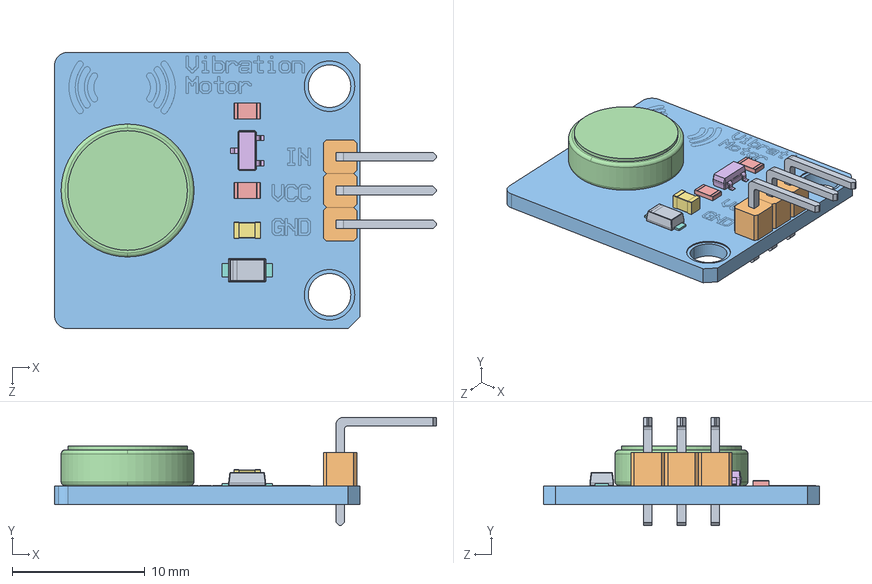
[picture p270: CAD file, 2026-03-09]
FreeCAD/Parts/Vibration Module.STEP
28.8 x 8.15 x 20.8 mm
Pin.step x 3
Header_Body.step x 3
PCB.step
Motor.step
R_0805_2012Metric.step x 2
SOT_23.step
C_0805_2012Metric.step
SOD-123F.step
