alessandro-satanassi/OpenFIRE-PICON-ESP32/PICON-OG/STL/side-3-button-pins.stl

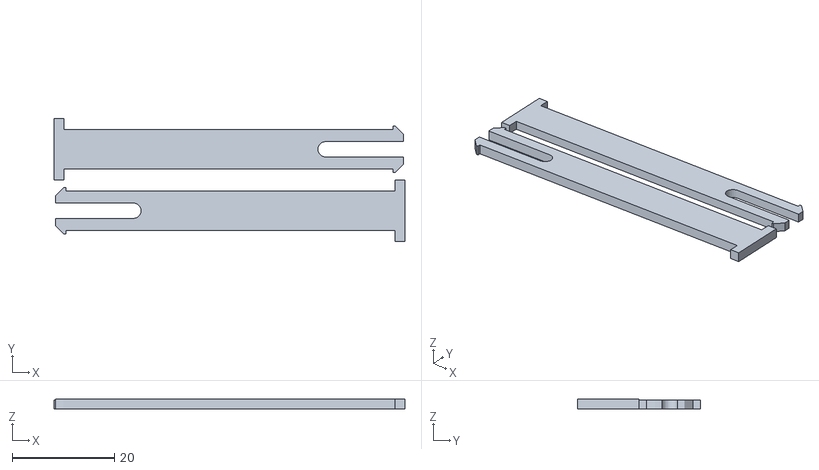
[picture p271: CAD file, 2025-09-09]
PICON-OG/STL/side-3-button-pins.stl
68.5 x 24.0 x 2.00
