alessandro-satanassi/OpenFIRE-PICON-ESP32/web/files/Lid.STL

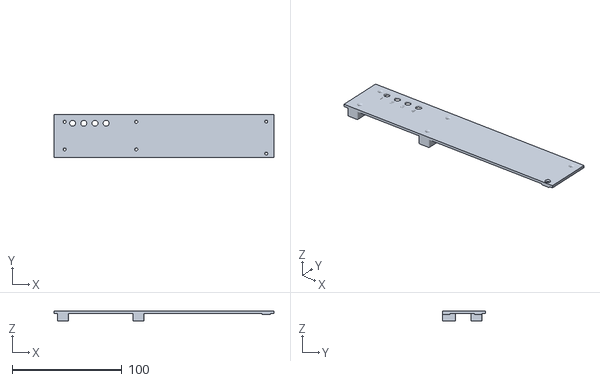
[picture p272: CAD file, 2026-05-05]
web/files/Lid.STL
200.0 x 38.8 x 8.85
