alessandro-satanassi/OpenFIRE-PICON-ESP32/FreeCAD/Parts/MP3429.STEP

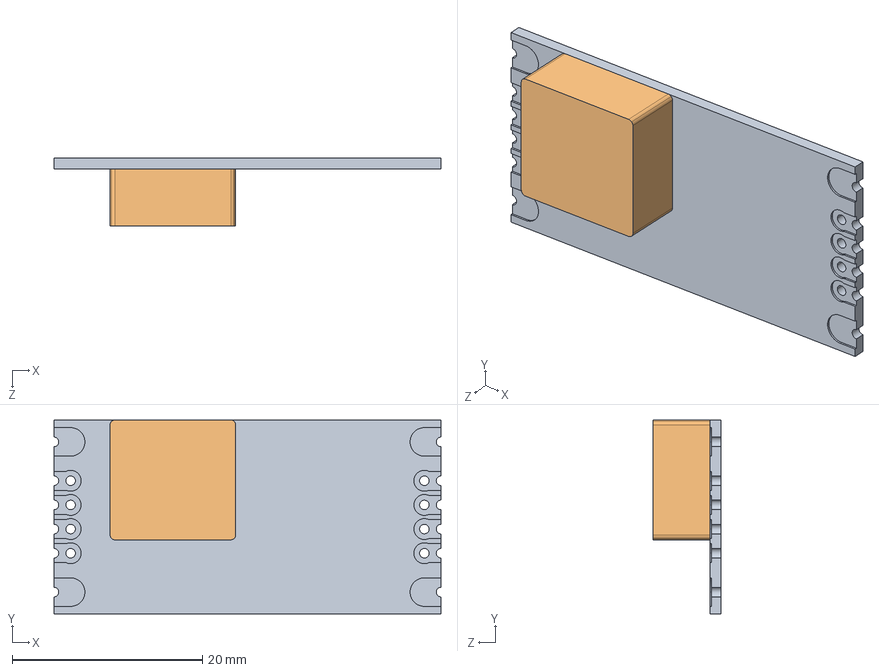
[picture p273: CAD file, 2026-03-09]
FreeCAD/Parts/MP3429.STEP
40.7 x 20.4 x 7.20 mm
