alessandro-satanassi/OpenFIRE-PICON-ESP32/PICON-OG/STL/left-side-2-buttons.stl

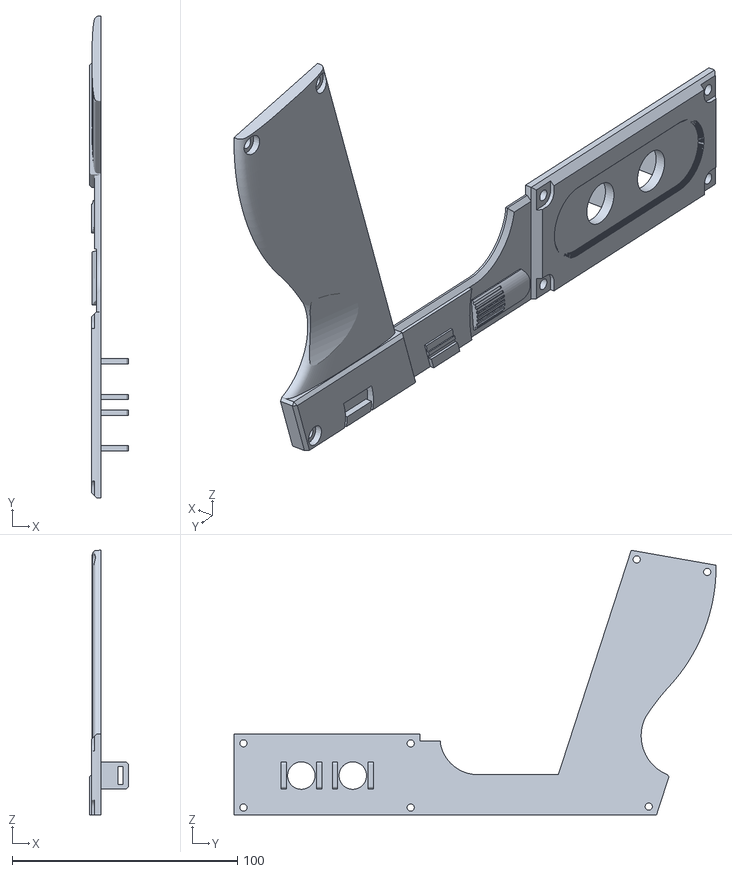
[picture p274: CAD file, 2025-09-09]
PICON-OG/STL/left-side-2-buttons.stl
17.4 x 214.2 x 117.5
