alessandro-satanassi/OpenFIRE-PICON-ESP32/PICON-OG/STL/picatinny-rail-1.stl

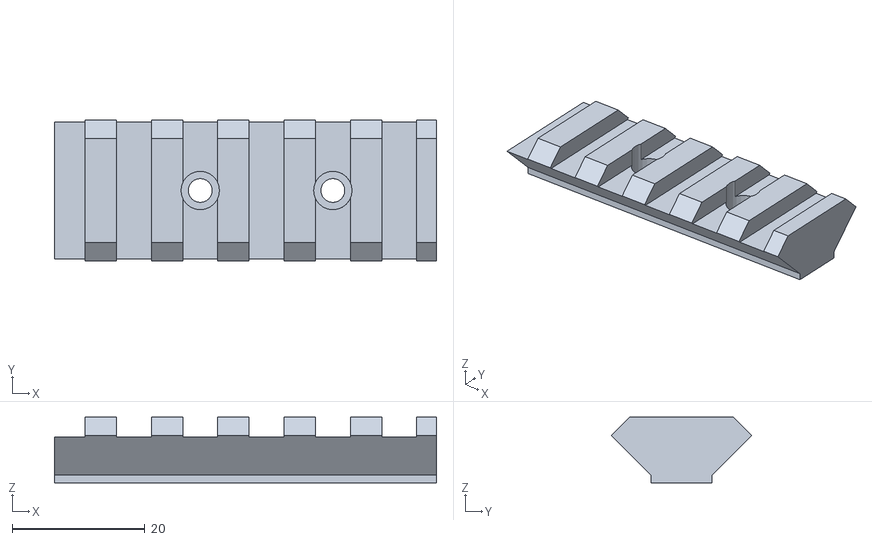
[picture p275: CAD file, 2025-09-09]
PICON-OG/STL/picatinny-rail-1.stl
57.6 x 21.2 x 9.93
