alessandro-satanassi/OpenFIRE-PICON-ESP32/web/files/Pedal-Frame.STL

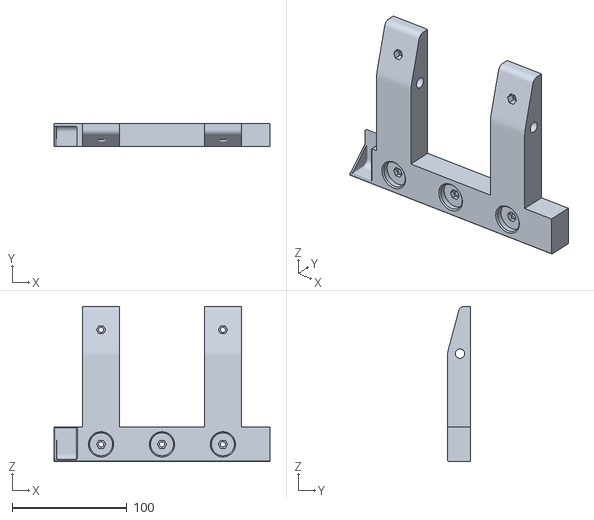
[picture p276: CAD file, 2026-05-05]
web/files/Pedal-Frame.STL
188.0 x 20.0 x 135.0
