alessandro-satanassi/OpenFIRE-PICON-ESP32/PICON-OG/STL/picatinny-rail-mount-1.stl

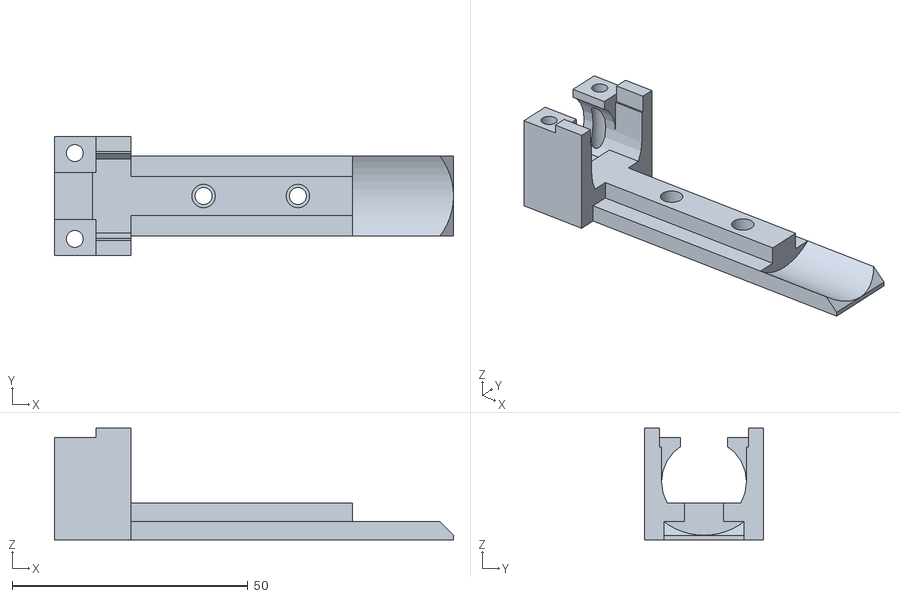
[picture p277: CAD file, 2025-09-09]
PICON-OG/STL/picatinny-rail-mount-1.stl
84.6 x 25.2 x 23.7
