alessandro-satanassi/OpenFIRE-PICON-ESP32/web/files/Plate.STL

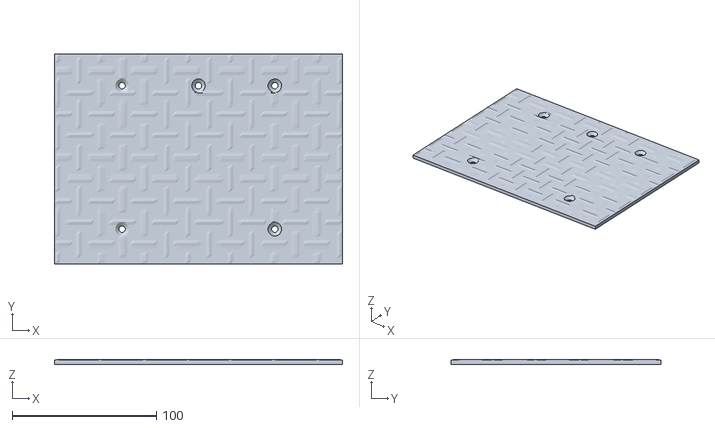
[picture p278: CAD file, 2026-05-05]
web/files/Plate.STL
200.0 x 145.6 x 3.50
