alessandro-satanassi/OpenFIRE-PICON-ESP32/PICON-OG/STL/rumble-guard-1.stl

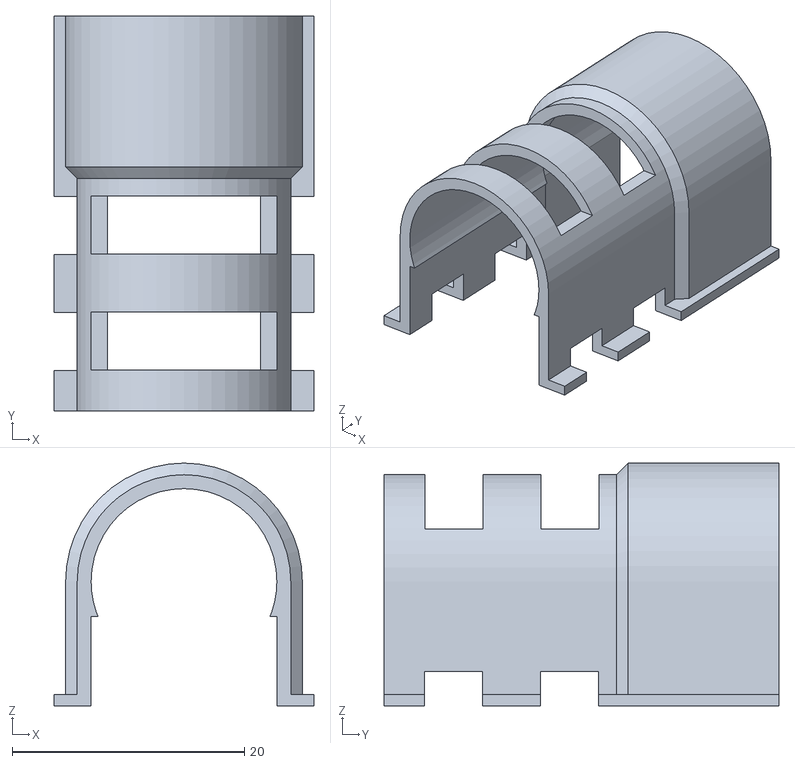
[picture p279: CAD file, 2025-09-09]
PICON-OG/STL/rumble-guard-1.stl
22.4 x 34.0 x 20.9
