alessandro-satanassi/OpenFIRE-PICON-ESP32/web/files/frontale_analogico_corretto.FCStd

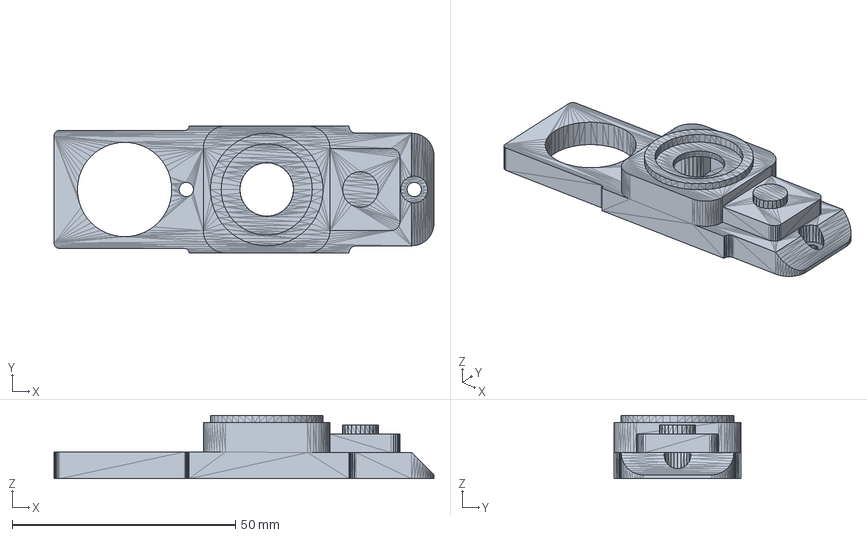
[picture p280: CAD file, 2026-03-09]
web/files/frontale_analogico_corretto.FCStd
85.0 x 28.4 x 14.2 mm
