alessandro-satanassi/OpenFIRE-PICON-ESP32/PICON-OG/STL/slide-picatinny-1.stl

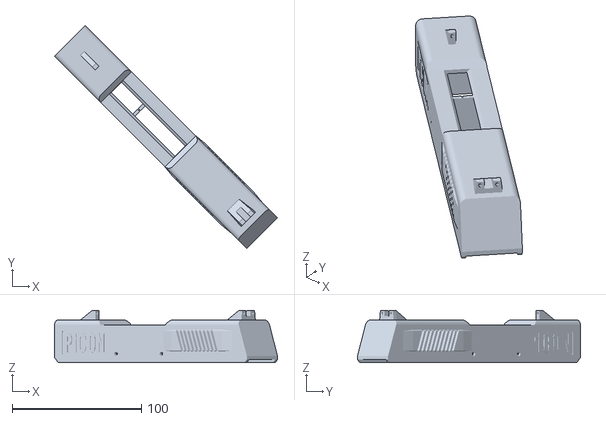
[picture p281: CAD file, 2025-09-09]
PICON-OG/STL/slide-picatinny-1.stl
172.7 x 172.7 x 40.4
