alessandro-satanassi/OpenFIRE-PICON-ESP32/FreeCAD/PICON-OF_ver_61-Protezione_inferiore_batteria.stl

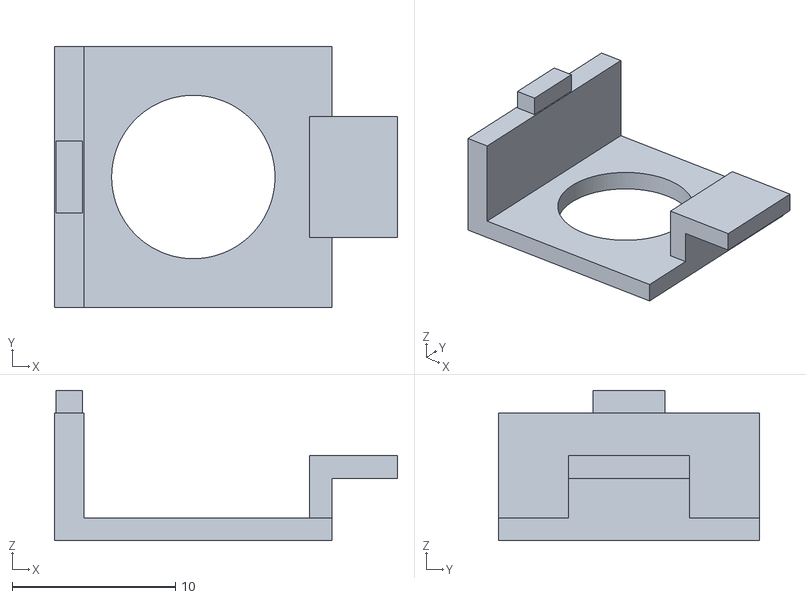
[picture p282: CAD file, 2026-03-09]
FreeCAD/PICON-OF_ver_61-Protezione_inferiore_batteria.stl
21.0 x 16.0 x 9.20
