alessandro-satanassi/OpenFIRE-PICON-ESP32/PICON-OG/STL/side-2-button-pins.stl

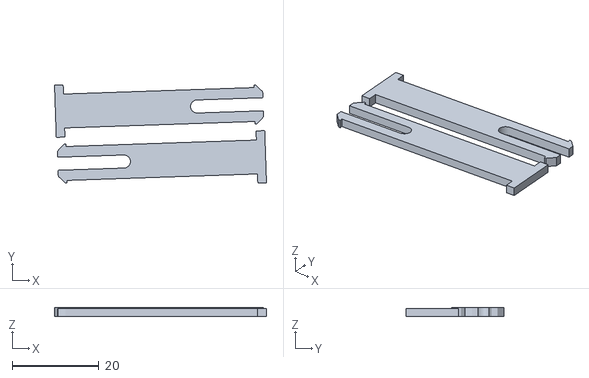
[picture p283: CAD file, 2025-09-09]
PICON-OG/STL/side-2-button-pins.stl
48.7 x 22.6 x 2.00
