alessandro-satanassi/OpenFIRE-PICON-ESP32/PICON-OG/STL/frame-40mm-bearing-rail-1.stl

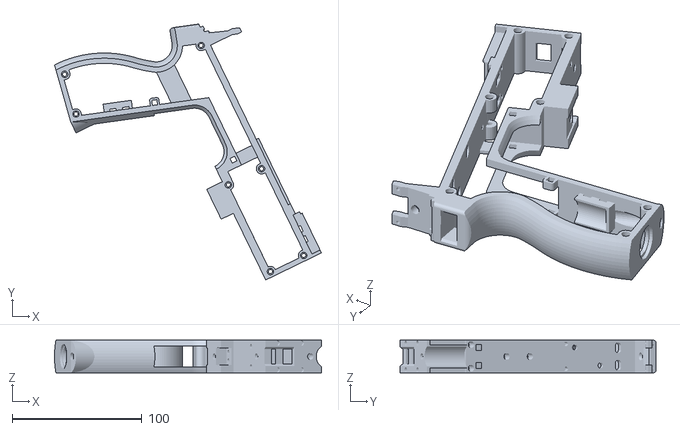
[picture p284: CAD file, 2025-09-09]
PICON-OG/STL/frame-40mm-bearing-rail-1.stl
205.8 x 197.3 x 25.2
