alessandro-satanassi/OpenFIRE-PICON-ESP32/PICON-OG/STL/right-side-nav-module.stl

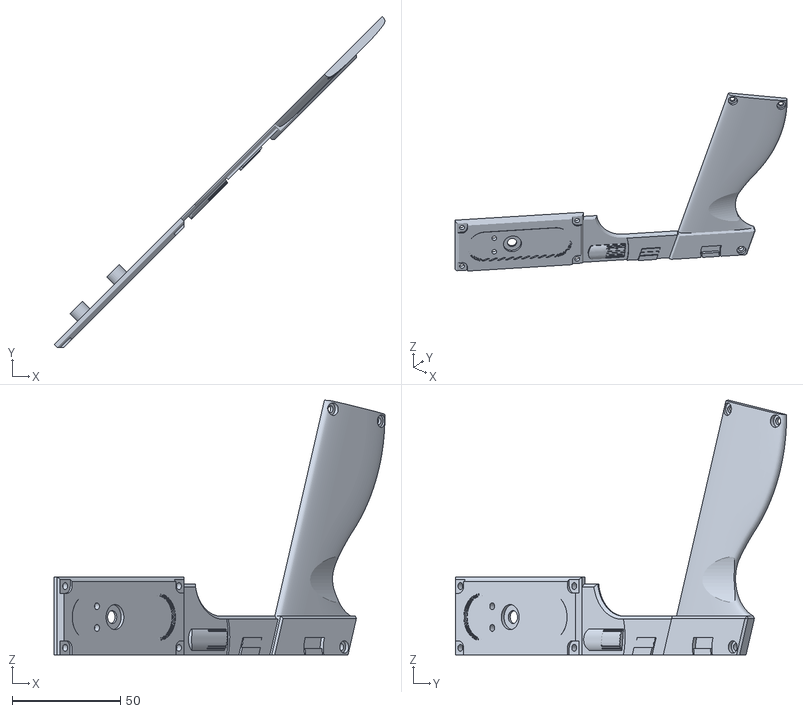
[picture p285: CAD file, 2025-09-09]
PICON-OG/STL/right-side-nav-module.stl
152.8 x 152.9 x 117.5
