alessandro-satanassi/OpenFIRE-PICON-ESP32/PICON-OG/STL/right-side-2-large-pushbuttons.stl

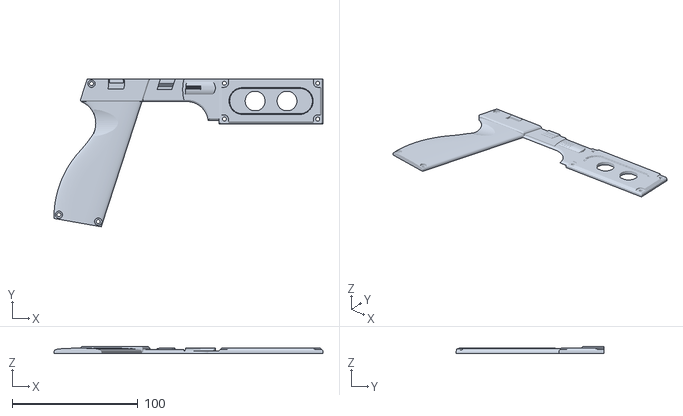
[picture p286: CAD file, 2025-09-09]
PICON-OG/STL/right-side-2-large-pushbuttons.stl
214.2 x 117.5 x 5.20
