alessandro-satanassi/OpenFIRE-PICON-ESP32/FreeCAD/PICON-AS-EXPLODED - INIZIALE exploded - ver.12 - completa_pezzi_posizionati.FCStd

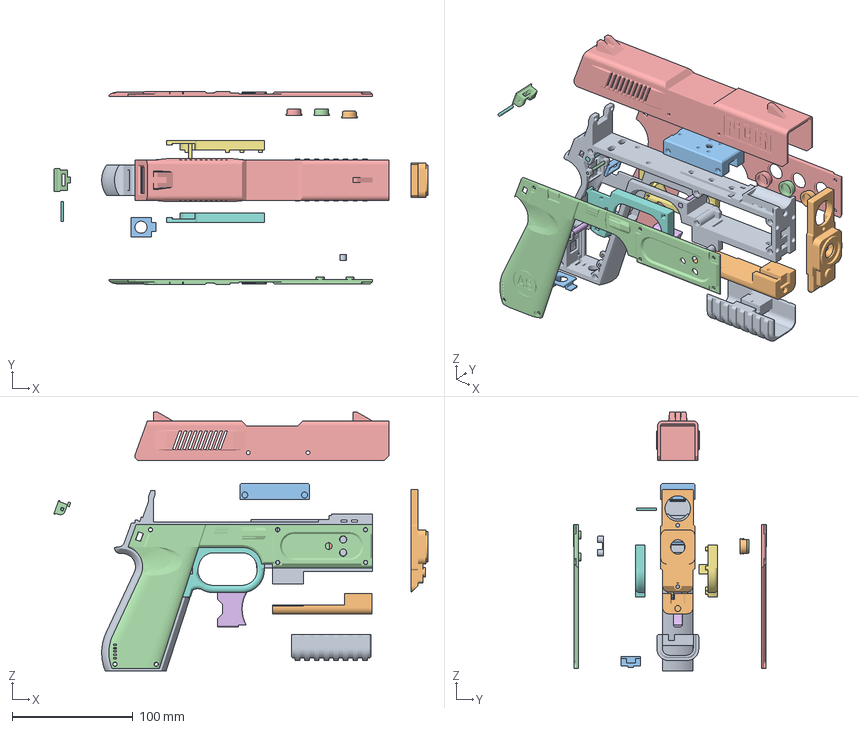
[picture p287: CAD file, 2026-03-09]
FreeCAD/PICON-AS-EXPLODED - INIZIALE exploded - ver.12 - completa_pezzi_posizionati.FCStd
310.3 x 160.2 x 214.8 mm
PICON-OF_ver_64-Cut055
frontale_analogico_corretto-Cut
PICON-OF_ver_37-blocco switch
PICON-OF_ver_53-lato DX
PICON-OF_ver_52-lato SX
PICON-OF_ver_37-perno fermo grilletto -front
PICON-OF_ver_37-perno fermo rumble
PICON-OF_ver_37-perno fermo neopixel
PICON-OF_ver_37-pulsanti lato destro
PICON-OF_ver_37-pulsanti lato sinistro_A
PICON-OF_ver_61-Protezione_inferiore_batteria
PICON-OF_ver_37-supporto per neopixel
slide-oled
trigger
trigger-guard-left
trigger-guard-right
pump
pump-mount-1
bearing-solenoid-mount
PICON-OF_ver_37-pulsanti lato sinistro_B
PICON-OF_ver_37-pulsanti lato sinistro_C
PICON-OF_ver_37-perno fermo bq25185
PICON-OF_ver_37-perno fermo grilletto -rear
PICON-OF_ver_37-perno fermo switch
PICON-OF_ver_37-perno fermo step-down
PICON-OF_ver_37-perno fermo power-path
PICON-OF_ver_37-perno fermo mp3429
PICON-OF_ver_37-perno fermo driver
