alessandro-satanassi/OpenFIRE-PICON-ESP32/PICON-OG/STL/right-side-for-universal-pcb.stl

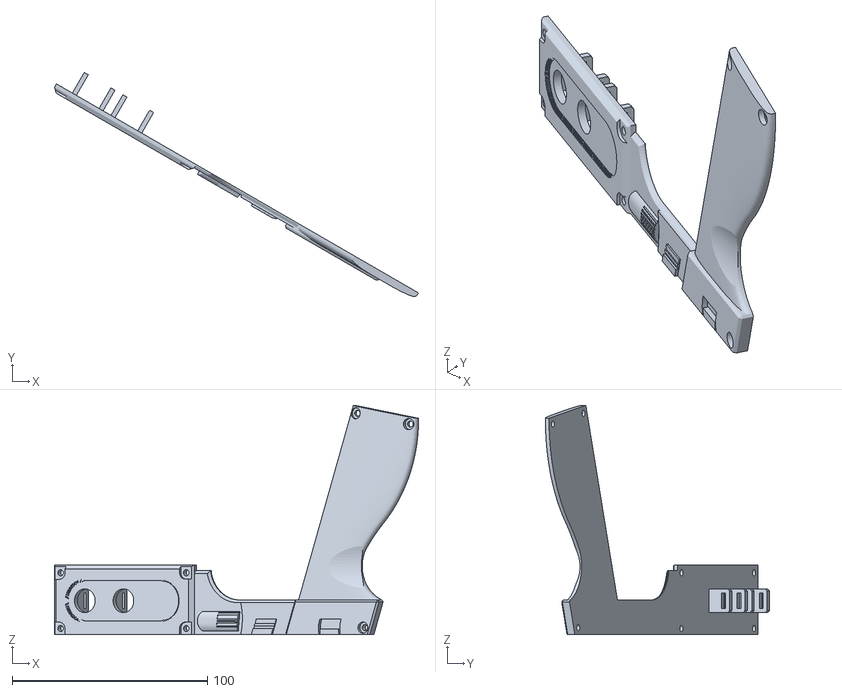
[picture p288: CAD file, 2025-09-09]
PICON-OG/STL/right-side-for-universal-pcb.stl
186.5 x 114.8 x 117.5
