alessandro-satanassi/OpenFIRE-PICON-ESP32/PICON-OG/STL/frame-brace.stl

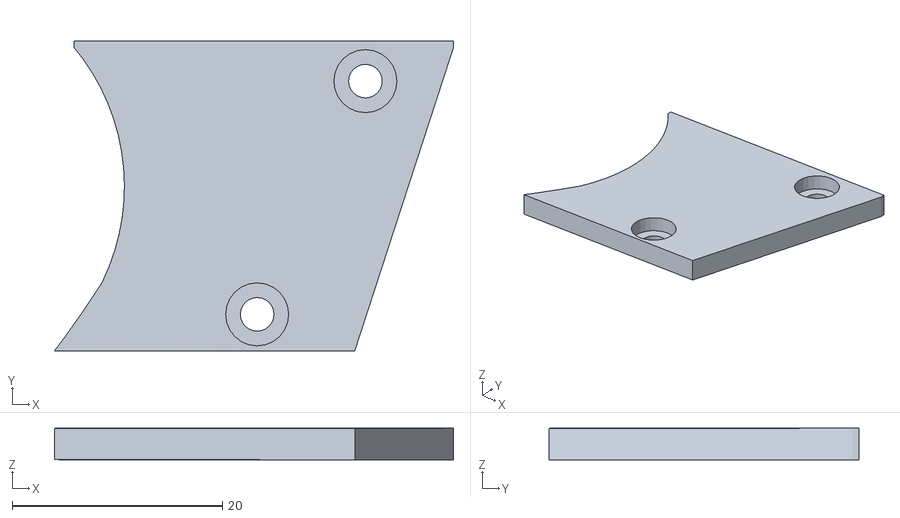
[picture p289: CAD file, 2025-09-09]
PICON-OG/STL/frame-brace.stl
38.0 x 29.5 x 3.00
