alessandro-satanassi/OpenFIRE-PICON-ESP32/PICON-OG/STL/back-exposed-rgb-led.stl

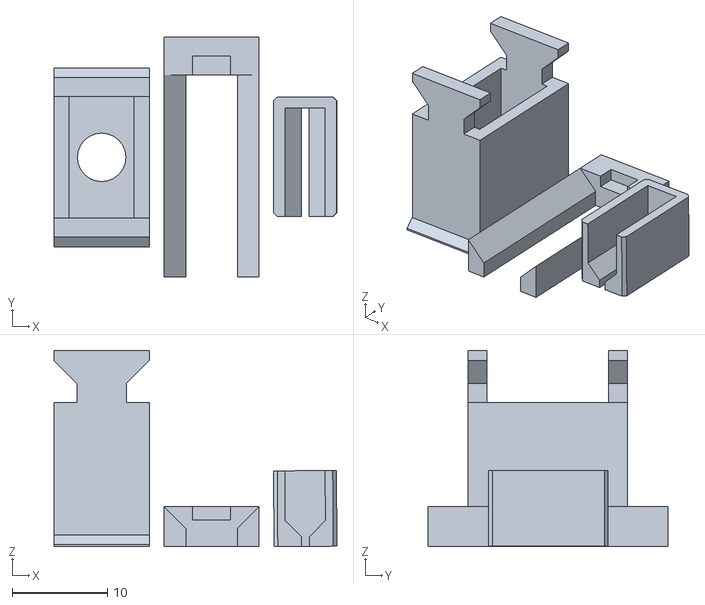
[picture p290: CAD file, 2025-09-09]
PICON-OG/STL/back-exposed-rgb-led.stl
29.8 x 25.2 x 20.6
