alessandro-satanassi/OpenFIRE-PICON-ESP32/PICON-OG/STL/slide-no-display-with-supports.stl

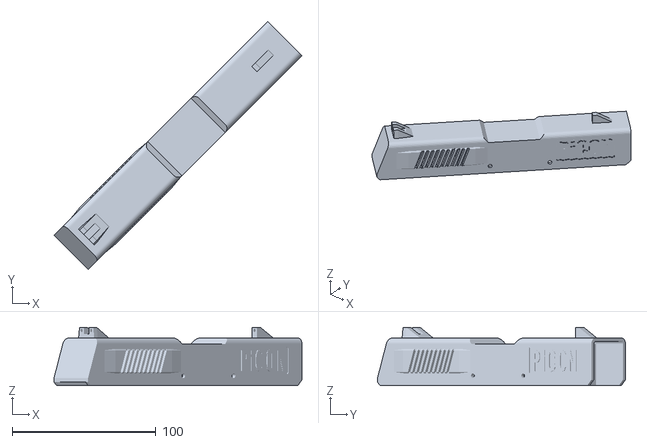
[picture p291: CAD file, 2025-09-09]
PICON-OG/STL/slide-no-display-with-supports.stl
172.7 x 172.7 x 40.4
