alessandro-satanassi/OpenFIRE-PICON-ESP32/FreeCAD/PICON-OF_ver_34_prova_spazio_switch_alette-Extrude prova spazio switch.stl

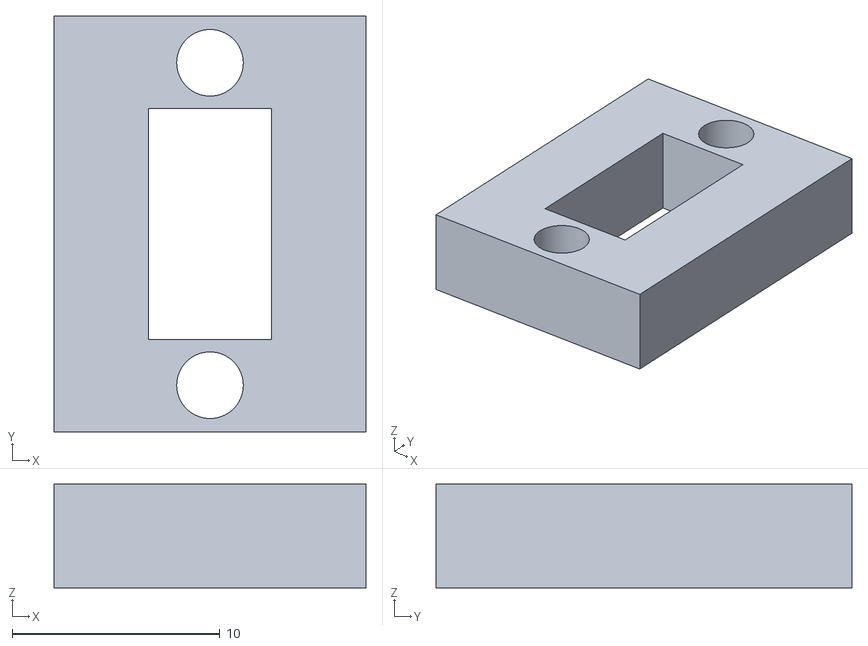
[picture p292: CAD file, 2026-03-09]
FreeCAD/PICON-OF_ver_34_prova_spazio_switch_alette-Extrude prova spazio switch.stl
15.0 x 20.0 x 5.00
