alessandro-satanassi/OpenFIRE-PICON-ESP32/PICON-OG/STL/nav-module-buttons.stl

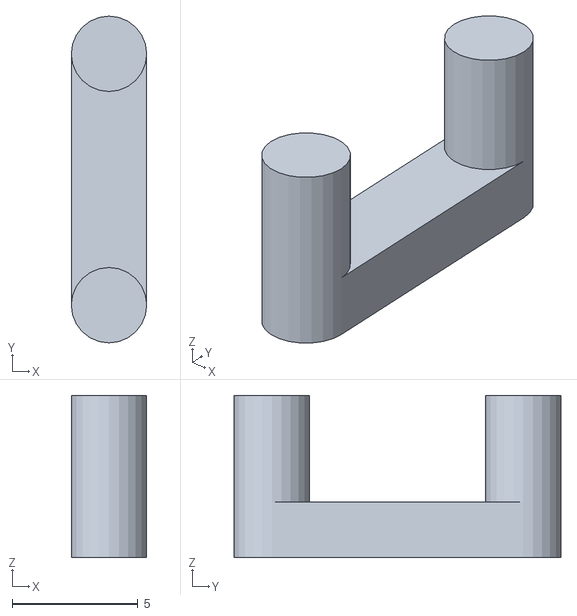
[picture p293: CAD file, 2025-09-09]
PICON-OG/STL/nav-module-buttons.stl
3.00 x 13.0 x 6.44
