alessandro-satanassi/OpenFIRE-PICON-ESP32/FreeCAD/PICON-OF_ver_33-lato DXPocket012.3mf

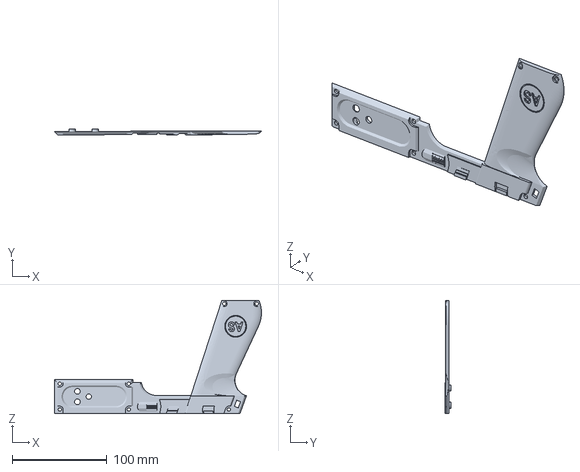
[picture p294: CAD file, 2026-03-09]
FreeCAD/PICON-OF_ver_33-lato DXPocket012.3mf
218.6 x 6.15 x 119.6 mm
