alessandro-satanassi/OpenFIRE-PICON-ESP32/FreeCAD/prove_dimensioni_senza led.FCStd

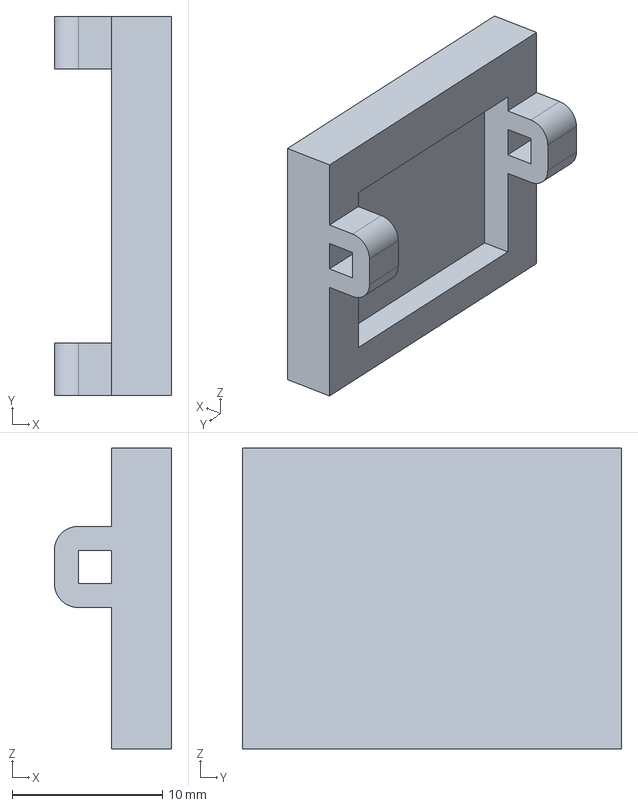
[picture p295: CAD file, 2026-03-09]
FreeCAD/prove_dimensioni_senza led.FCStd
7.80 x 25.2 x 20.0 mm
