alessandro-satanassi/OpenFIRE-PICON-ESP32/FreeCAD/PICON-OF_ver_25-lato SXPocket003.stl

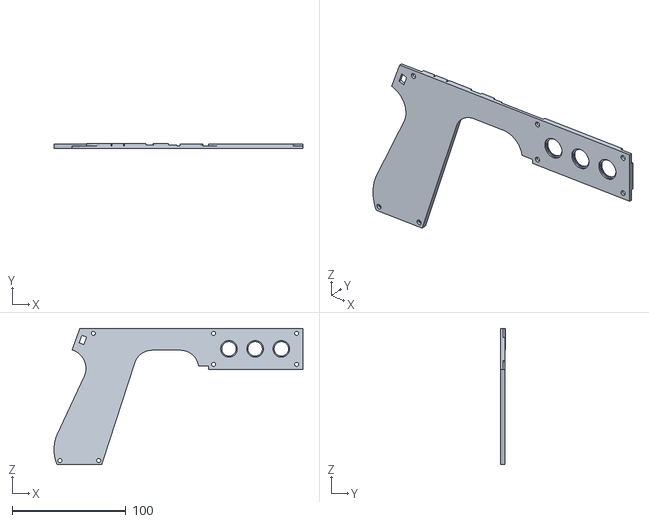
[picture p296: CAD file, 2026-03-09]
FreeCAD/PICON-OF_ver_25-lato SXPocket003.stl
218.6 x 4.00 x 119.6
