alessandro-satanassi/OpenFIRE-PICON-ESP32/FreeCAD/prove_dimensioni-Cut003.stl

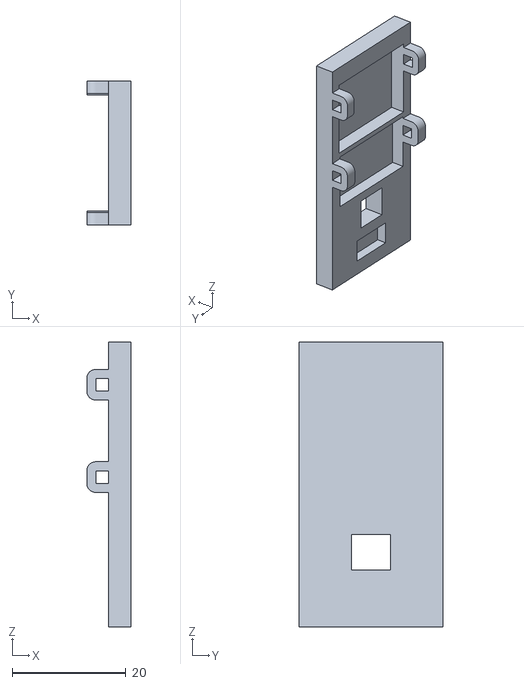
[picture p298: CAD file, 2026-03-09]
FreeCAD/prove_dimensioni-Cut003.stl
7.80 x 25.2 x 50.0
