alessandro-satanassi/OpenFIRE-PICON-ESP32/FreeCAD/case_ir_led_tx.FCStd

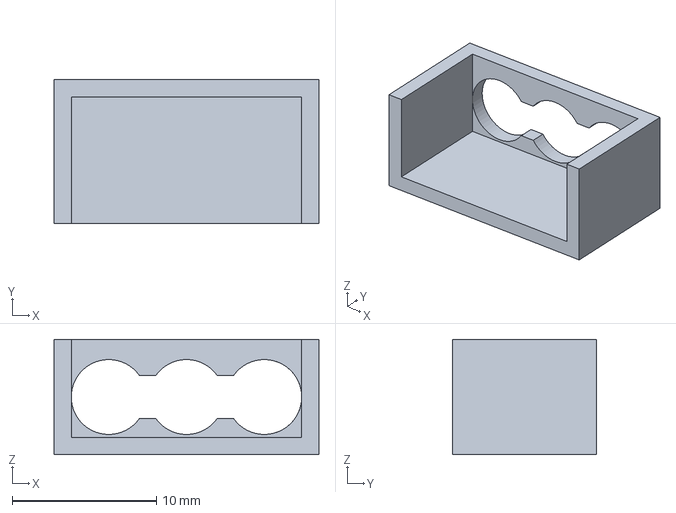
[picture p299: CAD file, 2026-03-09]
FreeCAD/case_ir_led_tx.FCStd
18.4 x 10.0 x 8.00 mm
