alessandro-satanassi/OpenFIRE-PICON-ESP32/FreeCAD/PICON-OF_ver_53_BIS.FCStd

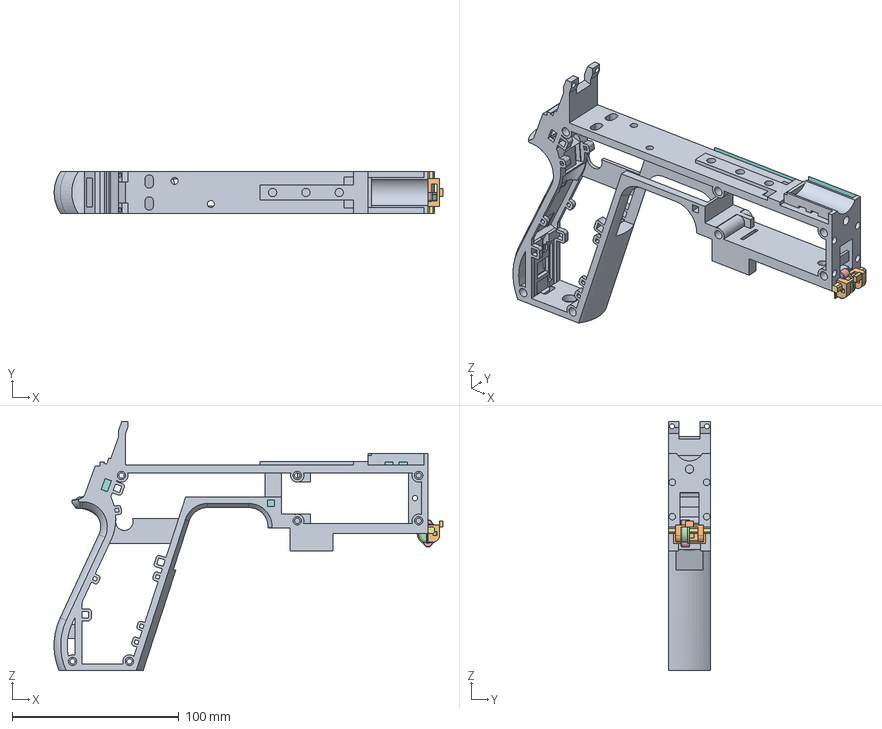
[picture p300: CAD file, 2026-03-09]
FreeCAD/PICON-OF_ver_53_BIS.FCStd
233.6 x 25.2 x 149.8 mm
perno fermo rumble e driver solenoide
supporto per neopixel
blocco switch
pulsanti lato sinistro
pulsanti lato destro
perno fermo neopixel
perno fermo switch - caricabatterie - grilletto
CopyCut
