alessandro-satanassi/OpenFIRE-PICON-ESP32/web/images/assembly.png

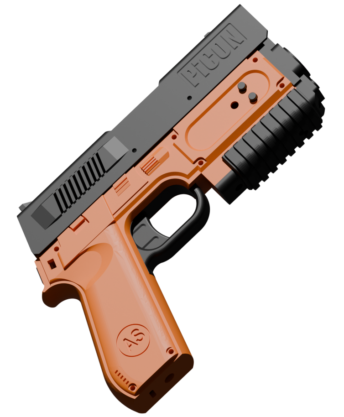
web/images/assembly.png
